NormSohl/openprinttag-weigh-station/docs/quickref-weighing.md

# Quick Reference — Weighing a Spool

*Print this page and keep it at the station. Full detail: [user-manual.md](user-manual.md).*

Weigh after every print if at all possible — plus before one, or any other
time.

## Steps

1. **Place the spool on the scale.** The scale starts reading the moment the
   spool lands.
2. **Wait a second or two.** The display settles on the spool number,
   material, and remaining weight.
3. **Remove the spool.** The reading is already saved. The display returns
   to idle.

**Weigh it when you return it — every time, if at all possible.** That's
what keeps remaining weight accurate for the next person. Weighing when you
take it out is useful too, and you can weigh a spool any other time you want
to check on it — none of that is required the way returning it is.

## What the display is telling you

| Screen | Meaning |
|---|---|
| Green, "Place spool to begin" | Idle — ready to go |
| "Weighing…" | Reading the load cell — don't lift yet |
| Spool #, material, grams, "Weight recorded" | Done — safe to remove |
| "Registered! / NEEDS ONBOARDING" | This is a brand-new tag — see the Onboarding quick-ref |
| Red "Read Error" | Reposition the spool so the tag centers over the reader |
| Orange, "Scale not calibrated" | Weights aren't trustworthy yet — flag for an admin |

## If something looks wrong

- **Read error every time in the same spot:** the tag antenna may be cracked —
  flag the spool for a new tag.
- **Weight looks way off:** don't fix it yourself — tell an admin, the scale
  may need recalibrating.
