NormSohl/openprinttag-weigh-station/src/web_app.cpp

// SPDX-License-Identifier: GPL-3.0-or-later
// Copyright (C) 2026 Norm Sohl

#include "web_app.h"
#include <Arduino.h>
#include <WiFi.h>
#include <ESPmDNS.h>
#include <ESPAsyncWebServer.h>
#include <LittleFS.h>
#include <vector>
#include <algorithm>
#include <string.h>
#include <stdlib.h>   // strtoull
#include "config.h"
#include "device_state.h"
#include "opt_tag.h"
#include "store.h"
#include "config_store.h"
#include "api_key.h"
#include "display_tz.h"
#include "station_name.h"
#include "last_onboard.h"
#include "last_stock.h"

// ── Shared globals (defined in main.cpp) ──────────────────────────────────────
extern volatile DeviceState gState;
extern SemaphoreHandle_t    gStateMutex;
extern volatile float       gWeightGrams;
extern SemaphoreHandle_t    gWeightMutex;
extern uint8_t              gTagUid[8];
extern OptMain              gTagMain;
extern SemaphoreHandle_t    gTagMutex;
// Set here (Start/Stop on /erase), consumed by nfcTask/syncTask — see main.cpp.
extern volatile bool        gEraseModeActive;
extern volatile uint32_t    gEraseModeActivityMs;
extern volatile bool        gWriteMainPending;
extern volatile int         gSpoolId;
extern volatile bool        gSpoolNeedsOnboarding;
extern volatile bool        gScaleCalibrated;
extern volatile bool        gCalZeroReq;
extern volatile float       gCalSetGrams;
// SoftAP SSID when the station fell back to its own AP; empty in station
// mode. Reported by /api/status.
extern char                 gApSsid[24];
extern volatile bool        gClockSet;

static AsyncWebServer sServer(80);

// Forward decl -- defined below, needed by the SSE push logic here so both
// the broadcast (webAppNotifyStateChanged) and the per-client catch-up
// (sEvents.onConnect(), registered in webAppBegin()) can send the SAME
// authoritative value.
static int currentSpool();

// Server-push channel for state changes, so a page like /onboard, a spool's
// detail page, or the Inventory page can react the instant something changes
// instead of polling. The message body carries the values a listener needs
// to decide for itself, not a bare ping -- a live test found that a bare
// ping requiring a follow-up fetch('/api/status') could silently stall: this
// server holds very few concurrent connections, and the fetch was losing the
// race against the already-open SSE stream for one. Format:
// "<spool id>,<needs_onboarding>,<audit phase 0/1/2>,<audit found>,<audit total>"
// (spool id -1 when nothing is on the scale). Each listener reads only the
// fields it cares about: /onboard and /spool watch the id; the Inventory
// page also watches the audit fields, and skips reloading entirely when
// none of the fields it cares about actually changed -- a live test found
// that reloading the whole page on every push (including ones that changed
// nothing this page shows, like reweighing an already-found spool during an
// audit) made a full-page flash on every placement, fighting anyone trying
// to scroll the list.
static AsyncEventSource sEvents("/events");

// Shared with handleRoot()'s own audit banner render, so the two can never
// silently drift into disagreeing about what "found" means.
static void auditSummary(AuditPhase& phase, uint32_t& total, uint32_t& found) {
    phase = storeAuditPhase();
    total = 0; found = 0;
    if (phase == AuditPhase::Idle) return;
    char startTs[25] = {};
    storeAuditStartTs(startTs, sizeof(startTs));
    SpoolRecord rr;
    for (size_t i = 0; i < storeSpoolCount(); i++) {
        if (!storeSpoolAt(i, rr)) continue;
        if (rr.retired || rr.remaining_g <= 1.0f) continue;
        total++;
        if (strcmp(rr.last_ts, startTs) >= 0) found++;
    }
}

static String currentScaleSpoolPayload() {
    int id = currentSpool();
    bool needsOb = false;
    if (id > 0) {
        SpoolRecord r;
        if (storeGetSpool((uint32_t)id, r)) needsOb = r.needs_ob;
    }
    AuditPhase phase; uint32_t total, found;
    auditSummary(phase, total, found);
    return String(id) + "," + (needsOb ? "1" : "0") + ","
         + String((int)phase) + "," + String(found) + "," + String(total);
}

void webAppNotifyStateChanged() {
    auto st = sEvents.send(currentScaleSpoolPayload().c_str(), "state");
    Serial.printf("[sse] state-change push: %u client(s), status=%d\n",
                  (unsigned)sEvents.count(), (int)st);
}

// ── Small HTML helpers ────────────────────────────────────────────────────────

// ── Auth ──────────────────────────────────────────────────────────────────────
// Applied to state-changing endpoints only; GETs stay open so dashboards and
// scrapers need no credentials. See api_key.h for the threat model and why an
// unset key deliberately leaves everything open.
//
// Returns true if the request may proceed. On refusal it has already sent the
// 401, so the caller must simply return.
static bool authOk(AsyncWebServerRequest* req) {
    if (!apiKeyIsSet()) return true;                 // not configured: open
    const String key = apiKeyGet();
    if (req->hasHeader("X-API-Key") && req->header("X-API-Key") == key) return true;
    if (req->hasParam("key") && req->getParam("key")->value() == key)   return true;
    // Basic auth accepts any username: the secret is the password. Lets browsers
    // prompt natively and `curl -u :secret` work without a header.
    if (req->authenticate("", key.c_str()) ||
        req->authenticate("admin", key.c_str()))     return true;
    req->requestAuthentication();                    // sends 401 + WWW-Authenticate
    return false;
}

// 32 lowercase hex chars (no dashes, matching the store's uuid format) -> 16
// bytes. Used only for catalog-sourced UUIDs coming off the onboard form —
// false on anything malformed, and the caller simply leaves the tag field
// untouched rather than writing a bogus identity.
static bool hex32ToBytes(const String& hex, uint8_t out[16]) {
    if (hex.length() != 32) return false;
    for (int i = 0; i < 16; i++) {
        char b[3] = { hex[i * 2], hex[i * 2 + 1], 0 };
        char* end = nullptr;
        long v = strtol(b, &end, 16);
        if (end != b + 2) return false;
        out[i] = (uint8_t)v;
    }
    return true;
}

static String esc(const char* s) {
    String o;
    for (const char* p = s; *p; ++p) {
        switch (*p) {
            case '&': o += "&amp;";  break;
            case '<': o += "&lt;";   break;
            case '>': o += "&gt;";   break;
            case '"': o += "&quot;"; break;
            default:  o += *p;       break;
        }
    }
    return o;
}

static const char* STYLE =
    "<style>"
    // -webkit-text-size-adjust stops iOS inflating text when a phone is turned
    // to landscape, which otherwise reflows every page unpredictably.
    "body{font-family:system-ui,sans-serif;margin:0;background:#111;color:#eee;"
    "-webkit-text-size-adjust:100%}"
    // Flex, not float. Eight nav links floated right do not fit a phone: they
    // collide with the title and wrap into an unreadable stack. Flex-wrap drops
    // them onto their own line instead, and margin-left:auto keeps them right-
    // aligned whenever there IS room.
    "header{background:#1c2b1c;padding:12px 16px;font-size:20px;font-weight:600;"
    "display:flex;flex-wrap:wrap;align-items:baseline}"
    "header nav{display:flex;flex-wrap:wrap;gap:4px 16px;margin-left:auto}"
    "header a{color:#8f8;text-decoration:none;font-size:15px;font-weight:400;"
    "padding:4px 0}"
    "header a.active{color:#fff;font-weight:600;border-bottom:2px solid #8f8}"
    // overflow-x on main, not on the page: a table wider than the phone scrolls
    // inside the content area instead of sliding the whole layout sideways,
    // which is the usual way a page "looks broken" on mobile.
    "main{padding:18px;max-width:760px;margin:0 auto;overflow-x:auto}"
    "table{border-collapse:collapse;width:100%}"
    "th,td{padding:6px 10px;text-align:left;border-bottom:1px solid #333}"
    "th{color:#9c9}"
    ".sw{display:inline-block;width:14px;height:14px;border-radius:3px;vertical-align:middle;margin-right:6px;border:1px solid #000}"
    // "No colour assigned" — a crossed-out square, so it cannot be misread as a
    // black filament. The stroke is a gradient rather than a glyph or an SVG so
    // it stays crisp at 14px and needs no extra request.
    ".sw0{background:#1c1c1c;border-color:#666;background-image:"
    "linear-gradient(to top right,transparent 45%,#8a8a8a 45%,#8a8a8a 55%,transparent 55%)}"
    ".ob{color:#fd6}"
    ".inv-row{cursor:pointer}"
    ".inv-row:hover{background:#1a1a1a}"
    ".arrow{display:inline-block;font-size:22px;line-height:1;color:#8f8}"
    "form label{display:block;margin:12px 0 4px;color:#9c9}"
    "select,input{font-size:16px;padding:8px;width:100%;box-sizing:border-box;background:#222;color:#eee;border:1px solid #444;border-radius:5px}"
    "button{margin-top:16px;font-size:16px;padding:10px 18px;background:#2a5;color:#000;border:0;border-radius:6px;cursor:pointer}"
    "button.sec{background:#345;color:#eee}"
    ".card{background:#1a1a1a;border:1px solid #333;border-radius:8px;padding:14px;margin-bottom:14px}"
    ".big{font-size:28px;font-weight:700}"
    ".muted{color:#888}"
    // Spec strip: the numbers onboarding stored, which are otherwise typed once
    // into the form and never seen again. Flex-wrap rather than a table so it
    // reflows to one item per line on a phone instead of scrolling.
    ".spec{display:flex;flex-wrap:wrap;gap:5px 16px;font-size:14px;color:#aaa;margin-top:10px}"
    ".spec b{color:#ddd;font-weight:600}"
    // Phone-width tuning. Tighter cells and slightly smaller type let the wider
    // tables (Usage has five columns) fit without scrolling at all on most
    // handsets; the ones that still don't fit scroll inside main.
    "@media(max-width:520px){"
      "main{padding:12px}"
      "header{font-size:18px;padding:10px 12px}"
      "th,td{padding:5px 6px;font-size:14px}"
      ".big{font-size:24px}"
      "button{width:100%;padding:12px 18px}"
      "button.sec{width:auto}"
    "}"
    "</style>";

// ── Onboard page: OpenPrintTag catalog search widget ──────────────────────────
// Cascading Vendor -> Material type -> Material combo boxes that live-search
// github.com/OpenPrintTag/openprinttag-database straight from the browser (the
// device is never in the loop — no firmware cost, no extra heap). A pick fills
// the hidden cat_* fields in the onboard form with the vendor's own GTIN, the
// three OPT identity UUIDs, and real print/bed temps when the material file
// carries them, instead of whatever a person free-types.
//
// Prototyped and verified against the live DB at tools/opt-catalog/prototype.html
// before landing here; this is the same logic, minus the standalone page chrome.
static const char* CATALOG_STYLE =
    "<style>"
    ".cat-status{font-size:12px;color:#888;margin:6px 0 14px}"
    ".cat-status b{color:#eee}"
    ".cat-status.err b{color:#fd6}"
    ".cat-field{margin-bottom:12px;position:relative}"
    ".cat-field.disabled{opacity:.45}"
    ".cat-field label{display:block;font-size:12px;color:#9c9;text-transform:uppercase;"
      "letter-spacing:.04em;margin-bottom:4px}"
    ".cat-input.picked{border-color:#2a5}"
    ".cat-panel{display:none;position:absolute;left:0;right:0;top:calc(100% + 2px);z-index:20;"
      "background:#1a1a1a;border:1px solid #444;border-radius:6px;max-height:260px;"
      "overflow-y:auto;box-shadow:0 10px 30px #0008}"
    ".cat-group{padding:6px 10px 2px;font-size:11px;color:#888;text-transform:uppercase;letter-spacing:.04em}"
    ".cat-divider{border-top:1px solid #333;margin:2px 0}"
    ".cat-empty{padding:10px;color:#888;font-size:13px}"
    ".cat-row{padding:10px;display:flex;justify-content:space-between;align-items:center;gap:8px;cursor:pointer}"
    ".cat-row:active,.cat-row.hi{background:#20263a}"
    ".cat-row .meta{color:#888;font-size:12px;white-space:nowrap}"
    "</style>";

static const char* CATALOG_SCRIPT = R"OPTJS(<script>
(function(){
const OWNER="OpenPrintTag", REPO="openprinttag-database", BRANCH="main";
const API=`https://api.github.com/repos/${OWNER}/${REPO}`;
const RAW=`https://raw.githubusercontent.com/${OWNER}/${REPO}/${BRANCH}/data`;
const PKG_PREFIX="data/material-packages/";
const TYPE_ENUM_URL="https://raw.githubusercontent.com/OpenPrintTag/openprinttag-specification/main/data/material_type_enum.yaml";

const $ = s => document.querySelector(s);
const statusEl=$("#cat-status"), resolvedEl=$("#cat-resolved");
let PACKAGES = [];
let brandNames = new Map();

function esc(s){ return String(s==null?"":s).replace(/[&<>"]/g, c=>({"&":"&amp;","<":"&lt;",">":"&gt;",'"':"&quot;"}[c])); }
function setStatus(html, err){ statusEl.className="cat-status"+(err?" err":""); statusEl.innerHTML=html; }

// ── minimal YAML subset parser (maps, nested maps, lists of scalars/maps) ────
function parseYaml(text){
  const lines=text.split(/\r?\n/).map(l=>l.replace(/\s+$/,"")).filter(l=>l.trim()!==""&&!/^\s*#/.test(l));
  let pos=0; const indentOf=l=>l.length-l.trimStart().length;
  const scalar=v=>{v=v.trim();
    if((v[0]==="'"&&v.endsWith("'"))||(v[0]==='"'&&v.endsWith('"')))return v.slice(1,-1);
    if(/^-?\d+$/.test(v))return v.length>15?v:parseInt(v,10);
    if(/^-?\d*\.\d+$/.test(v))return parseFloat(v); return v;};
  function parseMap(indent){const obj={};
    while(pos<lines.length){const line=lines[pos],ind=indentOf(line),t=line.trim();
      if(ind<indent)break; if(t.startsWith("- "))break;
      const m=t.match(/^([^:]+):\s*(.*)$/); if(!m){pos++;continue;}
      const key=m[1].trim(),val=m[2]; pos++;
      if(val===""){const nx=lines[pos];
        if(nx!==undefined){const ni=indentOf(nx);
          if(nx.trim().startsWith("- ")&&ni>=indent)obj[key]=parseList(ni);
          else if(ni>indent)obj[key]=parseMap(ni); else obj[key]=null;
        }else obj[key]=null;
      }else obj[key]=scalar(val);}
    return obj;}
  function parseList(indent){const arr=[];
    while(pos<lines.length){const line=lines[pos],ind=indentOf(line),t=line.trim();
      if(ind<indent||!t.startsWith("- "))break;
      const rest=t.slice(2),m=rest.match(/^([^:]+):\s*(.*)$/); pos++;
      if(m){const item={};item[m[1].trim()]=m[2]===""?null:scalar(m[2]);
        const child=ind+2;
        if(pos<lines.length&&indentOf(lines[pos])>=child&&!lines[pos].trim().startsWith("- "))
          Object.assign(item,parseMap(child));
        arr.push(item);}else arr.push(scalar(rest));}
    return arr;}
  return parseMap(0);
}
async function fetchText(url){ const r=await fetch(url,{cache:"no-store"}); if(!r.ok) throw new Error(`${r.status} ${r.statusText} for ${url}`); return r.text(); }
async function fetchYaml(url){ return parseYaml(await fetchText(url)); }

// ── index: one tree fetch (cached by data_hash) + one small type-enum fetch ──
async function loadIndex(){
  let hash="nohash";
  try { const man=await fetchText(`${RAW}/manifest.yaml`); hash=(man.match(/data_hash:\s*(\S+)/)||[])[1]||"nohash"; } catch(e){}

  const cacheKey="opt_pkgindex2_"+hash;
  const cached=localStorage.getItem(cacheKey);
  if(cached){ PACKAGES=JSON.parse(cached); setStatus(`${PACKAGES.length.toLocaleString()} packages <span class="muted">(cached)</span>`); }
  else {
    setStatus("Fetching catalog tree from GitHub (one request)&hellip;");
    const tree=JSON.parse(await fetchText(`${API}/git/trees/${BRANCH}?recursive=1`));
    PACKAGES=(tree.tree||[]).filter(e=>e.type==="blob"&&e.path.startsWith(PKG_PREFIX)&&e.path.endsWith(".yaml"))
      .map(e=>{const rel=e.path.slice(PKG_PREFIX.length); const brand=rel.split("/")[0];
        const file=rel.split("/").pop().replace(/\.yaml$/,"");
        return {path:e.path, brand, file};});
    try { localStorage.setItem(cacheKey, JSON.stringify(PACKAGES)); } catch(e){}
    for(let i=localStorage.length-1;i>=0;i--){ const k=localStorage.key(i); if(k&&k.startsWith("opt_pkgindex2_")&&k!==cacheKey) localStorage.removeItem(k); }
    setStatus(`${PACKAGES.length.toLocaleString()} packages <span class="muted">(fresh)</span>`);
  }

  // Type tokens: scan filenames for exact hyphen-delimited matches against the
  // OPT's own material_type_enum abbreviations. No per-item fetch. ~93% of
  // packages resolve a type; the rest fall into "Other" honestly rather than
  // guessing.
  try {
    const enumText=await fetchText(TYPE_ENUM_URL);
    const ABBR=new Set([...enumText.matchAll(/abbreviation:\s*(\S+)/g)].map(m=>m[1].toLowerCase()));
    PACKAGES.forEach(p=>{ p.typeTok = p.file.split("-").find(t=>ABBR.has(t)) || null; });
  } catch(e){ PACKAGES.forEach(p=>p.typeTok=null); }

  prefetchBrandNames();  // progressive; does not block the UI
}

async function prefetchBrandNames(){
  const slugs=[...new Set(PACKAGES.map(p=>p.brand))];
  await Promise.all(slugs.map(async slug=>{
    try { const b=await fetchYaml(`${RAW}/brands/${slug}.yaml`); if(b.name) brandNames.set(slug,b.name); } catch(e){}
  }));
  vendorCombo.renderPanel();  // refresh labels if the panel happens to be open
}

// ── small helpers ──────────────────────────────────────────────────────────
function prettifySlug(s){ return s.replace(/-/g," ").replace(/\b\w/g,c=>c.toUpperCase()); }
function prettyName(file, brand){
  let n=file.replace(/-/g," ");
  if(n.toLowerCase().startsWith(brand.replace(/-/g," ").toLowerCase()+" ")) n=n.slice(brand.length+1);
  return n.replace(/\b\w/g,c=>c.toUpperCase());
}
function weightBadge(file){
  let m=file.match(/-(\d+(?:\.\d+)?kg)(?:-(spool|old-spool|refill))?$/i);
  if(m) return m[1].toUpperCase().replace("KG"," kg") + (m[2]?` (${m[2].replace("-"," ")})`:"");
  m=file.match(/-(\d+)-(spool|old-spool|refill|no-spool)$/i);
  if(m) return `${m[1]} g` + (m[2]!=="spool" ? ` (${m[2].replace("-"," ")})` : "");
  return null;
}
function loadMru(key){ try { return JSON.parse(localStorage.getItem(key)||"[]"); } catch(e){ return []; } }
function pushMru(key,val,cap){ let a=loadMru(key).filter(v=>v!==val); a.unshift(val); a=a.slice(0,cap); localStorage.setItem(key,JSON.stringify(a)); }

// ── candidate lists (all client-side, zero extra fetches) ───────────────────
function vendorCandidates(){
  const counts=new Map();
  for(const p of PACKAGES) counts.set(p.brand,(counts.get(p.brand)||0)+1);
  return [...counts.entries()]
    .map(([slug,count])=>({value:slug, label:brandNames.get(slug)||prettifySlug(slug), count}))
    .sort((a,b)=>a.label.localeCompare(b.label));
}
function typeCandidatesFor(vendorSlug){
  const counts=new Map();
  for(const p of PACKAGES){ if(p.brand!==vendorSlug) continue; const tok=p.typeTok||"other"; counts.set(tok,(counts.get(tok)||0)+1); }
  const total=[...counts.values()].reduce((a,b)=>a+b,0);
  const rows=[{value:"", label:"All types", count:total}];
  for(const [tok,count] of [...counts.entries()].sort((a,b)=>b[1]-a[1]))
    rows.push({value:tok, label: tok==="other" ? "Other / unspecified" : tok.toUpperCase(), count});
  return rows;
}
function materialCandidatesFor(vendorSlug, typeTok){
  return PACKAGES.filter(p=>p.brand===vendorSlug && (!typeTok || p.typeTok===typeTok))
    .map(p=>{
      const badge=weightBadge(p.file);
      return { value:p.path, label:prettyName(p.file,p.brand)+(badge?` — ${badge}`:"") };
    })
    .sort((a,b)=> a.label.localeCompare(b.label));
}

// ── reusable combo box: MRU (if any) → divider → list; type-to-filter ────────
function makeCombo(fieldId, inputId, panelId, placeholder){
  const field=$(fieldId), input=$(inputId), panel=$(panelId);
  let candidatesFn=()=>[], mruKey=null, mruCap=0, onPick=()=>{};
  let rows=[], hiIdx=-1;

  function setSource(cfg){ candidatesFn=cfg.candidatesFn; mruKey=cfg.mruKey||null; mruCap=cfg.mruCap||0; onPick=cfg.onPick; }
  function rowHtml(c,i){
    return `<div class="cat-row${i===hiIdx?" hi":""}" data-i="${i}">`+
      `<span>${esc(c.label)}</span>`+
      (c.count!=null?`<span class="meta">${c.count}</span>`:"")+`</div>`;
  }
  function renderPanel(){
    const all=candidatesFn();
    const filt=input.value.trim().toLowerCase();
    const terms=filt.split(/\s+/).filter(Boolean);
    const match=c=>terms.every(t=>c.label.toLowerCase().includes(t));
    const mruVals=(!filt && mruKey) ? loadMru(mruKey) : [];
    const mruRows=mruVals.map(v=>all.find(c=>c.value===v)).filter(Boolean);
    let rest=all.filter(c=>!mruRows.includes(c));
    if(filt) rest=rest.filter(match);
    rest=rest.slice(0,80);
    rows=[...mruRows, ...rest];
    hiIdx=-1;
    panel.innerHTML =
      (mruRows.length? `<div class="cat-group">Recently used</div>${mruRows.map((c,i)=>rowHtml(c,i)).join("")}<div class="cat-divider"></div>` : "") +
      (rest.length ? rest.map((c,i)=>rowHtml(c,mruRows.length+i)).join("")
                   : (all.length ? `<div class="cat-empty">No matches</div>` : `<div class="cat-empty">Nothing here yet</div>`));
  }
  function show(){ if(input.disabled) return; renderPanel(); panel.style.display="block"; }
  function hide(){ panel.style.display="none"; }
  function pick(c){
    input.value=c.label; input.classList.add("picked"); hide();
    if(mruKey) pushMru(mruKey, c.value, mruCap);
    onPick(c);
  }
  input.addEventListener("focus", show);
  input.addEventListener("input", ()=>{ input.classList.remove("picked"); show(); });
  input.addEventListener("blur", ()=> setTimeout(hide, 150));
  input.addEventListener("keydown", e=>{
    if(panel.style.display!=="block") return;
    if(e.key==="ArrowDown"){ e.preventDefault(); hiIdx=Math.min(hiIdx+1, rows.length-1); renderHi(); }
    else if(e.key==="ArrowUp"){ e.preventDefault(); hiIdx=Math.max(hiIdx-1, 0); renderHi(); }
    else if(e.key==="Enter"){ e.preventDefault(); if(rows[hiIdx]) pick(rows[hiIdx]); }
    else if(e.key==="Escape"){ hide(); }
  });
  function renderHi(){ panel.querySelectorAll(".cat-row").forEach(r=>r.classList.toggle("hi", +r.dataset.i===hiIdx)); }
  panel.addEventListener("mousedown", e=>{
    const row=e.target.closest(".cat-row[data-i]"); if(!row) return;
    e.preventDefault(); pick(rows[+row.dataset.i]);
  });
  function reset(){ input.value=""; input.classList.remove("picked"); }
  function enable(text){ input.disabled=false; input.placeholder=text||placeholder; field.classList.remove("disabled"); }
  function disable(text){ input.disabled=true; reset(); input.placeholder=text; field.classList.add("disabled"); }
  return { setSource, reset, enable, disable, renderPanel };
}

const vendorCombo   = makeCombo("#cat-field-vendor",   "#cat-in-vendor",   "#cat-panel-vendor",   "Type or tap to browse vendors…");
const typeCombo     = makeCombo("#cat-field-type",     "#cat-in-type",     "#cat-panel-type",     "Type or tap to browse types…");
const materialCombo = makeCombo("#cat-field-material", "#cat-in-material", "#cat-panel-material", "Type or tap to browse materials…");
typeCombo.disable("Pick a vendor first");
materialCombo.disable("Pick a vendor first");

vendorCombo.setSource({
  candidatesFn: vendorCandidates,
  mruKey: "opt_mru_vendor", mruCap: 3,
  onPick(c){
    typeCombo.reset(); typeCombo.enable();
    materialCombo.disable("Pick a material type first");
    resolvedEl.innerHTML = "";
    typeCombo.setSource({
      candidatesFn: ()=>typeCandidatesFor(c.value),
      mruKey: "opt_mru_type", mruCap: 4,
      onPick(tc){
        materialCombo.reset(); materialCombo.enable();
        resolvedEl.innerHTML = "";
        materialCombo.setSource({
          candidatesFn: ()=>materialCandidatesFor(c.value, tc.value || null),
          onPick(mc){ resolvePick(mc.value); }
        });
      }
    });
  }
});

// ── resolve a picked package: package → material + container + brand, then
//    fill the form's hidden cat_* fields with the authoritative values ───────
function stripDash(u){ return (u||"").replace(/-/g,""); }
function setField(name, val){ const el=$("#cat-f-"+name); if(el) el.value = (val==null?"":val); }

async function resolvePick(pkgPath){
  resolvedEl.innerHTML = "<p class='muted'>Resolving…</p>";
  const brandSlug = pkgPath.slice(PKG_PREFIX.length).split("/")[0];
  try {
    const pkg = await fetchYaml(`${RAW}/material-packages/${brandSlug}/${pkgPath.split("/").pop()}`);
    const matSlug = pkg.material && pkg.material.slug, contSlug = pkg.container && pkg.container.slug;
    const [mat, cont, brand] = await Promise.all([
      matSlug  ? fetchYaml(`${RAW}/materials/${brandSlug}/${matSlug}.yaml`)       : Promise.resolve({}),
      contSlug ? fetchYaml(`${RAW}/material-containers/${contSlug}.yaml`)         : Promise.resolve({}),
                 fetchYaml(`${RAW}/brands/${brandSlug}.yaml`).catch(()=>({})),
    ]);
    applyPick(pkg, mat, cont, brand, brandSlug);
  } catch(e){
    resolvedEl.innerHTML = `<p class="ob">Couldn't resolve that pick: ${esc(e.message)}</p>`;
  }
}

function applyPick(pkg, mat, cont, brand, brandSlug){
  const rgba = (mat.primary_color && mat.primary_color.color_rgba) || "";
  const dia  = pkg.filament_diameter ? (pkg.filament_diameter/1000) : null;
  const tare = (cont.empty_weight != null) ? cont.empty_weight : null;
  const props = mat.properties || {};
  const tempKeys = ["min_print_temperature","max_print_temperature","min_bed_temperature","max_bed_temperature"];
  const haveTemps = tempKeys.every(k => typeof props[k] === "number");

  const vendor = brand.name || prettifySlug(brandSlug);
  const material = mat.name || "";
  const abbr = mat.abbreviation || mat.type || "";

  setField("cat_vendor", vendor);
  setField("cat_material", material);
  setField("cat_abbr", abbr);
  setField("cat_rgba", rgba ? rgba.replace("#","") : "");
  setField("cat_dia", dia);
  setField("cat_nom_g", pkg.nominal_netto_full_weight);
  setField("cat_empty_g", tare);
  setField("cat_gtin", pkg.gtin != null ? String(pkg.gtin) : "");
  setField("cat_pkg_uuid", stripDash(pkg.uuid));
  setField("cat_mat_uuid", stripDash(mat.uuid));
  setField("cat_brand_uuid", stripDash(brand.uuid));
  if (haveTemps) {
    setField("cat_print_min", props.min_print_temperature);
    setField("cat_print_max", props.max_print_temperature);
    setField("cat_bed_min",   props.min_bed_temperature);
    setField("cat_bed_max",   props.max_bed_temperature);
  } else {
    setField("cat_print_min",""); setField("cat_print_max","");
    setField("cat_bed_min","");   setField("cat_bed_max","");
  }
  $("#cat-source").value = "catalog";

  const sw = rgba ? `<span class="sw" style="background:${esc(rgba.slice(0,7))}"></span>` : "";
  const missTare = tare==null ? " <span class='ob'>&mdash; missing; capture below</span>" : "";
  resolvedEl.innerHTML =
    `<div class="card" style="border-color:#2a5;margin-top:10px">` +
    `<div style="font-size:17px;font-weight:600">${sw}${esc(vendor)} ${esc(material)}</div>` +
    `<p class="muted">${esc(abbr)}` +
      (dia!=null?` &middot; ${dia.toFixed(2)} mm`:``) +
      (pkg.nominal_netto_full_weight?` &middot; ${pkg.nominal_netto_full_weight} g`:``) +
      ` &middot; tare ${tare!=null?tare+" g":"unknown"}${missTare}</p>` +
    `<p class="muted" style="font-size:12px">GTIN ${pkg.gtin||"&mdash;"}` +
      (haveTemps ? ` &middot; print ${props.min_print_temperature}&ndash;${props.max_print_temperature}&deg;C` : ``) +
    `</p></div>`;
}

// ── boot ──────────────────────────────────────────────────────────────────
(async () => {
  try {
    await loadIndex();
    vendorCombo.enable();
    setStatus(`${PACKAGES.length.toLocaleString()} packages, ${new Set(PACKAGES.map(p=>p.brand)).size} vendors ready.`);
  } catch(e){
    setStatus(`Couldn't load the catalog: <b>${esc(e.message)}</b> &mdash; use manual entry below.`, true);
    const det = document.getElementById("cat-manual-details");
    if (det) det.open = true;
  }
})();
})();
</script>)OPTJS";

// One nav link, marked `active` when its href matches the current page.
static void navlink(String& h, const char* href, const char* label, const char* active) {
    h += "<a href='";
    h += href;
    h += (strcmp(href, active) == 0) ? "' class='active'>" : "'>";
    h += label;
    h += "</a>";
}

// `active` = the nav href for the current page (e.g. "/reorder"); "" = none.
static String head(const char* title, const char* active = "") {
    String h = "<!DOCTYPE html><html><head><meta charset='utf-8'>"
               "<meta name='viewport' content='width=device-width,initial-scale=1'>"
               "<title>";
    h += title;
    h += "</title>";
    h += STYLE;
    h += "</head><body><header>Weigh Station<nav>";
    navlink(h, "/",          "Inventory", active);
    navlink(h, "/onboard",   "Onboard",   active);
    navlink(h, "/reorder",   "Reorder",   active);
    navlink(h, "/stock",     "Stock List", active);
    navlink(h, "/usage",     "Usage",     active);
    navlink(h, "/erase",     "Erase Tag", active);
    navlink(h, "/config",    "Settings",  active);
    navlink(h, "/backup",    "Backup",    active);
    h += "</nav></header><main>";
    return h;
}

static const char* FOOT = "</main></body></html>";

// ── Current spool on the scale ────────────────────────────────────────────────
// Returns the local spool id if a tag is presently weighed/registered, else -1.
static int currentSpool() {
    xSemaphoreTake(gStateMutex, portMAX_DELAY);
    DeviceState s = gState;
    xSemaphoreGive(gStateMutex);
    bool live = (s == DeviceState::Present || s == DeviceState::WeighingAndSync ||
                 s == DeviceState::ReconcilingMainSection);
    return (live && gSpoolId > 0) ? gSpoolId : -1;
}

// Colour swatch, with a distinct "not assigned" rendering.
//
// alpha == 0 means no colour has been entered (see StoreEvent::rgba). Drawing
// that as #000000 would claim the spool is black, which is both wrong and
// unfalsifiable — nobody looking at the page could tell the difference. A
// crossed-out square says "unknown", and stays sayable if the colour is
// measured and filled in later.
static String swatch(const uint8_t rgba[4]) {
    if (rgba[3] == 0)
        return "<span class='sw sw0' title='No colour assigned'></span>";
    char b[80];
    snprintf(b, sizeof(b),
             "<span class='sw' style='background:#%02x%02x%02x'></span>",
             rgba[0], rgba[1], rgba[2]);
    return String(b);
}

// JSON value for a colour: the hex string, or null when none is assigned.
// Emitting "000000" would make an unassigned colour indistinguishable from
// black to every consumer, which is the same mistake the swatch avoids.
static String colorJson(const uint8_t rgba[4]) {
    if (rgba[3] == 0) return "null";
    char b[10];
    snprintf(b, sizeof(b), "\"%02x%02x%02x\"", rgba[0], rgba[1], rgba[2]);
    return String(b);
}

// One "label value" item for a .spec strip.
static String kv(const char* label, const String& value) {
    return "<span><b>" + String(label) + "</b> " + value + "</span>";
}

// The physical numbers a spool record carries: the tare, nominal weight and
// diameter chosen during onboarding.
//
// These exist only because someone typed them into the Onboard form, and until
// now nothing displayed them back — so a wrong spool profile (the commonest
// onboarding mistake, and the one that makes every later remaining-weight
// wrong) was invisible. Omit anything still zero rather than printing "0 g",
// which reads like a measurement instead of a blank — except the tare, which
// is shown even when missing: it is never meant to be unknown, and remaining
// is gross minus tare, so a missing one is a wrong number worth pointing at
// (the same reasoning as cost's "not recorded").
static String specStrip(const SpoolRecord& r) {
    String s;
    s += kv("Tare", r.empty_g > 0.0f ? String(r.empty_g, 0) + " g"
                                     : String("<span class='ob'>not recorded</span>"));
    if (r.nom_g   > 0.0f) s += kv("Nominal", String(r.nom_g,   0) + " g");
    if (r.dia     > 0.0f) s += kv("&Oslash;",  String(r.dia,   2) + " mm");
    return s;
}

// ── Dashboard: material roll-up + current spool ───────────────────────────────
static void handleRoot(AsyncWebServerRequest* req) {
    String p = head("Inventory", "/");

    if (!gScaleCalibrated)
        p += "<div class='card' style='border-color:#a70'>"
             "<b class='ob'>Scale not calibrated.</b> Weights will be wrong until "
             "you <a href='/calibrate' style='color:#fd6'>calibrate the scale</a>.</div>";

    // ── Physical inventory audit ────────────────────────────────────────────
    // "We weigh and scan every reel in the library" -- state lives entirely in
    // the log (storeAuditPhase() derives it), so this bar is correct even right
    // after a reboot mid-audit. A spool counts as found simply by having been
    // weighed since audit_start; nothing about normal weighing changes.
    AuditPhase auditPhase; uint32_t auditTotal, auditFound;
    auditSummary(auditPhase, auditTotal, auditFound);
    char auditStartTs[25] = {};
    storeAuditStartTs(auditStartTs, sizeof(auditStartTs));

    // retiredCount is unrelated to the audit fold above, so it's a separate
    // pass rather than folded into auditSummary() -- keeps that helper's
    // contract to exactly what the /events payload needs.
    uint32_t retiredCount = 0;
    {
        SpoolRecord rr;
        for (size_t i = 0; i < storeSpoolCount(); i++)
            if (storeSpoolAt(i, rr) && rr.retired) retiredCount++;
    }

    if (auditPhase == AuditPhase::Idle) {
        p += "<div class='card'><label style='margin-top:0'>Physical inventory</label>"
             "<p class='muted'>Weigh and scan every reel in the library. Anything not "
             "seen by the end gets reviewed before it's marked disposed.</p>"
             "<form method='POST' action='/api/audit/start'>"
             "<button type='submit'>Start audit</button></form></div>";
    } else if (auditPhase == AuditPhase::Scanning) {
        p += "<div class='card' style='border-color:#2a5'><label style='margin-top:0'>"
             "Audit in progress</label><p><b>" + String(auditFound) + " of " + String(auditTotal)
           + "</b> found so far. Weigh spools as normal &mdash; each expanded row below "
             "shows found status.</p>"
             "<form method='POST' action='/api/audit/finish' style='display:inline'>"
             "<button type='submit'>Finish audit</button></form> "
             "<form method='POST' action='/api/audit/abandon' style='display:inline' "
             "onsubmit=\"return confirm('Abandon this audit? Nothing already found is "
             "affected, but the audit itself ends with no review.')\">"
             "<button type='submit' class='sec'>Abandon audit</button></form></div>";
    } else {  // Resolving
        uint32_t notFound = auditTotal - auditFound;
        p += "<div class='card' style='border-color:#a70'><label style='margin-top:0'>"
             "Audit &mdash; resolving</label><p><b class='ob'>" + String(notFound)
           + " spool(s) not found.</b> Mark each Closed (confirmed disposed) or Found "
             "below before this audit can complete. Still weighable normally &mdash; "
             "weighing one resolves it too.</p>"
             "<form method='POST' action='/api/audit/abandon' "
             "onsubmit=\"return confirm('Abandon this audit? Nothing already closed or "
             "found is affected, but the remaining not-found spools stay unresolved.')\">"
             "<button type='submit' class='sec'>Abandon audit</button></form></div>";
    }

    int cur = currentSpool();
    if (cur > 0) {
        SpoolRecord r;
        if (storeGetSpool((uint32_t)cur, r)) {
            p += "<div class='card'>";
            p += "<div class='muted'>On the scale now</div>";
            p += "<div class='big'><a href='/spool?id=" + String((unsigned)r.spool)
               + "' style='color:inherit;text-decoration:none'>"
               + swatch(r.rgba) + "#" + String((unsigned)r.spool)
               + " " + esc(r.material[0] ? r.material : "Unknown") + "</a></div>";
            if (r.needs_ob) {
                p += "<p class='ob'>Needs onboarding &mdash; "
                     "<a href='/onboard' style='color:#fd6'>add details</a></p>";
            } else {
                p += "<p class='muted'>" + esc(r.vendor)
                   + (r.abbr[0] ? " &middot; " + esc(r.abbr) : String())
                   + " &middot; " + String(r.remaining_g, 0) + " grams remaining &middot; "
                   + String(r.used_g, 0) + " grams used</p>";

                // Spec strip, plus the print temperatures. The temps are not in
                // the store record at all — they live on the tag, so read them
                // from the decoded Main section of whatever is on the scale.
                // This card is the only place they can be shown, and they are
                // what a member actually wants when setting up a print.
                String spec = specStrip(r);
                OptMain t;
                xSemaphoreTake(gTagMutex, portMAX_DELAY);
                t = gTagMain;
                xSemaphoreGive(gTagMutex);
                if (t.max_print_temperature > 0)
                    spec += kv("Nozzle", String(t.min_print_temperature) + "&ndash;"
                                       + String(t.max_print_temperature) + " &deg;C");
                if (t.max_bed_temperature > 0)
                    spec += kv("Bed", String(t.min_bed_temperature) + "&ndash;"
                                    + String(t.max_bed_temperature) + " &deg;C");
                if (spec.length()) p += "<div class='spec'>" + spec + "</div>";
            }
            p += "</div>";
        }
    }

    // Rows are OPT display strings now ("PLA Summer Grass"), not bare material
    // types, so several spools of the same product roll up into one line.
    // Bucketed by (vendor, material) — see MatInventory's comment in store.h —
    // so the vendor prefix here ("eSun PLA Summer Grass") is always a single
    // vendor's, never a merge of two.
    // Click a row to expand it in place — the individual spools behind that
    // count, scoped to just this (vendor, material) bucket. This IS the
    // spool list now; there is no separate /spools page any more. No fetch:
    // the detail rows are server-rendered right
    // here and hidden with display:none, so expanding costs nothing over the
    // network, only a bit more HTML in the initial page load. Filtered to
    // remaining_g > 1 g, same as m.count itself, so the row count in the
    // summary always matches the number of rows revealed underneath it —
    // showing every last near-empty spool here would make that number lie.
    const bool showRetired = req->hasParam("retired");
    p += "<p class='muted'>" + String(retiredCount) + " spool(s) retired &mdash; "
       + (showRetired
           ? "<a href='/' style='color:#8f8'>hide</a>"
           : "<a href='/?retired=1' style='color:#8f8'>show</a>")
       + "</p>";

    p += "<h3>Inventory</h3><table>"
         "<tr><th style='width:2em'></th><th>Filament</th><th>Spools</th><th>Remaining</th></tr>";
    size_t n = storeInventoryCount();
    MatInventory m;
    if (n == 0) p += "<tr><td colspan='4' class='muted'>No spools yet</td></tr>";
    for (size_t i = 0; i < n; i++) {
        if (!storeInventoryAt(i, m)) continue;
        String label = m.vendor[0] ? String(m.vendor) + " " + m.material : String(m.material);
        String rowId = "inv-detail-" + String((unsigned)i);

        // Build the detail rows first so the summary row above them can carry
        // a "not found" badge -- needs to know before it renders, not after.
        String detail = "<table style='margin:2px 0 10px'><tr><th>Spool #</th>"
                         "<th>Remaining</th><th></th></tr>";
        uint32_t bucketNotFound = 0;
        SpoolRecord r;
        size_t sn = storeSpoolCount();
        for (size_t k = 0; k < sn; k++) {
            if (!storeSpoolAt(k, r)) continue;
            if (strcmp(r.vendor, m.vendor) != 0 || strcmp(r.material, m.material) != 0) continue;
            if (r.retired) {
                if (!showRetired) continue;
                detail += "<tr style='opacity:.6'><td><a href='/spool?id=" + String((unsigned)r.spool)
                        + "' style='color:#8f8'>#" + String((unsigned)r.spool) + "</a></td><td>0 g</td>"
                          "<td class='muted'>retired</td></tr>";
                continue;
            }
            if (r.remaining_g <= 1.0f) continue;
            const bool found = (auditPhase == AuditPhase::Idle) ||
                                (strcmp(r.last_ts, auditStartTs) >= 0);
            if (!found) bucketNotFound++;
            detail += "<tr><td><a href='/spool?id=" + String((unsigned)r.spool)
                     + "' style='color:#8f8'>#" + String((unsigned)r.spool) + "</a></td><td>"
                     + String(r.remaining_g, 0) + " g</td><td>";
            if (r.needs_ob) detail += "<span class='ob'>needs onboarding</span> ";
            if (auditPhase == AuditPhase::Scanning) {
                detail += found ? "<span style='color:#8f8'>found</span>"
                                : "<span class='muted'>not yet found</span>";
            } else if (auditPhase == AuditPhase::Resolving && !found) {
                detail += "<form method='POST' action='/api/audit/close' style='display:inline' "
                           "onsubmit=\"return confirm('Confirm spool #" + String((unsigned)r.spool)
                         + " is disposed? This cannot be undone.')\">"
                           "<input type='hidden' name='spool' value='" + String((unsigned)r.spool) + "'>"
                           "<button type='submit' style='background:#522;color:#eee;margin:0;padding:4px 10px;"
                           "font-size:13px;border-radius:4px;border:0;cursor:pointer'>Close</button></form> "
                           "<form method='POST' action='/api/audit/found' style='display:inline'>"
                           "<input type='hidden' name='spool' value='" + String((unsigned)r.spool) + "'>"
                           "<button type='submit' style='margin:0;padding:4px 10px;font-size:13px'>Found</button>"
                           "</form>";
            }
            detail += "</td></tr>";
        }
        detail += "</table>";

        p += "<tr class='inv-row' onclick=\"var d=document.getElementById('" + rowId + "');"
             "var open=d.style.display=='table-row';d.style.display=open?'none':'table-row';"
             "this.querySelector('.arrow').textContent=open?'\\u25b8':'\\u25be'\">"
             "<td class='muted'><span class='arrow'>&#9656;</span></td><td>"
           + swatch(m.rgba) + esc(label.c_str())
           + (bucketNotFound ? " <span class='ob'>(" + String(bucketNotFound) + " not found)</span>" : "")
           + "</td><td>" + String(m.count) + "</td><td>" + String(m.remaining_g, 0) + " g</td></tr>";
        p += "<tr id='" + rowId + "' style='display:none'><td></td><td colspan='3'>" + detail + "</td></tr>";
    }
    p += "</table>";
    p += "<p class='muted'>" + String((unsigned)storeSpoolCount())
       + " spools tracked &middot; " + String((unsigned)storeLogLineCount())
       + " log entries</p>";
    // This page has no live-refresh of its own, so an audit's found/not-found
    // counts (and everything else here) just sit stale in an open tab while
    // spools are weighed elsewhere -- found on a live audit test where the
    // counts genuinely were updating, just not on screen without a manual
    // reload. Listen on the same /events channel every other page uses.
    //
    // Reloading on every push (as a first cut did) meant a full-page flash
    // on every placement, including ones that changed nothing this page
    // shows -- reweighing an already-found spool during an audit still
    // fired a push, since the push is keyed on device state, not on this
    // page's content. Compare the fields that actually appear here (the
    // audit phase/found/total, and whatever's on the scale) against what
    // was true when this page was rendered, and only reload when one of
    // them actually differs. Debounced too: a fast run of several state
    // changes in a row (e.g. a blank-tag registration) collapses into one
    // reload after things settle, rather than reloading this page's full
    // (and comparatively heavy) inventory table once per intermediate state.
    //
    // A plain reload always lands back at the top -- confirmed on a live
    // audit test to make scrolling through the list fight the page every few
    // seconds. Stash the scroll position in sessionStorage right before
    // reloading and restore it on the next load, so a reload someone doesn't
    // even need to notice doesn't yank them back to row one.
    p += "<script>(function(){"
         "var Y='invScrollY',y=sessionStorage.getItem(Y);"
         "if(y!==null){window.scrollTo(0,parseInt(y,10));sessionStorage.removeItem(Y);}"
         "var base='" + String(cur) + "," + String((int)auditPhase) + ","
                       + String(auditFound) + "," + String(auditTotal) + "';"
         "var t=null;"
         "new EventSource('/events').addEventListener('state',function(e){"
           "var f=e.data.split(',');"
           "var sig=f[0]+','+f[2]+','+f[3]+','+f[4];"
           "if(sig===base)return;"
           "clearTimeout(t);t=setTimeout(function(){"
             "sessionStorage.setItem(Y,window.scrollY);location.reload();"
           "},400);"
         "});"
         "})();</script>";
    p += FOOT;
    req->send(200, "text/html", p);
}

// ── JSON API: spools ──────────────────────────────────────────────────────────
static void handleApiSpools(AsyncWebServerRequest* req) {
    String j = "[";
    size_t n = storeSpoolCount();
    SpoolRecord r;
    for (size_t i = 0; i < n; i++) {
        if (!storeSpoolAt(i, r)) continue;
        if (j.length() > 1) j += ",";
        j += "{\"spool\":" + String((unsigned)r.spool)
           + ",\"uuid\":\"" + r.uuid + "\""
           + ",\"vendor\":\"" + esc(r.vendor) + "\""
           + ",\"material\":\"" + esc(r.material) + "\""
           + ",\"color\":" + colorJson(r.rgba)
           + ",\"remaining_g\":" + String(r.remaining_g, 1)
           + ",\"used_g\":" + String(r.used_g, 1)
           // null, not 0: a spool predating products has no product, which is
           // not the same as belonging to product zero.
           + ",\"product\":" + (r.product ? String((unsigned)r.product) : String("null"))
           // Same rule, same reason: no price on record is not a free spool.
           // Exposed so "which spools still need a price?" is answerable
           // without walking every detail page by hand.
           + ",\"cost\":" + (r.cost > 0.0f ? String(r.cost, 2) : String("null"))
           + ",\"needs_onboarding\":" + (r.needs_ob ? "true" : "false")
           + ",\"retired\":" + (r.retired ? "true" : "false") + "}";
    }
    j += "]";
    req->send(200, "application/json", j);
}

// ── Physical inventory audit ────────────────────────────────────────────────
// Each of these changes the audit phase/found/total signature the Inventory
// page's live-refresh compares against, but none goes through controller_
// task.cpp's setState() (they're store events, not device states) -- so
// without an explicit push here, that comparison would have nothing to
// react to until an unrelated weigh happened to fire one.
static void handleApiAuditStart(AsyncWebServerRequest* req) {
    if (!authOk(req)) return;
    storeAuditStart();
    webAppNotifyStateChanged();
    req->redirect("/");
}
static void handleApiAuditFinish(AsyncWebServerRequest* req) {
    if (!authOk(req)) return;
    storeAuditFinish();
    webAppNotifyStateChanged();
    req->redirect("/");
}
static void handleApiAuditAbandon(AsyncWebServerRequest* req) {
    if (!authOk(req)) return;
    storeAuditAbandon();
    webAppNotifyStateChanged();
    req->redirect("/");
}
static void handleApiAuditClose(AsyncWebServerRequest* req) {
    if (!authOk(req)) return;
    const AsyncWebParameter* ps = req->getParam("spool", true);
    if (!ps) { req->send(400, "text/plain", "missing spool"); return; }
    storeRetireSpool((uint32_t)ps->value().toInt());
    webAppNotifyStateChanged();
    req->redirect("/");
}
static void handleApiAuditFound(AsyncWebServerRequest* req) {
    if (!authOk(req)) return;
    const AsyncWebParameter* ps = req->getParam("spool", true);
    if (!ps) { req->send(400, "text/plain", "missing spool"); return; }
    storeAuditFound((uint32_t)ps->value().toInt());
    webAppNotifyStateChanged();
    req->redirect("/");
}

// ── Products ──────────────────────────────────────────────────────────────────
// The page that answers "is adoption converging?". If the same filament appears
// twice here, the matching ladder missed — and nothing else in the app would
// show that, because two products with the same name roll up into one
// inventory row and look correct.
static void handleProducts(AsyncWebServerRequest* req) {
    String p = head("Products", "/products");
    p += "<h3>Products</h3>"
         "<p class='muted'>What we stock, as opposed to the individual spools on "
         "the shelf. A spool inherits its vendor, filament, colour, tare and "
         "nominal weight from its product.</p>";

    // Snapshot the products once. Matching each spool to its product is
    // inherently O(spools x products); doing it against a local copy keeps the
    // store lock out of the inner loop rather than taking it thousands of times.
    std::vector<uint32_t> ids;
    {
        ProductRecord q;
        for (size_t i = 0; i < storeProductCount(); i++)
            if (storeProductAt(i, q)) ids.push_back(q.id);
    }
    const size_t np = ids.size();
    std::vector<uint16_t> spoolsPer(np, 0);
    std::vector<float>    remPer(np, 0.0f);
    uint16_t unassigned = 0;
    {
        SpoolRecord r;
        for (size_t i = 0; i < storeSpoolCount(); i++) {
            if (!storeSpoolAt(i, r)) continue;
            if (!r.product) { unassigned++; continue; }
            for (size_t k = 0; k < np; k++)
                if (ids[k] == r.product) {
                    spoolsPer[k]++; remPer[k] += r.remaining_g; break;
                }
        }
    }

    p += "<table><tr><th>#</th><th>Filament</th><th>Vendor</th><th>Spools</th>"
         "<th>Remaining</th><th>Tare</th><th>Nominal</th><th></th></tr>";
    if (np == 0)
        p += "<tr><td colspan='8' class='muted'>No products yet — onboard a spool "
             "or place a tagged one on the scale</td></tr>";
    // By id, not by index: a spool placed on the scale mid-request can append a
    // product, and re-indexing would then attribute the counts to the wrong row.
    ProductRecord q;
    for (size_t i = 0; i < np; i++) {
        if (!storeGetProduct(ids[i], q)) continue;
        p += "<tr><td><a href='/product?id=" + String((unsigned)q.id)
           + "' style='color:#8f8'>#" + String((unsigned)q.id) + "</a></td><td>"
           + swatch(q.rgba)
           + esc(q.material[0] ? q.material : "Unknown")
           + (q.abbr[0] ? " <span class='muted'>" + esc(q.abbr) + "</span>" : String())
           + "</td><td>" + esc(q.vendor)
           + "</td><td>" + String((unsigned)spoolsPer[i])
           + "</td><td>" + String(remPer[i], 0) + " g"
           + "</td><td>" + (q.empty_g > 0 ? String(q.empty_g, 0) + " g"
                                           : String("<span class='ob'>not recorded</span>"))
           + "</td><td>" + (q.nom_g   > 0 ? String(q.nom_g,   0) + " g" : String("&mdash;"))
           + "</td><td>"
           // Provisional means this was inferred from a tag and no human has
           // confirmed it, which is why it is excluded from tag write-back.
           + (q.provisional ? "<span class='ob'>provisional</span>" : "")
           + "</td></tr>";
    }
    p += "</table>";
    if (unassigned)
        p += "<p class='muted'>" + String((unsigned)unassigned)
           + " spool(s) predate products and have none assigned. They keep working; "
             "re-onboarding one assigns it.</p>";
    p += FOOT;
    req->send(200, "text/html", p);
}

// ── One product: edit, and propagate the edit to its spools ───────────────────
//
// This is the page the whole model exists for: correct a wrong tare or a
// misspelled name once, and every spool of that filament follows — including
// their physical tags, on next placement.
static void handleProductDetail(AsyncWebServerRequest* req) {
    if (!req->hasParam("id")) { req->send(400, "text/plain", "missing id"); return; }
    uint32_t id = (uint32_t)req->getParam("id")->value().toInt();
    ProductRecord q;
    if (!storeGetProduct(id, q)) { req->send(404, "text/plain", "unknown product"); return; }

    // Which spools this edit would reach. Saying so up front is the point: an
    // edit here is not local, and the page should not pretend it is.
    std::vector<uint32_t> mine;
    {
        SpoolRecord r;
        for (size_t i = 0; i < storeSpoolCount(); i++)
            if (storeSpoolAt(i, r) && r.product == id) mine.push_back(r.spool);
    }

    String p = head("Product", "/products");
    p += "<div class='card'><div class='big'>" + swatch(q.rgba) + "#"
       + String((unsigned)id) + " " + esc(q.material[0] ? q.material : "Unknown")
       + "</div><p class='muted'>" + esc(q.vendor)
       + (q.abbr[0] ? " &middot; " + esc(q.abbr) : String()) + "</p>";
    if (q.provisional)
        p += "<p class='ob'>Provisional &mdash; this was read off a tag and nobody "
             "has confirmed it. Provisional products are never written back to "
             "tags. Saving this form confirms it.</p>";
    String ident;
    if (q.pkg_uuid[0])   ident += kv("package_uuid",  esc(q.pkg_uuid));
    if (q.mat_uuid[0])   ident += kv("material_uuid", esc(q.mat_uuid));
    if (q.brand_uuid[0]) ident += kv("brand_uuid",    esc(q.brand_uuid));
    if (q.gtin) { char g[24]; snprintf(g, sizeof(g), "%llu", (unsigned long long)q.gtin);
                  ident += kv("GTIN", String(g)); }
    if (q.has_lab) ident += kv("L*a*b*", String(q.lab[0], 2) + " / " + String(q.lab[1], 2)
                                       + " / " + String(q.lab[2], 2));
    if (ident.length()) p += "<div class='spec'>" + ident + "</div>";
    p += "</div>";

    char hex[8];
    snprintf(hex, sizeof(hex), "#%02x%02x%02x", q.rgba[0], q.rgba[1], q.rgba[2]);

    p += "<form method='POST' action='/api/product'>";
    p += "<input type='hidden' name='id' value='" + String((unsigned)id) + "'>";
    p += "<label>Vendor</label><input name='vendor' value='" + esc(q.vendor) + "'>";
    p += "<label>Filament (as shown on tags and in the app)</label>"
         "<input name='material' value='" + esc(q.material) + "'>";
    p += "<label>Type abbreviation &mdash; what usage totals group by</label>"
         "<input name='abbr' maxlength='7' value='" + esc(q.abbr) + "'>";
    p += "<label>Colour</label><input type='color' name='color' value='"
       + String(hex) + "'>";
    p += "<label><input type='checkbox' name='nocolor' style='width:auto' "
       + String(q.rgba[3] == 0 ? "checked" : "")
       + "> No colour assigned</label>";
    p += "<label>Diameter (mm)</label><input type='number' step='0.01' name='dia' value='"
       + String(q.dia, 2) + "'>";
    p += "<label>Empty spool tare (g)</label><input type='number' step='0.1' name='empty_g' value='"
       + String(q.empty_g, 1) + "'>";
    p += "<label>Nominal full weight (g)</label><input type='number' step='0.1' name='nom_g' value='"
       + String(q.nom_g, 1) + "'>";

    p += "<div class='card' style='margin-top:14px'>";
    if (mine.empty()) {
        p += "<p class='muted'>No spools reference this product yet, so saving "
             "changes nothing else.</p>";
    } else {
        p += "<p>Saving updates <b>" + String((unsigned)mine.size())
           + " spool(s)</b>: ";
        for (size_t i = 0; i < mine.size(); i++)
            p += (i ? ", " : "") + String("<a href='/spool?id=")
               + String((unsigned)mine[i]) + "' style='color:#8f8'>#"
               + String((unsigned)mine[i]) + "</a>";
        p += ".</p><p class='muted'>Their tags are rewritten the next time each "
             "spool is placed on the scale. A tag marked write-protected by its "
             "vendor is skipped &mdash; Main is not ours to overwrite.</p>";
    }
    p += "</div>";
    p += "<div><button type='submit'>Save &amp; update spools</button></div>";
    p += "</form>";
    p += "<p class='muted'><a href='/products' style='color:#8f8'>&larr; all products</a></p>";
    p += FOOT;
    req->send(200, "text/html", p);
}

static void handleApiProduct(AsyncWebServerRequest* req) {
    if (!authOk(req)) return;
    auto arg = [&](const char* k) -> String {
        const AsyncWebParameter* pp = req->getParam(k, true);
        return pp ? pp->value() : String();
    };
    uint32_t id = (uint32_t)arg("id").toInt();
    ProductRecord q;
    if (!id || !storeGetProduct(id, q)) { req->send(404, "text/plain", "unknown product"); return; }

    strlcpy(q.vendor,   arg("vendor").c_str(),   sizeof(q.vendor));
    strlcpy(q.material, arg("material").c_str(), sizeof(q.material));
    strlcpy(q.abbr,     arg("abbr").c_str(),     sizeof(q.abbr));
    // An unchecked checkbox is simply absent from the POST, which is how
    // "no colour" is distinguished from a colour that happens to be black.
    if (arg("nocolor").length()) {
        memset(q.rgba, 0, 4);            // alpha 0 = unassigned
    } else {
        const String c = arg("color");   // "#rrggbb" from <input type=color>
        long v = strtol(c.c_str() + (c.startsWith("#") ? 1 : 0), nullptr, 16);
        q.rgba[0] = (uint8_t)(v >> 16); q.rgba[1] = (uint8_t)(v >> 8);
        q.rgba[2] = (uint8_t)v;          q.rgba[3] = 255;
    }
    q.dia     = arg("dia").toFloat();
    q.empty_g = arg("empty_g").toFloat();
    q.nom_g   = arg("nom_g").toFloat();
    // Tare is never unknown. Checked before anything is written, like every
    // other 4xx here. It is the product's DEFAULT: saving it does not change
    // any spool's own tare (storePropagateProduct() keeps those), except a
    // spool that had none, which takes this one.
    if (q.empty_g <= 0.0f) {
        req->send(400, "text/plain", "a product needs a default spool tare (empty spool weight)");
        return;
    }
    // A human just reviewed and saved these values, which is exactly what
    // "provisional" was waiting for. Confirming it is what re-admits the
    // product to tag write-back.
    q.provisional = false;

    if (!storeUpsertProduct(q)) { req->send(500, "text/plain", "write failed"); return; }
    // Separate call, deliberately: without it every spool of this product keeps
    // a stale cached copy and a stale tag, and the edit would be invisible
    // everywhere except this page.
    storePropagateProduct(id);

    req->redirect("/product?id=" + String((unsigned)id));
}

static void handleApiProducts(AsyncWebServerRequest* req) {
    String j = "[";
    size_t n = storeProductCount();
    ProductRecord q;
    for (size_t i = 0; i < n; i++) {
        if (!storeProductAt(i, q)) continue;
        if (j.length() > 1) j += ",";
        j += "{\"id\":" + String((unsigned)q.id)
           + ",\"vendor\":\"" + esc(q.vendor) + "\""
           + ",\"material\":\"" + esc(q.material) + "\""
           + ",\"abbr\":\"" + esc(q.abbr) + "\""
           + ",\"color\":" + colorJson(q.rgba)
           + ",\"diameter_mm\":" + String(q.dia, 2)
           + ",\"empty_g\":" + String(q.empty_g, 1)
           + ",\"nominal_g\":" + String(q.nom_g, 1)
           + ",\"provisional\":" + (q.provisional ? "true" : "false");
        // Identity keys are emitted only when the tag actually carried them —
        // "" would read as "we know it is empty" rather than "absent".
        if (q.pkg_uuid[0])   j += ",\"package_uuid\":\""  + String(q.pkg_uuid)   + "\"";
        if (q.mat_uuid[0])   j += ",\"material_uuid\":\"" + String(q.mat_uuid)   + "\"";
        if (q.brand_uuid[0]) j += ",\"brand_uuid\":\""    + String(q.brand_uuid) + "\"";
        // A string, not a number: a GTIN is an identifier, and JSON numbers go
        // through a double in most consumers. snprintf rather than String(),
        // whose unsigned-long-long overload is not on every core.
        if (q.gtin) {
            char g[24];
            snprintf(g, sizeof(g), "%llu", (unsigned long long)q.gtin);
            j += ",\"gtin\":\""; j += g; j += "\"";
        }
        if (q.has_lab)
            j += ",\"lab\":[" + String(q.lab[0], 2) + "," + String(q.lab[1], 2)
               + "," + String(q.lab[2], 2) + "]";
        j += "}";
    }
    j += "]";
    req->send(200, "application/json", j);
}

// ── Per-spool weigh history + sparkline ───────────────────────────────────────
struct WeighSeries {
    std::vector<float>  rem, used, gross;
    std::vector<String> ts;
    std::vector<bool>   retired;   // this row is the spool's closing entry
};
static void collectWeigh(const StoreEvent& e, void* ctx) {
    WeighSeries* s = (WeighSeries*)ctx;
    s->rem.push_back(e.remaining_g);
    s->used.push_back(e.used_g);
    s->gross.push_back(e.gross_g);
    // Localized here, once, so both the HTML table and the CSV export below
    // get the same human-readable local time -- the log's own e.ts stays UTC
    // and untouched; this is a display-time conversion only.
    char local[32];
    storeLocalizeIso(e.ts, local, sizeof(local));
    s->ts.push_back(local[0] ? String(local) : String(e.ts));
    s->retired.push_back(e.ev == StoreEv::Retire);
}

// Remaining-weight-over-sessions sparkline: one series, so no legend — the title
// names it and the table below carries exact values. Thin 2px line, recessive
// baseline, endpoint dot; colour on the mark only, text stays in ink tokens.
static String sparkline(const std::vector<float>& v) {
    if (v.size() < 2)
        return "<p class='muted'>Not enough weigh sessions yet for a trend.</p>";
    const float W = 320, H = 64, PAD = 6;
    float lo = v[0], hi = v[0];
    for (float x : v) { if (x < lo) lo = x; if (x > hi) hi = x; }
    float span = (hi - lo) > 0.001f ? (hi - lo) : 1.0f;
    auto X = [&](size_t i){ return PAD + (W - 2*PAD) * (float)i / (v.size() - 1); };
    auto Y = [&](float val){ return PAD + (H - 2*PAD) * (1.0f - (val - lo) / span); };
    String pts;
    for (size_t i = 0; i < v.size(); i++) {
        if (i) pts += " ";
        pts += String(X(i), 1) + "," + String(Y(v[i]), 1);
    }
    char aria[96];
    snprintf(aria, sizeof(aria),
             "Remaining weight over %u weigh sessions, latest %.0f g",
             (unsigned)v.size(), v.back());
    String s = "<svg viewBox='0 0 320 64' width='320' style='max-width:100%;height:auto' "
               "role='img' aria-label='"; s += aria; s += "'>";
    s += "<line x1='6' y1='58' x2='314' y2='58' stroke='#333' stroke-width='1'/>";
    s += "<polyline fill='none' stroke='#8f8' stroke-width='2' "
         "stroke-linejoin='round' stroke-linecap='round' points='" + pts + "'/>";
    s += "<circle cx='" + String(X(v.size()-1), 1) + "' cy='" + String(Y(v.back()), 1)
       + "' r='3' fill='#cffccf'/>";
    s += "</svg>";
    return s;
}

static void handleSpoolDetail(AsyncWebServerRequest* req) {
    if (!req->hasParam("id")) { req->send(400, "text/plain", "missing id"); return; }
    uint32_t id = (uint32_t)req->getParam("id")->value().toInt();
    SpoolRecord r;
    if (!storeGetSpool(id, r)) { req->send(404, "text/plain", "unknown spool"); return; }

    WeighSeries s;
    storeForEachWeigh(id, collectWeigh, &s);

    if (req->hasParam("format") && req->getParam("format")->value() == "csv") {
        // "when_local" (not "ts"): the value is already converted to the
        // configured display timezone (Settings page), unlike every other
        // timestamp this station exposes (/export, /api/*), which stay UTC
        // on purpose -- this is the one download meant for a human to open
        // directly, not a machine to parse.
        String out = "when_local,gross_g,remaining_g,used_g,event\n";
        for (size_t i = 0; i < s.rem.size(); i++)
            out += s.ts[i] + "," + String(s.gross[i], 1) + ","
                 + String(s.rem[i], 1) + "," + String(s.used[i], 1) + ","
                 + (s.retired[i] ? "retired" : "weigh") + "\n";
        AsyncWebServerResponse* resp = req->beginResponse(200, "text/csv", out);
        resp->addHeader("Content-Disposition",
                        "attachment; filename=spool-" + String(id) + ".csv");
        req->send(resp);
        return;
    }

    String p = head("Spool", "/");
    p += "<div class='card'>";
    p += "<div class='big'>" + swatch(r.rgba)
       + "#" + String((unsigned)r.spool) + " "
       + esc(r.material[0] ? r.material : "Unknown") + "</div>";
    p += "<p class='muted'>" + esc(r.vendor) + (r.abbr[0] ? " &middot; " + esc(r.abbr) : String())
       + " &middot; " + String((unsigned)s.rem.size()) + " weigh session(s)</p>";
    p += "<p class='big'>" + String(r.remaining_g, 0) + " grams <span class='muted' "
         "style='font-size:15px'>remaining &middot; " + String(r.used_g, 0)
       + " grams used</span></p>";
    // This is where onboarding now lands, so it has to show what was entered —
    // otherwise submitting the form gives no confirmation that the tare and
    // nominal weight (the values every later reading depends on) took.
    String spec = specStrip(r);
    if (r.last_ts[0]) {
        char local[32];
        storeLocalizeIso(r.last_ts, local, sizeof(local));
        spec += kv("Last weighed", esc(local[0] ? local : r.last_ts));
    }
    // Which product this spool is an instance of. Worth showing even though the
    // fields above are its resolved values: if two spools of the same filament
    // report different products, the matching ladder missed, and this line is
    // the only place that is visible.
    ProductRecord q;
    if (r.product && storeGetProduct(r.product, q))
        spec += kv("Product", "<a href='/products' style='color:#8f8'>#"
                              + String((unsigned)q.id) + "</a>"
                              + (q.provisional ? " <span class='ob'>provisional</span>"
                                               : String()));
    // What this spool cost. This page is the ONLY place it is visible: the
    // Onboard form's field is deliberately blank every time (so a re-submit
    // can't silently wipe a recorded price), which also means the form can
    // never show you what is already on record. Without this, a price could
    // be entered and then never verified again.
    //
    // Shown even when it is 0/unset, rather than omitted like the fields
    // above: "which spools still need a price?" is exactly the question this
    // answers, and a silently absent row cannot answer it.
    spec += kv("Cost", r.cost > 0.0f
                          ? ("$" + String(r.cost, 2))
                          : String("<span class='muted'>not recorded</span>"));
    if (spec.length()) p += "<div class='spec'>" + spec + "</div>";
    p += "</div>";

    p += "<div class='card'><label style='margin-top:0'>Remaining over time</label>";
    p += sparkline(s.rem);
    p += "</div>";

    p += "<h3>Weigh history <a href='/spool?id=" + String(id)
       + "&format=csv' style='font-size:14px;color:#8f8'>(CSV)</a></h3>";
    p += "<table><tr><th>When</th><th>Gross</th><th>Remaining</th><th>Used</th><th></th></tr>";
    if (s.rem.empty())
        p += "<tr><td colspan='5' class='muted'>No weigh sessions yet</td></tr>";
    for (size_t k = s.rem.size(); k-- > 0; )   // newest first
        p += "<tr><td>" + s.ts[k] + "</td><td>" + String(s.gross[k], 0)
           + " g</td><td>" + String(s.rem[k], 0) + " g</td><td>"
           + String(s.used[k], 0) + " g</td><td>"
           + (s.retired[k] ? "<span class='ob'>closed &mdash; audit</span>" : "") + "</td></tr>";
    p += "</table>";
    p += "<p class='muted'><a href='/' style='color:#8f8'>&larr; back</a></p>";
    // Onboarding a stack of new spools lands here after each Save & write
    // tag (see the comment on the h3 above) -- staff working through the
    // stack place the next spool right from this page, and shouldn't have to
    // find the Onboard nav link again for every single one. Listen for the
    // same /events push the Onboard page does and jump there the instant a
    // spool needing onboarding shows up, whatever spool this page happens to
    // be showing.
    p += "<script>new EventSource('/events').addEventListener('state',function(e){"
         "if(e.data.split(',')[1]==='1')location.href='/onboard';"
         "});</script>";
    p += FOOT;
    req->send(200, "text/html", p);
}

// ── Onboarding form ───────────────────────────────────────────────────────────
// The page below is a one-shot server render keyed on whatever's on the
// scale AT REQUEST TIME (`cur`). Someone can leave the tab open, walk back
// to the station, place a spool, and watch the device register it and point
// back at this very page -- but the open tab has no way to know that
// happened until told. Listen on the /events SSE channel: every message
// (broadcast on a device-state change, or sent straight to a client the
// instant it connects/reconnects -- see webAppNotifyStateChanged() and
// sEvents.onConnect() in webAppBegin()) carries "<id>,<needs_onboarding>" as
// its body, so the page can decide to reload from the message alone (this
// page only cares about id; needs_onboarding is for the spool detail page's
// watcher below). An earlier
// version sent a bare ping and reacted by fetching /api/status to find out
// what changed -- found on hardware to sometimes silently stall, because
// this server holds very few concurrent connections and that fetch was
// racing the already-open SSE stream for one. Carrying the value directly
// needs no second connection at all. Reload the instant that id differs from
// the id this page was rendered for, whichever direction (none -> a spool,
// or spool A -> spool B); deliberately keyed on id change alone so mid-edit
// typing on the CURRENT spool's form is never interrupted by an unrelated
// status change (e.g. a Main-section reconcile write-back).
static String onboardWatchScript(int baselineId) {
    String s = "<script>(function(){"
               "var baseline=";
    s += String(baselineId);
    s += ";"
         "new EventSource('/events').addEventListener('state',function(e){"
           "var id=parseInt(e.data.split(',')[0],10);"
           "if(id!==baseline)location.reload();"
         "});"
         "})();</script>";
    return s;
}

// A static copy of OpenPrintTag/openprinttag-specification's
// material_type_enum.yaml — the same source CATALOG_SCRIPT's type-token
// matching already uses — kept local so the manual-entry "+ Add new
// material" panel below works with no network. Shared by Onboard and Stock
// List (see materialPickerField()), so it exists in exactly one place.
static const struct { int8_t key; const char* abbr; } kMatTypes[] = {
    {0,"PLA"},{1,"PETG"},{2,"TPU"},{3,"ABS"},{4,"ASA"},{5,"PC"},{6,"PCTG"},{7,"PP"},
    {8,"PA6"},{9,"PA11"},{10,"PA12"},{42,"PA612"},{11,"PA66"},{12,"CPE"},{13,"TPE"},
    {14,"HIPS"},{15,"PHA"},{16,"PET"},{17,"PEI"},{18,"PBT"},{19,"PVB"},{20,"PVA"},
    {21,"PEKK"},{22,"PEEK"},{23,"BVOH"},{24,"TPC"},{25,"PPS"},{26,"PPSU"},{27,"PVC"},
    {28,"PEBA"},{29,"PVDF"},{30,"PPA"},{31,"PCL"},{32,"PES"},{33,"PMMA"},{34,"POM"},
    {35,"PPE"},{36,"PS"},{37,"PSU"},{38,"TPI"},{39,"SBS"},{40,"OBC"},{41,"EVA"},
};

// Vendor/Material/Color manual-entry picklists — shared by Onboard's manual
// path and Stock List's manual fallback, so "+ Add new material" (which
// needs the full CfgMaterial shape: class/type enums, print/bed temps, not
// just a name) is defined in exactly one place. Skipping those fields
// silently writes 0 C onto a tag later at Onboard time, so it matters that
// both pages capture them the same way. Each `def*` is whatever should be
// pre-selected: Onboard passes its own remembered last pick; Stock List
// passes the row's current value when editing one, or ITS remembered last
// pick otherwise (see stockFormFields()) -- two separate memories (see
// last_stock.h), since the two pages are not necessarily the same session.
// The onchange handler resets #cat-source to 'manual', same as the OpenPrintTag
// catalog search's own picks do the opposite (CATALOG_SCRIPT's applyPick()),
// so a catalog pick followed by a change of mind here doesn't silently
// resubmit stale cat_* fields alongside freshly-typed ones.
static void vendorPickerField(String& p, const char* defVendor) {
    p += "<label>Vendor</label><select name='vendor' onchange=\""
         "document.getElementById('cat-source').value='manual';"
         "document.getElementById('vendor-new-wrap').style.display="
         "this.value=='__new__'?'block':'none'\">";
    char vbuf[64];
    for (size_t i = 0; i < cfgVendorCount(); i++)
        if (cfgVendorAt(i, vbuf, sizeof(vbuf)))
            p += String("<option") + (strcmp(vbuf, defVendor) == 0 ? " selected" : "")
               + ">" + esc(vbuf) + "</option>";
    p += "<option value='__new__'>&plus; Add new vendor&hellip;</option>";
    p += "</select>";
    p += "<div id='vendor-new-wrap' style='display:none;margin-top:8px'>"
         "<label>New vendor name</label>"
         "<input type='text' name='vendor_new' placeholder='e.g. Filamentive'>"
         "</div>";
}

static void materialPickerField(String& p, const char* defMaterial) {
    p += "<label>Material</label><select name='material' onchange=\""
         "document.getElementById('cat-source').value='manual';"
         "document.getElementById('material-new-wrap').style.display="
         "this.value=='__new__'?'block':'none'\">";
    CfgMaterial m;
    for (size_t i = 0; i < cfgMaterialCount(); i++)
        if (cfgMaterialAt(i, m))
            p += String("<option") + (strcmp(m.name, defMaterial) == 0 ? " selected" : "")
               + ">" + esc(m.name) + "</option>";
    p += "<option value='__new__'>&plus; Add new material&hellip;</option>";
    p += "</select>";
    p += "<div id='material-new-wrap' style='display:none;margin-top:8px'>"
         "<label>New material name</label>"
         "<input type='text' name='material_new_name' placeholder='e.g. PETG Carbon Fiber'>"
         "<label>Abbreviation (max 7 chars)</label>"
         "<input type='text' name='material_new_abbr' maxlength='7' placeholder='e.g. PETGCF'>"
         "<label>Class</label><select name='material_new_class'>"
         "<option value='0'>FFF (filament)</option><option value='1'>SLA (resin)</option></select>"
         "<label>Type</label><select name='material_new_type'>";
    for (const auto& t : kMatTypes)
        p += "<option value='" + String((int)t.key) + "'>" + t.abbr + "</option>";
    p += "</select>"
         "<label>Diameter (mm)</label><input type='number' step='0.01' name='material_new_dia' value='1.75'>"
         "<label>Print temp min/max (&deg;C)</label>"
         "<input type='number' name='material_new_print_min' placeholder='min' style='width:48%;display:inline-block'>"
         " <input type='number' name='material_new_print_max' placeholder='max' style='width:48%;display:inline-block'>"
         "<label>Bed temp min/max (&deg;C)</label>"
         "<input type='number' name='material_new_bed_min' placeholder='min' style='width:48%;display:inline-block'>"
         " <input type='number' name='material_new_bed_max' placeholder='max' style='width:48%;display:inline-block'>"
         "</div>";
}

static void colorPickerField(String& p, const char* defColor) {
    p += "<label>Color</label><select name='color' onchange=\""
         "document.getElementById('cat-source').value='manual';"
         "document.getElementById('color-new-wrap').style.display="
         "this.value=='__new__'?'block':'none'\">";
    CfgColor c;
    for (size_t i = 0; i < cfgColorCount(); i++)
        if (cfgColorAt(i, c))
            p += String("<option") + (strcmp(c.name, defColor) == 0 ? " selected" : "")
               + ">" + esc(c.name) + "</option>";
    p += "<option value='__new__'>&plus; Add new colour&hellip;</option>";
    p += "</select>";
    p += "<div id='color-new-wrap' style='display:none;margin-top:8px'>"
         "<label>New colour name</label>"
         "<input type='text' name='color_new_name' placeholder='e.g. Summer Grass'>"
         "<label>Swatch</label><input type='color' name='color_new' value='#808080'>"
         "</div>";
}

static void handleOnboardForm(AsyncWebServerRequest* req) {
    String p = head("Onboard", "/onboard");
    int cur = currentSpool();

    if (cur < 0) {
        p += "<div class='card'><p>No spool is on the scale.</p>"
             "<p class='muted'>Place a spool and this page will update on its "
             "own once it's registered.</p></div>";
        p += onboardWatchScript(-1);
        p += FOOT;
        req->send(200, "text/html", p);
        return;
    }

    SpoolRecord r;
    storeGetSpool((uint32_t)cur, r);

    // ── A spool that is ALREADY onboarded ─────────────────────────────────────
    // This page acts on whatever is on the scale, and it is also the only
    // place to add a price later, fix a spool attached to the wrong product,
    // or give a pre-product spool one -- so it can't simply refuse. But the
    // form used to open on "a new product" with blank fields, so a re-save
    // silently replaced a finished spool's identity, product, tare and
    // nominal weight and rewrote its tag. Found live: someone placing a known
    // spool, opening this tab, and reading the blank form as "not filled in".
    //
    // So: a notice first and the form behind a deliberate click; the form
    // opens on "another spool of <its current product>", so re-saving it
    // unchanged (e.g. only to add a price) keeps the identity as it was; and
    // choosing a different identity asks before submitting.
    const bool already = !r.needs_ob;
    ProductRecord curProd;
    const bool haveCur = already && r.product && storeGetProduct(r.product, curProd);

    if (already) {
        p += "<div class='card'><h3>Spool #" + String((unsigned)cur)
           + " is already onboarded</h3>"
             "<p><a href='/spool?id=" + String((unsigned)cur) + "'>"
           + swatch(r.rgba) + esc(r.vendor) + " "
           + esc(r.material[0] ? r.material : "Unknown") + "</a></p>"
             "<p class='muted'>Nothing needs entering. Only change its details to "
             "add a price, or if it was attached to the wrong product &mdash; "
             "saving rewrites its tag.</p>"
             "<button type='button' class='sec' onclick=\""
               "document.getElementById('obwrap').style.display='block';"
               "this.style.display='none'\">Change this spool's details</button>"
             "</div>";
        p += "<div id='obwrap' style='display:none'>";
    }

    p += "<h3>" + String(already ? "Change" : "Onboard") + " spool #"
       + String((unsigned)cur) + "</h3>";
    // The submit check mirrors handleApiOnboard's: a manual-entry onboard (not
    // "another spool of X", not a catalog pick) takes its nominal weight and
    // tare from the spool profile alone, so it needs one. The server enforces
    // it too; this just says so before the page is replaced by a bare 400.
    //
    // It also checks the tare the same way the server does (tare is never
    // unknown): the typed value, else what the chosen path supplies — the
    // product's (data-tare on its option), the catalog's, or the profile's.
    //
    // For an already-onboarded spool, anything other than "another spool of
    // X" (a new product, typed or from the catalog) replaces its identity, so
    // that asks first. Picking a different existing product doesn't ask: it
    // is an explicit choice from a list, not a form left on its default. The
    // question comes last, after the checks, so nobody confirms a replacement
    // only to be told a field is missing.
    p += "<form method='POST' action='/api/onboard' onsubmit=\""
           "var d=document.getElementById('prod'),"
               "s=document.getElementById('cat-source'),"
               "f=document.getElementById('profile');"
           "if((!d||d.value=='0')&&s&&s.value=='manual'&&f&&f.value==''){"
             "alert('Pick a spool profile (next to the tare box) \\u2014 it sets "
             "this spool\\'s full and empty weights.');f.focus();return false;}"
           "var t=parseFloat(document.getElementById('tare').value)||0;"
           "if(t<=0){"
             "if(d&&d.value!='0'){t=parseFloat(d.selectedOptions[0].dataset.tare)||0;}"
             "else if(s&&s.value=='catalog'){var c=document.getElementById('cat-f-cat_empty_g');"
               "t=parseFloat(c&&c.value)||0;}"
             "else if(f&&f.value=='__new__'){t=parseFloat(document.getElementById('profile-new-empty').value)||0;}"
             "else if(f&&f.selectedOptions[0]){t=parseFloat(f.selectedOptions[0].dataset.tare)||0;}"
           "}"
           "if(t<=0){alert('This spool needs a tare (empty spool weight). Pick a spool "
             "profile, type it, or use Capture tare.');document.getElementById('tare').focus();"
             "return false;}";
    if (already)
        p += String("if((!d||d.value=='0')&&!confirm('This replaces spool #")
           + String((unsigned)cur) + "\\'s identity and rewrites its tag. Continue?'))"
             "return false;";
    p +=   "return true;\">";
    p += "<input type='hidden' name='id' value='" + String((unsigned)cur) + "'>";

    // Applies regardless of which of the three paths below resolves the rest
    // of the identity -- what THIS spool cost is a fact about the purchase,
    // not about the product, so it belongs outside #newprod (which hides for
    // "another spool of X"). Deliberately no last-used default the way
    // vendor/material/colour get one: a stale price silently kept is
    // exactly the failure worth avoiding here, so it starts blank every time.
    //
    // What IS on record is shown beside the field as text, never as the
    // input's value: pre-filling it would put a price back in the POST that
    // nobody re-typed, which is the whole thing the blank field prevents.
    // But leaving it invisible meant a price could be entered and never
    // verified again, since no other page showed it either.
    p += "<label>Cost for this spool ($) &mdash; leave blank if unknown</label>"
         "<input type='number' step='0.01' min='0' name='cost'>";
    p += "<p class='muted' style='margin-top:4px'>";
    if (r.cost > 0.0f)
        p += "Currently recorded: <b>$" + String(r.cost, 2) + "</b>. "
             "Leaving this blank keeps it; enter 0 to clear it.";
    else
        p += "No cost recorded for this spool yet.";
    p += "</p>";

    // ── "Another spool of X" ──────────────────────────────────────────────────
    // The path that makes this worth building. Nine onboardings out of ten are
    // a repeat of one already done, and every retype is a fresh chance to pick
    // the wrong spool profile — which silently biases every later remaining
    // weight, because remaining is gross minus tare.
    const size_t np = storeProductCount();
    if (np) {
        p += "<label>This spool is&hellip;</label><select name='product' id='prod' "
             "onchange=\"document.getElementById('newprod').style.display="
             "this.value=='0'?'block':'none'\">";
        // "A new product" listed FIRST and left as the browser's default
        // selection, not appended after the MRU list -- on direct user
        // correction. With it at the bottom, the unlabeled default was
        // whichever product happened to sort first in the store (an
        // unrelated leftover from an earlier onboarding), so onboarding a
        // genuinely new reel without deliberately reselecting "a new
        // product" first would silently attribute it to that stale product
        // instead.
        p += "<option value='0'>&mdash; A new product &mdash;</option>";
        ProductRecord q;
        for (size_t i = 0; i < np; i++) {
            if (!storeProductAt(i, q)) continue;
            const bool isCur = haveCur && q.id == curProd.id;
            p += "<option value='" + String((unsigned)q.id) + "' data-tare='"
               + String(q.empty_g, 1) + "'"
               + (isCur ? " selected" : "") + ">"
               + esc(q.vendor) + " " + esc(q.material[0] ? q.material : "Unknown")
               + (q.nom_g > 0 ? " &mdash; " + String(q.nom_g, 0) + " g" : String())
               + (q.provisional ? " (provisional)" : "")
               + (isCur ? " (current)" : "")
               + "</option>";
        }
        p += "</select>";
        // The default selection is "a new product" for a spool that needs
        // onboarding, so the detail fields start visible to match -- they
        // hide once an existing product is actually picked (the onchange
        // handler above). An already-onboarded spool opens on its current
        // product instead (see `already` above), so they start hidden.
        p += haveCur ? "<div id='newprod' style='display:none'>" : "<div id='newprod'>";
    } else {
        // Nothing stocked yet, so there is no "another spool of X" to offer.
        p += "<input type='hidden' name='product' value='0'>";
        p += "<div id='newprod'>";
    }

    // ── OpenPrintTag catalog search ───────────────────────────────────────────
    // Live search of the OPT database (github.com/OpenPrintTag/openprinttag-
    // database) straight from the browser — the device is never in the loop,
    // so this costs the firmware nothing. A pick fills the hidden cat_* fields
    // below with authoritative vendor data (GTIN, the three OPT UUIDs, real
    // print/bed temps when the material file has them) instead of whatever a
    // person free-types. See tools/opt-catalog/prototype.html for how this was
    // validated against the live DB before landing here.
    p += "<div class='card'>"
         "<label>Search filament catalog</label>"
         "<div class='cat-status' id='cat-status'>Loading catalog&hellip;</div>"
         "<div class='cat-field' id='cat-field-vendor'>"
           "<label>Vendor</label>"
           "<input class='cat-input' id='cat-in-vendor' placeholder='Loading&hellip;' disabled autocomplete='off'>"
           "<div class='cat-panel' id='cat-panel-vendor'></div>"
         "</div>"
         "<div class='cat-field disabled' id='cat-field-type'>"
           "<label>Material type</label>"
           "<input class='cat-input' id='cat-in-type' placeholder='Pick a vendor first' disabled autocomplete='off'>"
           "<div class='cat-panel' id='cat-panel-type'></div>"
         "</div>"
         "<div class='cat-field disabled' id='cat-field-material'>"
           "<label>Material</label>"
           "<input class='cat-input' id='cat-in-material' placeholder='Pick a vendor first' disabled autocomplete='off'>"
           "<div class='cat-panel' id='cat-panel-material'></div>"
         "</div>"
         "<div id='cat-resolved'></div>"
         "</div>";
    p += "<input type='hidden' name='source' id='cat-source' value='manual'>"
         "<input type='hidden' name='cat_vendor'      id='cat-f-cat_vendor'>"
         "<input type='hidden' name='cat_material'    id='cat-f-cat_material'>"
         "<input type='hidden' name='cat_abbr'        id='cat-f-cat_abbr'>"
         "<input type='hidden' name='cat_rgba'        id='cat-f-cat_rgba'>"
         "<input type='hidden' name='cat_dia'         id='cat-f-cat_dia'>"
         "<input type='hidden' name='cat_nom_g'       id='cat-f-cat_nom_g'>"
         "<input type='hidden' name='cat_empty_g'     id='cat-f-cat_empty_g'>"
         "<input type='hidden' name='cat_gtin'        id='cat-f-cat_gtin'>"
         "<input type='hidden' name='cat_pkg_uuid'    id='cat-f-cat_pkg_uuid'>"
         "<input type='hidden' name='cat_mat_uuid'    id='cat-f-cat_mat_uuid'>"
         "<input type='hidden' name='cat_brand_uuid'  id='cat-f-cat_brand_uuid'>"
         "<input type='hidden' name='cat_print_min'   id='cat-f-cat_print_min'>"
         "<input type='hidden' name='cat_print_max'   id='cat-f-cat_print_max'>"
         "<input type='hidden' name='cat_bed_min'     id='cat-f-cat_bed_min'>"
         "<input type='hidden' name='cat_bed_max'     id='cat-f-cat_bed_max'>";

    p += "<details id='cat-manual-details'><summary style='color:#9c9;cursor:pointer;margin:10px 0'>"
         "Or enter manually</summary>";

    // Every manual select ends with a "+ Add new ..." option that reveals a
    // hidden panel of plain inputs, submitted alongside it; handleApiOnboard
    // recognises the '__new__' sentinel, builds the Cfg* row from those
    // fields, and appends it to the local catalog table (cfgVendorAdd() and
    // friends) so it is there for next time — same mechanism the catalog
    // search already uses for Vendor, extended to the fields it doesn't
    // reach (Material, Color, Spool profile).

    // Vendor/Material/Color — see vendorPickerField()/materialPickerField()/
    // colorPickerField() above (shared with Stock List's manual fallback).
    // Each defaults to whatever was picked last time (last_onboard.h): a
    // batch of new stock from one supplier is usually many spools in a row
    // of the same vendor, so retyping/reselecting it every time is pure
    // friction. Falls back to the browser's own default (first option) when
    // nothing's been remembered yet, or the remembered name no longer exists.
    vendorPickerField(p, lastOnboardVendor());
    materialPickerField(p, lastOnboardMaterial());
    colorPickerField(p, lastOnboardColor());

    p += "</details>";
    p += "</div>";   // #newprod — everything below applies to every path

    // ── Spool profile: the tare preset, OUTSIDE the manual-entry details ─────
    // A spool profile is a weight fact (tare + nominal full), not an identity
    // one, so it applies no matter how the identity was resolved. It used to
    // live inside the collapsed "Or enter manually" block, which made it
    // invisible to anyone using the catalog search — while the tare field
    // below, which IS visible, said "blank to use profile" and pointed at a
    // picker they could not see. A lab that uses three spool types wants
    // those three one click away on every path, which is the whole point of
    // having presets at all.
    //
    // Picking one fills the tare box client-side. That is what makes it work
    // on every path: a typed tare beats the catalog's own value, the
    // profile's, and — on "another spool of X" — the product's, on every
    // branch that reads it. Tare belongs to the spool, not the product
    // (docs/design/onboarding-vocabulary.md): the same filament sometimes
    // arrives on a different spool body, so this block sits outside #newprod
    // and stays visible when an existing product is picked.
    //
    // Deliberately does NOT fill on page load, only on an actual pick: blank
    // has to keep meaning "use whatever this path already knows", or every
    // catalog pick would silently have its real container tare overwritten by
    // a local guess.
    //
    // And deliberately does NOT set cat-source='manual' the way the identity
    // picklists do. It used to, via the shared revealOnchange() helper, which
    // meant picking a catalog product and then adjusting the spool profile
    // silently threw the catalog identity away -- UUIDs, GTIN and print temps
    // all reverting to whatever the manual picklists happened to hold.
    // Choosing a tare preset is not a statement that you are typing the
    // identity by hand.
    //
    // Starts on a neutral "choose" option rather than the last-used profile.
    // A preselected profile that has NOT filled the tare box (see above) read
    // as though it had been applied, when on the catalog path it had not.
    // The cost of a neutral default is that the manual path takes nominal
    // weight and tare from the profile alone, so handleApiOnboard refuses a
    // manual onboard with none picked, and the form checks the same thing on
    // submit, rather than silently writing 0 g / 0 g to the tag.
    p += "<label>Spool profile &mdash; sets the tare below</label>"
         "<select name='profile' id='profile' onchange=\""
           "document.getElementById('profile-new-wrap').style.display="
             "this.value=='__new__'?'block':'none';"
           "var o=this.selectedOptions[0];"
           "if(o&&o.dataset.tare)document.getElementById('tare').value=o.dataset.tare;"
         "\">";
    p += "<option value='' selected>&mdash; choose a spool profile &mdash;</option>";
    CfgProfile pr;
    for (size_t i = 0; i < cfgProfileCount(); i++)
        if (cfgProfileAt(i, pr))
            p += String("<option data-tare='") + String(pr.empty_g, 1) + "'>"
               + esc(pr.label) + "</option>";
    p += "<option value='__new__'>&plus; Add new spool profile&hellip;</option>";
    p += "</select>";
    p += "<div id='profile-new-wrap' style='display:none;margin-top:8px'>"
         "<label>New profile label</label>"
         "<input type='text' name='profile_new_label' placeholder='e.g. Filamentive 1kg PETG'>"
         "<label>Nominal full weight (g)</label><input type='number' step='0.1' name='profile_new_nom'>"
         "<label>Empty spool weight / tare (g)</label><input type='number' step='0.1' name='profile_new_empty' id='profile-new-empty'>"
         "</div>";

    // Tare override (optional). "Capture tare" reads the load cell once.
    p += "<label>Empty spool tare (g) &mdash; blank uses the product, catalog or profile value</label>"
         "<input type='number' step='0.1' name='empty_g' id='tare' placeholder='from product, profile or catalog'>";
    p += "<button type='button' class='sec' onclick=\"fetch('/api/tare',{method:'POST'})"
         ".then(r=>r.json()).then(d=>{document.getElementById('tare').value=d.weight.toFixed(1)})\">"
         "Capture tare from scale</button>";

    p += "<div><button type='submit'>Save &amp; write tag</button></div>";
    p += "</form>";
    if (already) p += "</div>";   // #obwrap
    p += CATALOG_STYLE;
    p += CATALOG_SCRIPT;
    p += onboardWatchScript(cur);
    p += FOOT;
    req->send(200, "text/html", p);
}

// ── POST /api/tare — one load-cell reading ────────────────────────────────────
static void handleApiTare(AsyncWebServerRequest* req) {
    if (!authOk(req)) return;
    xSemaphoreTake(gWeightMutex, portMAX_DELAY);
    float w = gWeightGrams;
    xSemaphoreGive(gWeightMutex);
    req->send(200, "application/json", "{\"weight\":" + String(w, 1) + "}");
}

// Resolve `probe` to an existing product, or create one if nothing matches.
// Shared by every place a form resolves a product from typed/picked fields
// (Onboard's catalog and manual paths, the Stock List's catalog path below)
// so the same real filament converges on the same product id regardless of
// which page or path it was entered through.
static uint32_t findOrCreateProduct(ProductRecord& probe) {
    ProductRecord found;
    if (storeFindProduct(probe, found)) return found.id;
    if (storeUpsertProduct(probe))      return probe.id;
    return 0;
}

// ── POST /api/onboard — apply the form, write the tag, log a reconcile ────────
static void handleApiOnboard(AsyncWebServerRequest* req) {
    if (!authOk(req)) return;
    auto arg = [&](const char* k) -> String {
        const AsyncWebParameter* pp = req->getParam(k, true);
        return pp ? pp->value() : String();
    };

    uint32_t id = (uint32_t)arg("id").toInt();
    if (id == 0) { req->send(400, "text/plain", "missing id"); return; }

    SpoolRecord rec;
    if (!storeGetSpool(id, rec)) { req->send(404, "text/plain", "unknown spool"); return; }

    // Two paths. "Another spool of X" inherits everything from an existing
    // product and ignores the detail fields entirely — that is the whole point
    // of it, and it is also what removes the chance to pick the wrong spool
    // profile on a repeat onboarding.
    const uint32_t chosen = (uint32_t)arg("product").toInt();

    String  vendor, display, abbr;
    uint8_t rgba[4] = {};
    float   nominal = 0, empty = 0, dia = 1.75f;
    CfgMaterial m = {};
    bool    haveMat = false;
    uint32_t pid = 0;

    // OPT identity carried through regardless of path, so a catalog-sourced
    // pick's real GTIN/UUIDs (and, when the material file has them, real
    // print/bed temps) reach both the product record and the physical tag
    // instead of being dropped on the floor after resolving. Empty/zero here
    // just means "the source didn't have one" — the tag-write block below
    // already treats that as absent.
    String   pkgUuid, matUuid, brandUuid;
    uint64_t gtin = 0;
    bool     haveCatTemps = false;
    int16_t  catPrintMin = 0, catPrintMax = 0, catBedMin = 0, catBedMax = 0;

    ProductRecord q;
    const bool haveChosen = chosen && storeGetProduct(chosen, q);

    // The manual path takes nominal weight and tare from the spool profile
    // alone, and the picker now starts on a blank "choose" option, so a
    // manual onboard with no profile would write 0 g / 0 g to the tag.
    // Checked HERE, before the manual branch adds any "+ Add new ..." catalog
    // rows, creates a product, or rewrites the last-used memory: a request
    // that answers 4xx must not have changed anything.
    if (!haveChosen && arg("source") != "catalog") {
        const String prof = arg("profile");
        if (prof.length() == 0) {
            req->send(400, "text/plain",
                      "pick a spool profile: it sets this spool's full and empty weights");
            return;
        }
        if (prof == "__new__" && (arg("profile_new_label").length() == 0 ||
                                  arg("profile_new_nom").toFloat() <= 0.0f)) {
            req->send(400, "text/plain",
                      "a new spool profile needs a label and a nominal full weight");
            return;
        }
    }

    // Tare is never unknown (docs/design/onboarding-vocabulary.md): every
    // path must end with a real one, or remaining silently counts the spool
    // body as filament. Resolved here exactly as the branches below will
    // resolve it — a typed tare first, then whatever the path supplies — and
    // checked before any of them writes anything, for the same 4xx rule.
    {
        float tare = arg("empty_g").toFloat();
        const char* missing = nullptr;
        if (tare <= 0.0f) {
            if (haveChosen) {
                tare = q.empty_g;
                missing = "this product has no tare on record: enter this spool's "
                          "tare (or pick a spool profile), or fix the product's on its page";
            } else if (arg("source") == "catalog") {
                tare = arg("cat_empty_g").toFloat();
                missing = "the catalog has no empty weight for this package: enter "
                          "the spool's tare, pick a spool profile, or capture it from the scale";
            } else {
                const String prof = arg("profile");
                if (prof == "__new__") {
                    tare = arg("profile_new_empty").toFloat();
                } else {
                    CfgProfile pr;
                    for (size_t i = 0; i < cfgProfileCount(); i++)
                        if (cfgProfileAt(i, pr) && prof == pr.label) { tare = pr.empty_g; break; }
                }
                missing = "no tare: the spool profile has none, so enter the spool's "
                          "tare or capture it from the scale";
            }
        }
        if (tare <= 0.0f) {
            req->send(400, "text/plain", missing ? missing : "no tare");
            return;
        }
    }

    if (haveChosen) {
        pid     = q.id;
        vendor  = q.vendor;
        display = q.material;
        abbr    = q.abbr;
        memcpy(rgba, q.rgba, 4);
        // Everything is inherited from the product EXCEPT a typed tare: the
        // product's is only a default. Tare belongs to the spool, and the same
        // filament sometimes arrives on a different spool body. The product
        // itself is left alone — its default changes only on /product.
        const float tareOvr = arg("empty_g").toFloat();
        dia = q.dia; nominal = q.nom_g;
        empty = (tareOvr > 0.0f) ? tareOvr : q.empty_g;
        pkgUuid = q.pkg_uuid; matUuid = q.mat_uuid; brandUuid = q.brand_uuid; gtin = q.gtin;
        // The tag also wants print/bed temps and the material class/type, which
        // live on the config catalog rather than on the product. Look them up
        // by abbreviation — cfgMaterialByAbbr, not ByName, since a row can be
        // named "PLA Silk" but abbreviated "PLA". If there is no matching row
        // the tag simply keeps the temps it already had.
        haveMat = cfgMaterialByAbbr(abbr.c_str(), m);
    } else if (arg("source") == "catalog") {
        // Picked from the OpenPrintTag catalog search (see CATALOG_SCRIPT) —
        // the browser already resolved package -> material + container + brand
        // against the live DB, so these are the vendor's own published values,
        // not a local guess. No cfgMaterialByName/cfgColorByName lookup needed;
        // the catalog gave us the real numbers directly.
        float tareOvr = arg("empty_g").toFloat();   // 0 → use catalog's own tare

        vendor  = arg("cat_vendor");
        display = arg("cat_material");
        abbr    = arg("cat_abbr");
        String rgbaHex = arg("cat_rgba");
        if (rgbaHex.length() == 8)
            for (int i = 0; i < 4; i++)
                rgba[i] = (uint8_t)strtol(rgbaHex.substring(i * 2, i * 2 + 2).c_str(), nullptr, 16);

        dia     = arg("cat_dia").toFloat();
        if (dia <= 0.0f) dia = 1.75f;
        nominal = arg("cat_nom_g").toFloat();
        empty   = (tareOvr > 0.0f) ? tareOvr : arg("cat_empty_g").toFloat();

        pkgUuid   = arg("cat_pkg_uuid");
        matUuid   = arg("cat_mat_uuid");
        brandUuid = arg("cat_brand_uuid");
        gtin      = strtoull(arg("cat_gtin").c_str(), nullptr, 10);

        haveCatTemps = arg("cat_print_min").length() > 0;
        if (haveCatTemps) {
            catPrintMin = (int16_t)arg("cat_print_min").toInt();
            catPrintMax = (int16_t)arg("cat_print_max").toInt();
            catBedMin   = (int16_t)arg("cat_bed_min").toInt();
            catBedMax   = (int16_t)arg("cat_bed_max").toInt();
        }
        // Local material class/type enum still comes from the config catalog
        // (the OPT database's class/type strings aren't mapped to our enum) —
        // by abbreviation, which is all a catalog pick knows. The manual path
        // looks up by the material row's name instead, because it has one.
        haveMat = cfgMaterialByAbbr(abbr.c_str(), m);

        ProductRecord prod;
        strlcpy(prod.vendor,     vendor.c_str(),    sizeof(prod.vendor));
        strlcpy(prod.material,   display.c_str(),   sizeof(prod.material));
        strlcpy(prod.abbr,       abbr.c_str(),       sizeof(prod.abbr));
        strlcpy(prod.pkg_uuid,   pkgUuid.c_str(),    sizeof(prod.pkg_uuid));
        strlcpy(prod.mat_uuid,   matUuid.c_str(),    sizeof(prod.mat_uuid));
        strlcpy(prod.brand_uuid, brandUuid.c_str(),  sizeof(prod.brand_uuid));
        prod.gtin = gtin;
        memcpy(prod.rgba, rgba, 4);
        prod.dia = dia; prod.empty_g = empty; prod.nom_g = nominal;
        pid = findOrCreateProduct(prod);
    } else {
        String matName  = arg("material");
        String colName  = arg("color");
        String profName = arg("profile");
        float  tareOvr  = arg("empty_g").toFloat();   // 0 → use profile

        // "+ Add new ..." sentinel from the onboard form (see handleOnboardForm)
        // — build the Cfg* row from the revealed fields and append it to the
        // local catalog so it is there for next time, same as a typed vendor
        // already was via cfgVendorAdd() below.
        vendor = arg("vendor");
        if (vendor == "__new__") vendor = arg("vendor_new");

        if (matName == "__new__") {
            CfgMaterial nm = {};
            strlcpy(nm.name, arg("material_new_name").c_str(), sizeof(nm.name));
            strlcpy(nm.abbr, arg("material_new_abbr").c_str(), sizeof(nm.abbr));
            nm.cls       = (int8_t)arg("material_new_class").toInt();
            nm.type      = (int8_t)arg("material_new_type").toInt();
            nm.dia       = arg("material_new_dia").toFloat();
            if (nm.dia <= 0.0f) nm.dia = 1.75f;
            nm.print_min = (int16_t)arg("material_new_print_min").toInt();
            nm.print_max = (int16_t)arg("material_new_print_max").toInt();
            nm.bed_min   = (int16_t)arg("material_new_bed_min").toInt();
            nm.bed_max   = (int16_t)arg("material_new_bed_max").toInt();
            cfgMaterialAdd(nm);
            matName = nm.name;
            m = nm; haveMat = true;
        } else {
            haveMat = cfgMaterialByName(matName.c_str(), m);
        }

        CfgColor col = {};
        if (colName == "__new__") {
            CfgColor nc = {};
            strlcpy(nc.name, arg("color_new_name").c_str(), sizeof(nc.name));
            String hex = arg("color_new");   // "#rrggbb" from <input type='color'>
            if (hex.length() == 7 && hex[0] == '#') {
                nc.rgba[0] = (uint8_t)strtol(hex.substring(1, 3).c_str(), nullptr, 16);
                nc.rgba[1] = (uint8_t)strtol(hex.substring(3, 5).c_str(), nullptr, 16);
                nc.rgba[2] = (uint8_t)strtol(hex.substring(5, 7).c_str(), nullptr, 16);
                nc.rgba[3] = 255;
            }
            cfgColorAdd(nc);
            colName = nc.name;
            col = nc;
        } else {
            cfgColorByName(colName.c_str(), col);
        }
        memcpy(rgba, col.rgba, 4);

        CfgProfile pr = {};
        bool havePr = false;
        if (profName == "__new__") {
            CfgProfile np = {};
            strlcpy(np.label, arg("profile_new_label").c_str(), sizeof(np.label));
            np.nominal_full_g = arg("profile_new_nom").toFloat();
            np.empty_g        = arg("profile_new_empty").toFloat();
            cfgProfileAdd(np);
            profName = np.label;
            pr = np; havePr = true;
        } else {
            for (size_t i = 0; i < cfgProfileCount(); i++)
                if (cfgProfileAt(i, pr) && profName == pr.label) { havePr = true; break; }
        }

        // Remember these three for next time's dropdown defaults — see
        // last_onboard.h. vendor/matName/colName are all final resolved names
        // by this point, whether picked from the list or just created via
        // "+ Add new ...". Not the spool profile: that picker starts neutral.
        lastOnboardSet(vendor.c_str(), matName.c_str(), colName.c_str());

        nominal = havePr ? pr.nominal_full_g : 0.0f;
        empty   = (tareOvr > 0.0f) ? tareOvr : (havePr ? pr.empty_g : 0.0f);
        dia     = haveMat ? m.dia : 1.75f;
        abbr    = haveMat ? m.abbr : "";

        // OPT key 10 material_name is a DISPLAY string, not a type code. The
        // spec's own example is "PC Blend Carbon Fiber Black", and it says
        // brand_name and material_name should be shown together as "Prusament
        // PLA Galaxy Black"; the short code belongs in key 52
        // material_abbreviation (max 7 chars).
        //
        // So the colour name goes here. That is what makes "Summer Grass" a
        // first-class part of the record: it round-trips on the tag, it is what
        // every OPT-aware reader will display, and it needs no field the spec
        // does not already define.
        display = matName;
        if (colName.length()) display += " " + colName;

        // Resolve which product these values describe, creating one if this is
        // a filament we have never stocked. Not provisional: a person typed it.
        //
        // Deliberately does NOT update a product that already matches. An edit
        // to a product propagates to every spool of it, and this form is about
        // ONE spool — someone correcting a typo here would silently rewrite a
        // whole shelf's tags. That edit belongs on /product, which says how
        // many spools it will touch before you press save.
        ProductRecord prod;
        strlcpy(prod.vendor,   vendor.c_str(),  sizeof(prod.vendor));
        strlcpy(prod.material, display.c_str(), sizeof(prod.material));
        strlcpy(prod.abbr,     abbr.c_str(),    sizeof(prod.abbr));
        memcpy(prod.rgba, rgba, 4);
        prod.dia = dia; prod.empty_g = empty; prod.nom_g = nominal;
        pid = findOrCreateProduct(prod);
    }

    // 1) Append the identity to the log so indices + inventory reflect it.
    StoreEvent e; e.ev = StoreEv::Reconcile;
    strlcpy(e.uuid, rec.uuid, sizeof(e.uuid));
    e.spool = id;
    strlcpy(e.vendor,   vendor.c_str(),  sizeof(e.vendor));
    strlcpy(e.material, display.c_str(), sizeof(e.material));
    strlcpy(e.abbr,     abbr.c_str(), sizeof(e.abbr));
    memcpy(e.rgba, rgba, 4);
    e.dia = dia; e.empty_g = empty; e.nom_g = nominal;
    e.needs_ob = false;
    // Identity events replace the record's whole identity group, so this must
    // be set explicitly — leaving it at 0 would silently un-assign the product
    // every time someone edited a spool through this form.
    e.product = pid ? pid : rec.product;
    // Same trap, for cost: the field starts blank every time (deliberately,
    // see handleOnboardForm), so re-submitting this form later to fix a typo
    // elsewhere — without retyping the price — must NOT blank out a cost
    // already recorded. Only an actually-typed number overrides it.
    String costArg = arg("cost");
    e.cost = costArg.length() ? costArg.toFloat() : rec.cost;
    storeAppendEvent(e);

    // 2) If this spool is on the scale, write the full OPT Main to its tag now.
    //    (Identity + material temps/class/type + weights.) syncTask's reconcile
    //    loop is idempotent, so a redundant later write is harmless.
    if (currentSpool() == (int)id) {
        xSemaphoreTake(gTagMutex, portMAX_DELAY);
        strlcpy(gTagMain.brand_name,            vendor.c_str(),  sizeof(gTagMain.brand_name));
        strlcpy(gTagMain.material_name,         display.c_str(), sizeof(gTagMain.material_name));
        strlcpy(gTagMain.material_abbreviation, abbr.c_str(), sizeof(gTagMain.material_abbreviation));
        memcpy(gTagMain.primary_color_rgba, rgba, 4);
        gTagMain.filament_diameter         = dia;
        gTagMain.nominal_netto_full_weight = nominal;
        gTagMain.actual_netto_full_weight  = nominal;   // new spool assumed full
        gTagMain.empty_container_weight    = empty;
        // Catalog-sourced temps are the vendor's own published numbers, more
        // specific than the config catalog's per-type defaults, so they win
        // when present. Class/type enums still come from the local catalog
        // either way — the OPT database's strings aren't mapped to our enum.
        if (haveCatTemps) {
            gTagMain.min_print_temperature = catPrintMin;
            gTagMain.max_print_temperature = catPrintMax;
            gTagMain.min_bed_temperature   = catBedMin;
            gTagMain.max_bed_temperature   = catBedMax;
        } else if (haveMat) {
            gTagMain.min_print_temperature = m.print_min;
            gTagMain.max_print_temperature = m.print_max;
            gTagMain.min_bed_temperature   = m.bed_min;
            gTagMain.max_bed_temperature   = m.bed_max;
        }
        if (haveMat) {
            gTagMain.material_class = m.cls;
            optSetMaterialType(gTagMain, m.type);
        }
        // Real vendor identity (GTIN, the three OPT UUIDs) — set unconditionally,
        // same as every other identity field above. This is a REPLACE, not a
        // merge: a manual/no-uuid submission must clear whatever a previous
        // catalog-sourced write left behind, or the tag ends up asserting a
        // vendor identity (a real package_uuid/GTIN) underneath data someone
        // just typed by hand for a different product entirely — worse than
        // never having written one, since it reads as verified when it isn't.
        // A nil UUID/zero GTIN is simply omitted on the next encode
        // (optUuidIsNil), which is the correct "no identity asserted" state.
        uint8_t idBytes[16];
        memset(gTagMain.package_uuid,  0, sizeof(gTagMain.package_uuid));
        memset(gTagMain.material_uuid, 0, sizeof(gTagMain.material_uuid));
        memset(gTagMain.brand_uuid,    0, sizeof(gTagMain.brand_uuid));
        if (hex32ToBytes(pkgUuid,   idBytes)) memcpy(gTagMain.package_uuid,  idBytes, 16);
        if (hex32ToBytes(matUuid,   idBytes)) memcpy(gTagMain.material_uuid, idBytes, 16);
        if (hex32ToBytes(brandUuid, idBytes)) memcpy(gTagMain.brand_uuid,    idBytes, 16);
        gTagMain.gtin = gtin;
        xSemaphoreGive(gTagMutex);
        gWriteMainPending     = true;
        gSpoolNeedsOnboarding = false;
    }

    // Optionally remember a free-typed vendor for reuse.
    if (vendor.length()) cfgVendorAdd(vendor.c_str());

    // Land on the spool that was just onboarded, not the dashboard. Submitting
    // eight fields and being returned to an aggregate roll-up gives no
    // confirmation that any of them took; the detail page shows the colour,
    // vendor, tare, nominal and weigh history for this exact record.
    req->redirect("/spool?id=" + String((unsigned)id));
}

// ── GET /erase — bulk tag-erase mode ──────────────────────────────────────────
// Tags are expensive enough that disposing of one with an empty reel is a
// real cost. Deliberately NOT a per-tag confirm-and-click flow — staff have
// already sorted a bin of spools they judge empty, so the friction that
// matters is per-BATCH ("am I sure I want to start erasing"), not per-tag.
// Turning erase mode on makes the station erase every tag placed while it's
// active IMMEDIATELY, no countdown (nfc_task.cpp's classification check wins
// over the confirm-by-inaction path the same way a forced TAGFORMAT does):
// place, it's gone, remove and place the next one. No automatic near-empty
// detection — staff decide what's empty; this only automates what happens
// once they've decided. The device screen shows "ERASE MODE" in red on Idle
// the instant this mode is toggled on, so it's obvious from across the room.
static void handleEraseForm(AsyncWebServerRequest* req) {
    String p = head("Erase Tag", "/erase");

    if (!gEraseModeActive) {
        p += "<div class='card'><p>Erase mode is off.</p>"
             "<p class='muted'>Turning it on makes the station erase every tag "
             "placed on the scale immediately &mdash; no per-tag confirmation, "
             "no countdown. Only start it once the spools you're about to "
             "place are ones you've already decided are empty.</p>"
             "<form method='POST' action='/api/erase/start' onsubmit=\"return "
             "confirm('Start erase mode? Every tag placed on the scale from now "
             "on will be erased immediately and its spool retired, until you "
             "stop it.')\">"
             "<button type='submit' style='background:#522;color:#eee;padding:8px 16px;"
             "font-size:14px;border-radius:4px;border:0;cursor:pointer'>"
             "Start erase mode</button></form></div>";
        p += FOOT;
        req->send(200, "text/html", p);
        return;
    }

    p += "<div class='card'>"
         "<p style='color:#f66'><strong>Erase mode: ON</strong> &mdash; every tag "
         "placed on the scale will be erased immediately.</p>"
         "<p class='muted' id='erase-status'>Waiting for a tag&hellip;</p>"
         "<form method='POST' action='/api/erase/stop'>"
         "<button type='submit' style='padding:8px 16px;font-size:14px;"
         "border-radius:4px;cursor:pointer'>Stop erase mode</button></form>"
         "</div>";

    // Polls the device's own state machine rather than tracking anything
    // page-side, so this reads correctly even if erase mode was turned on
    // from a different browser/tab. No countdown to render -- the device
    // jumps straight from a placed tag to formatting_and_registering.
    p += "<script>(function(){"
         "var el=document.getElementById('erase-status');"
         "function poll(){"
           "fetch('/api/status').then(function(r){return r.json();}).then(function(d){"
             // The idle auto-off (see ERASE_MODE_IDLE_TIMEOUT_SEC) can clear
             // the mode with nobody touching this page at all -- reload
             // rather than keep showing a stale "ON" panel and Stop button
             // for a mode that isn't actually active any more.
             "if(!d.erase_mode){location.reload();return;}"
             "var s=d.state;"
             "if(s==='idle'||s==='idle_no_wifi'){"
               "el.textContent='Waiting for a tag\\u2026';el.style.color='';"
             "}else if(s==='formatting_and_registering'){"
               "el.textContent='Erasing\\u2026';el.style.color='#f66';"
             "}else if(s==='present'){"
               "el.textContent='Done \\u2713 \\u2014 remove tag, place the next one';"
               "el.style.color='#8f8';"
             "}else{"
               "el.textContent='Working\\u2026';el.style.color='';"
             "}"
           "}).catch(function(){});"
         "}"
         "poll();setInterval(poll,400);"
         "})();</script>";

    p += FOOT;
    req->send(200, "text/html", p);
}

// ── POST /api/erase/start, /api/erase/stop — toggle bulk erase mode ──────────
// Retiring each old record happens automatically in sync_task.cpp's Resolving
// phase (matched by physical NFC UID) the moment a tag actually goes blank —
// these handlers only flip the mode flag nfcTask checks on every placement.
static void handleApiEraseStart(AsyncWebServerRequest* req) {
    if (!authOk(req)) return;
    gEraseModeActive = true;
    gEraseModeActivityMs = millis();   // starts the idle auto-off clock
    req->redirect("/erase");
}
static void handleApiEraseStop(AsyncWebServerRequest* req) {
    if (!authOk(req)) return;
    gEraseModeActive = false;
    req->redirect("/erase");
}

// ── Reorder: roll up on-hand per stock item, flag shortfalls ──────────────────
struct OnHand { uint16_t count; float grams; uint32_t product; };
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
