NormSohl/openprinttag-weigh-station/src/opt_tag.cpp

// SPDX-License-Identifier: GPL-3.0-or-later
// Copyright (C) 2026 Norm Sohl

#include "opt_tag.h"
#include <cbor.h>
#include <string.h>

// ── CBOR key constants ────────────────────────────────────────────────────────
// Meta keys (data/meta_fields.yaml)
static constexpr int META_KEY_MAIN_REGION_OFFSET = 0;
static constexpr int META_KEY_MAIN_REGION_SIZE   = 1;
static constexpr int META_KEY_AUX_REGION_OFFSET  = 2;
static constexpr int META_KEY_AUX_REGION_SIZE    = 3;

// Main keys (data/main_fields.yaml)
static constexpr int MAIN_KEY_INSTANCE_UUID              = 0;
static constexpr int MAIN_KEY_PACKAGE_UUID               = 1;
static constexpr int MAIN_KEY_MATERIAL_UUID              = 2;
static constexpr int MAIN_KEY_BRAND_UUID                 = 3;
static constexpr int MAIN_KEY_GTIN                       = 4;
static constexpr int MAIN_KEY_MATERIAL_CLASS             = 8;
static constexpr int MAIN_KEY_MATERIAL_TYPE              = 9;
static constexpr int MAIN_KEY_MATERIAL_NAME              = 10;
static constexpr int MAIN_KEY_BRAND_NAME                 = 11;
static constexpr int MAIN_KEY_WRITE_PROTECTION           = 13;
static constexpr int MAIN_KEY_NOMINAL_NETTO_FULL_WEIGHT  = 16;
static constexpr int MAIN_KEY_ACTUAL_NETTO_FULL_WEIGHT   = 17;
static constexpr int MAIN_KEY_EMPTY_CONTAINER_WEIGHT     = 18;
static constexpr int MAIN_KEY_PRIMARY_COLOR_RGBA         = 19;
static constexpr int MAIN_KEY_FILAMENT_DIAMETER          = 30;
static constexpr int MAIN_KEY_MIN_PRINT_TEMPERATURE      = 34;
static constexpr int MAIN_KEY_MAX_PRINT_TEMPERATURE      = 35;
static constexpr int MAIN_KEY_MIN_BED_TEMPERATURE        = 37;
static constexpr int MAIN_KEY_MAX_BED_TEMPERATURE        = 38;
static constexpr int MAIN_KEY_MATERIAL_ABBREVIATION      = 52;
static constexpr int MAIN_KEY_PRIMARY_COLOR_LAB          = 59;

// Auxiliary keys (data/aux_fields.yaml)
static constexpr int AUX_KEY_CONSUMED_WEIGHT    = 0;
static constexpr int AUX_KEY_PURCHASE_PRICE     = 6;
static constexpr int AUX_KEY_PURCHASE_CURRENCY  = 7;

// ── Helpers ───────────────────────────────────────────────────────────────────

// ── Guarded tinycbor accessors ────────────────────────────────────────────────
//
// tinycbor reports precondition violations with cbor_assert(), which on ESP-IDF
// aborts the firmware. There is no build flag that makes this safe: under NDEBUG
// cbor_assert() degrades to unreachable(), i.e. undefined behaviour, which is
// worse than the abort. The only defence is to test the type before every call.
//
// This is not theoretical. A tag left one block short by the block-79 write
// refusal decoded far enough to reach the Auxiliary map, then ran off the end of
// it, and cbor_value_advance() aborted at cborparser.c:508. nfcTask reads
// whatever is on the scale, so the reboot came straight back on the next boot:
// a loop that only stopped when the spool was lifted off.
//
// A tag whose CBOR is truncated or garbled must decode to "no". Never to a
// reboot.

// cbor_value_get_int64() asserts cbor_value_is_integer(), so checking its return
// value is not a guard — it aborts before it can return anything.
static bool cborTakeInt(const CborValue* v, int64_t* out) {
    if (!cbor_value_is_integer(v)) return false;
    return cbor_value_get_int64(v, out) == CborNoError;
}

// The copy_*_string calls assert the matching string type, and advance the
// iterator themselves when handed `v` as their `next`. True means "value
// consumed, do not step again".
static bool cborTakeText(CborValue* v, char* buf, size_t cap) {
    if (!cbor_value_is_text_string(v)) return false;
    size_t n = cap;
    return cbor_value_copy_text_string(v, buf, &n, v) == CborNoError;
}

// `outLen` receives how many bytes actually arrived, which matters for
// primary_color: OPT lets the alpha channel be left out, so a 3-byte colour is
// legal and means fully opaque.
static bool cborTakeBytes(CborValue* v, uint8_t* buf, size_t cap, size_t* outLen = nullptr) {
    if (!cbor_value_is_byte_string(v)) return false;
    size_t n = cap;
    if (cbor_value_copy_byte_string(v, buf, &n, v) != CborNoError) return false;
    if (outLen) *outLen = n;
    return true;
}

// Step over whatever the iterator points at. cbor_value_advance() handles fixed
// and container types alike (advance_recursive short-circuits to advance_internal
// for fixed ones), so we never need cbor_value_advance_fixed() and never have to
// prove "is this fixed?" — only that the position is valid at all, which is
// exactly the assert that fired.
static bool cborStep(CborValue* v) {
    if (cbor_value_get_type(v) == CborInvalidType) return false;
    return cbor_value_advance(v) == CborNoError;
}

// cbor_value_leave_container() asserts that the inner iterator is exhausted
// (recursed->type == CborInvalidType), so bailing out of a decode loop early and
// then "tidying up" is itself an abort. Only leave a container we actually
// finished; the outer iterator is unused afterwards either way.
// Returns true if the outer iterator actually advanced past the container. When
// it returns false the caller still has to step over it, which is safe:
// enter_container takes its argument by const pointer, so `outer` never moved.
static bool cborLeave(CborValue* outer, CborValue* inner) {
    if (cbor_value_is_container(outer) && cbor_value_get_type(inner) == CborInvalidType)
        return cbor_value_leave_container(outer, inner) == CborNoError;
    return false;
}

// Splice already-valid CBOR into an open container.
//
// tinycbor has no "append raw bytes" call, and re-encoding these pairs would
// mean decoding them first — which is precisely the knowledge we do not have,
// since they are the keys we do not model. So write at the encoder's cursor.
//
// Safe for the map optEncodeMain builds because it is INDEFINITE length:
// cbor_encoder_close_container() takes the UnknownLength branch and appends the
// break byte without ever checking `remaining`, so a spliced pair cannot
// desynchronise its bookkeeping. It would NOT be safe for a definite-length
// container.
//
// `end` goes NULL once tinycbor has overflowed and switched to counting mode,
// so it has to be tested before any pointer arithmetic.
static bool cborAppendRaw(CborEncoder* enc, const uint8_t* data, size_t len) {
    if (len == 0) return true;
    if (!enc->end) return false;
    if ((size_t)(enc->end - enc->data.ptr) < len) return false;
    memcpy(enc->data.ptr, data, len);
    enc->data.ptr += len;
    return true;
}

// Count the top-level key/value pairs of the map at the start of `data`. Parses
// our OWN just-encoded, valid CBOR, so cbor_value_advance()'s preconditions hold
// (the tinycbor-abort trap is for untrusted input). Returns -1 if not a map.
static int cborCountMapPairs(const uint8_t* data, size_t len) {
    CborParser p; CborValue it, map;
    if (cbor_parser_init(data, len, 0, &p, &it) != CborNoError) return -1;
    if (!cbor_value_is_map(&it)) return -1;
    if (cbor_value_enter_container(&it, &map) != CborNoError) return -1;
    int n = 0;
    while (!cbor_value_at_end(&map)) {
        if (cbor_value_advance(&map) != CborNoError) return -1;   // key
        if (cbor_value_at_end(&map)) return -1;                   // dangling key
        if (cbor_value_advance(&map) != CborNoError) return -1;   // value (skips nesting)
        n++;
    }
    return n;
}

// Rewrite an INDEFINITE-length map (0xBF … 0xFF) in `buf` to a DEFINITE-length
// one, in place. We encode indefinite so cborAppendRaw() can splice raw extra[]
// pairs, but the Prusa app's CBOR reader rejects indefinite-length containers, so
// every map we WRITE to a tag must be definite. For <=23 pairs the header is one
// byte (0xa0|n) — same size as 0xBF — so we just replace byte 0 and drop the
// trailing break; for 24..255 the header is two bytes (0xB8 n), net size
// unchanged (the dropped break pays for it). Returns the new length, or 0 on error.
static size_t cborMapToDefinite(uint8_t* buf, size_t len) {
    if (len < 2 || buf[0] != 0xBF || buf[len - 1] != 0xFF) return 0;
    int n = cborCountMapPairs(buf, len);
    if (n < 0) return 0;
    if (n <= 23) {
        buf[0] = (uint8_t)(0xA0 + n);   // definite header, 1 byte
        return len - 1;                 // drop the 0xFF break
    }
    if (n <= 255) {
        memmove(buf + 2, buf + 1, len - 2);   // shift pairs past the 2-byte header
        buf[0] = 0xB8; buf[1] = (uint8_t)n;
        return len;                            // 2 + (len-2) == len
    }
    return 0;   // > 255 pairs is impossible for an OPT section
}

// The reference implementation (fields.py CompactFloat) may encode floats as
// int (whole numbers), CBOR float16, float32, or float64.  Read whichever type
// is present and return it as float.
static bool cborGetFloat(const CborValue* val, float* out) {
    if (cbor_value_is_integer(val)) {
        int64_t i;
        if (cbor_value_get_int64(val, &i) != CborNoError) return false;
        *out = (float)i;
        return true;
    }
    if (cbor_value_is_float(val)) {
        return cbor_value_get_float(val, out) == CborNoError;
    }
    if (cbor_value_is_double(val)) {
        double d;
        if (cbor_value_get_double(val, &d) != CborNoError) return false;
        *out = (float)d;
        return true;
    }
    if (cbor_value_is_half_float(val)) {
        // tinycbor stores half-float as uint16; decode manually
        uint16_t hf;
        if (cbor_value_get_half_float(val, &hf) != CborNoError) return false;
        // Convert IEEE 754 half to float
        uint32_t sign     = (hf >> 15) & 0x1;
        uint32_t exp      = (hf >> 10) & 0x1F;
        uint32_t mantissa = hf & 0x3FF;
        uint32_t bits;
        if (exp == 0)       bits = (sign << 31) | ((mantissa) << 13);
        else if (exp == 31) bits = (sign << 31) | (0xFF << 23) | (mantissa << 13);
        else                bits = (sign << 31) | ((exp + 112) << 23) | (mantissa << 13);
        memcpy(out, &bits, 4);
        return true;
    }
    return false;
}

// Locate the OPT NDEF record payload within a raw tag block dump.
// Sets *payloadOut and *payloadLen on success, returns true.
//
// Tag layout (nfc_initialize.py):
//   [0..3]  Capability Container — must start with 0xE1
//   [4..]   TLV sequence:
//             0x03 <1- or 3-byte length> <NDEF message>
//             0xFE  Terminator
//
// NDEF record header bytes (TNF=0x02 = MIME type):
//   [0]  flags: MB|ME|CF|SR|IL|TNF[2:0]
//   [1]  type_length
//   [2]  payload_length  (1 byte when SR=1, 4 bytes when SR=0)
//   ...  id_length       (only present when IL=1)
//   ...  type            (type_length bytes) — must equal OPT_MIME_TYPE
//   ...  id              (id_length bytes, if IL=1)
//   ...  payload         (payload_length bytes) — our CBOR data
static bool findNdefPayload(const uint8_t* tagBytes, size_t len,
                             const uint8_t** payloadOut, size_t* payloadLen) {
    if (len < OPT_CC_SIZE + 2) return false;
    if (tagBytes[0] != 0xE1) return false;   // not a valid NDEF tag

    // ── Walk TLV sequence starting after the 4-byte Capability Container ──────
    size_t pos = OPT_CC_SIZE;
    while (pos < len) {
        uint8_t tlvType = tagBytes[pos++];
        if (tlvType == 0xFE) break;                        // Terminator
        if (tlvType == 0x00) continue;                     // Null TLV — skip

        // Read TLV length (1-byte or 3-byte form)
        if (pos >= len) return false;
        size_t tlvLen;
        if (tagBytes[pos] == 0xFF) {
            if (pos + 2 >= len) return false;
            tlvLen = ((size_t)tagBytes[pos + 1] << 8) | tagBytes[pos + 2];
            pos += 3;
        } else {
            tlvLen = tagBytes[pos++];
        }
        if (pos + tlvLen > len) return false;

        if (tlvType != 0x03) { pos += tlvLen; continue; }  // not an NDEF TLV

        // ── Parse NDEF message ────────────────────────────────────────────────
        const uint8_t* msg    = tagBytes + pos;
        size_t         msgLen = tlvLen;
        size_t         mpos   = 0;

        while (mpos < msgLen) {
            if (mpos >= msgLen) break;
            uint8_t flags      = msg[mpos++];
            uint8_t tnf        = flags & 0x07;
            bool    sr         = (flags >> 4) & 1;   // Short Record
            bool    il         = (flags >> 3) & 1;   // ID Length present

            if (mpos >= msgLen) break;
            uint8_t typeLen    = msg[mpos++];

            uint32_t plen;
            if (sr) {
                if (mpos >= msgLen) break;
                plen = msg[mpos++];
            } else {
                if (mpos + 3 >= msgLen) break;
                plen = ((uint32_t)msg[mpos] << 24) | ((uint32_t)msg[mpos+1] << 16)
                     | ((uint32_t)msg[mpos+2] << 8) | msg[mpos+3];
                mpos += 4;
            }

            uint8_t idLen = 0;
            if (il) {
                if (mpos >= msgLen) break;
                idLen = msg[mpos++];
            }

            const uint8_t* recType = msg + mpos;   mpos += typeLen;
            mpos += idLen;                          // skip ID field
            const uint8_t* payload = msg + mpos;   mpos += plen;

            if (mpos > msgLen) break;

            // TNF 0x02 = MIME type record
            if (tnf == 0x02
                && typeLen == OPT_MIME_TYPE_LEN
                && memcmp(recType, OPT_MIME_TYPE, OPT_MIME_TYPE_LEN) == 0) {
                *payloadOut = payload;
                *payloadLen = plen;
                return true;
            }
        }

        pos += tlvLen;
    }
    return false;
}

// ── Public API ────────────────────────────────────────────────────────────────

bool optIsBlank(const uint8_t* tagBytes, size_t len) {
    if (!tagBytes || len < OPT_CC_SIZE) return true;

    // A formatted tag has 0xE1 as the first CC byte (NDEF magic).
    if (tagBytes[0] != 0xE1) return true;

    // If no payload can be located, treat as blank.
    const uint8_t* payload;
    size_t payloadLen;
    if (!findNdefPayload(tagBytes, len, &payload, &payloadLen)) return true;

    // A blank payload is an empty CBOR map: definite 0xA0, or indefinite 0xBF 0xFF.
    // Do NOT treat a non-empty indefinite map (0xBF <key>...) as blank — that is the Meta section.
    if (payloadLen == 0 || payload[0] == 0xA0) return true;
    return (payload[0] == 0xBF && payloadLen >= 2 && payload[1] == 0xFF);
}

bool optDecode(const uint8_t* tagBytes, size_t len,
               OptMeta* meta, OptMain* main, OptAuxiliary* aux) {
    const uint8_t* payload;
    size_t payloadLen;
    if (!findNdefPayload(tagBytes, len, &payload, &payloadLen)) return false;

    // ── Decode Meta region (always at offset 0 of payload) ──────────────────
    CborParser parser;
    CborValue  it, map;
    if (cbor_parser_init(payload, payloadLen, 0, &parser, &it) != CborNoError) return false;
    if (!cbor_value_is_map(&it)) return false;

    uint16_t mainOffset = 0, auxOffset = 0;
    bool sawMainOffset = false;
    if (cbor_value_enter_container(&it, &map) == CborNoError) {
        while (!cbor_value_at_end(&map)) {
            int64_t key;
            if (!cborTakeInt(&map, &key)) break;   // key must be an integer
            if (!cborStep(&map)) break;            // now on the value
            int64_t v;
            switch (key) {
                case META_KEY_MAIN_REGION_OFFSET:
                    if (cborTakeInt(&map, &v)) {
                        mainOffset = (uint16_t)v;
                        sawMainOffset = true;
                        if (meta) meta->main_region_offset = mainOffset;
                    }
                    break;
                case META_KEY_MAIN_REGION_SIZE:
                    if (cborTakeInt(&map, &v) && meta) meta->main_region_size = (uint16_t)v;
                    break;
                case META_KEY_AUX_REGION_OFFSET:
                    if (cborTakeInt(&map, &v)) {
                        auxOffset = (uint16_t)v;
                        if (meta) meta->aux_region_offset = auxOffset;
                    }
                    break;
                case META_KEY_AUX_REGION_SIZE:
                    if (cborTakeInt(&map, &v) && meta) meta->aux_region_size = (uint16_t)v;
                    break;
            }
            if (!cborStep(&map)) break;
        }
        cborLeave(&it, &map);
    }

    // Per the OPT reference, main_region_offset DEFAULTS to the meta section size
    // (Main sits immediately after the Meta) when the key is absent — which is how
    // the Prusa app writes it. Without this default we would decode Main at offset
    // 0 (the Meta itself) and read a nil UUID. `it` points just past the Meta.
    if (!sawMainOffset) {
        mainOffset = (uint16_t)(cbor_value_get_next_byte(&it) - payload);
        if (meta) meta->main_region_offset = mainOffset;
    }

    // ── Decode Main region ────────────────────────────────────────────────────
    if (main && mainOffset < payloadLen) {
        CborParser mp; CborValue mi, mm;
        if (cbor_parser_init(payload + mainOffset, payloadLen - mainOffset, 0, &mp, &mi) == CborNoError &&
            cbor_value_is_map(&mi) && cbor_value_enter_container(&mi, &mm) == CborNoError) {
            while (!cbor_value_at_end(&mm)) {
                // Remember where this key/value pair starts, so an unrecognised
                // one can be copied out verbatim once we know its extent.
                const uint8_t* pairStart = cbor_value_get_next_byte(&mm);
                bool known = true;
                int64_t key;
                if (!cborTakeInt(&mm, &key)) break;
                if (!cborStep(&mm)) break;
                // The string cases advance the iterator themselves; the scalar
                // cases leave it on the value for the step at the bottom. A
                // failed take (wrong type on the tag) falls through to that step
                // too, so an unexpected value is skipped rather than fatal.
                bool consumed = false;
                int64_t v;
                switch (key) {
                    case MAIN_KEY_INSTANCE_UUID:
                        consumed = cborTakeBytes(&mm, main->instance_uuid, 16); break;
                    // NOTE: every case added here MUST have a matching encode
                    // below. Since optDecode() started preserving unrecognised
                    // keys verbatim, half-modelling a field is worse than not
                    // modelling it: claiming it here removes it from the
                    // passthrough, and without an encode it is then dropped on
                    // the next rewrite. Before passthrough existed it was lost
                    // either way, so this is a new way to get it wrong.
                    case MAIN_KEY_PACKAGE_UUID:
                        consumed = cborTakeBytes(&mm, main->package_uuid, 16); break;
                    case MAIN_KEY_MATERIAL_UUID:
                        consumed = cborTakeBytes(&mm, main->material_uuid, 16); break;
                    case MAIN_KEY_BRAND_UUID:
                        consumed = cborTakeBytes(&mm, main->brand_uuid, 16); break;
                    case MAIN_KEY_GTIN:
                        if (cborTakeInt(&mm, &v) && v > 0) main->gtin = (uint64_t)v;
                        break;
                    case MAIN_KEY_BRAND_NAME:
                        consumed = cborTakeText(&mm, main->brand_name, sizeof(main->brand_name)); break;
                    case MAIN_KEY_MATERIAL_NAME:
                        consumed = cborTakeText(&mm, main->material_name, sizeof(main->material_name)); break;
                    case MAIN_KEY_MATERIAL_ABBREVIATION:
                        consumed = cborTakeText(&mm, main->material_abbreviation, sizeof(main->material_abbreviation)); break;
                    // [L*, a*, b*]. Each element may arrive as int, float16,
                    // float32 or float64 (OPT's CompactFloat), so cborGetFloat
                    // handles the element and we only manage the array walk.
                    // Anything short of three good numbers leaves has_lab false
                    // — a partial measurement is not a measurement.
                    case MAIN_KEY_PRIMARY_COLOR_LAB: {
                        if (!cbor_value_is_array(&mm)) break;
                        CborValue el;
                        if (cbor_value_enter_container(&mm, &el) != CborNoError) break;
                        float lab[3] = {0, 0, 0};
                        int got = 0;
                        while (got < 3 && !cbor_value_at_end(&el)) {
                            if (!cborGetFloat(&el, &lab[got])) break;
                            got++;
                            if (!cborStep(&el)) break;
                        }
                        if (got == 3) {
                            memcpy(main->primary_color_lab, lab, sizeof(lab));
                            main->has_lab = true;
                        }
                        // If we could not leave cleanly the iterator never moved
                        // (enter_container takes `outer` by const pointer), so
                        // the step at the bottom skips the whole array instead.
                        consumed = cborLeave(&mm, &el);
                        break;
                    }
                    case MAIN_KEY_PRIMARY_COLOR_RGBA: {
                        size_t got = 0;
                        consumed = cborTakeBytes(&mm, main->primary_color_rgba, 4, &got);
                        // "The alpha channel can be left out, in which case the
                        // data should have 3 bytes instead of 4 and the color
                        // will be considered fully opaque." Without this a
                        // 3-byte colour from another vendor's tag lands with
                        // alpha 0 and reads as "no colour assigned".
                        if (consumed && got == 3) main->primary_color_rgba[3] = 0xFF;
                        break;
                    }
                    case MAIN_KEY_NOMINAL_NETTO_FULL_WEIGHT: cborGetFloat(&mm, &main->nominal_netto_full_weight); break;
                    case MAIN_KEY_ACTUAL_NETTO_FULL_WEIGHT:  cborGetFloat(&mm, &main->actual_netto_full_weight);  break;
                    case MAIN_KEY_EMPTY_CONTAINER_WEIGHT:    cborGetFloat(&mm, &main->empty_container_weight);    break;
                    case MAIN_KEY_FILAMENT_DIAMETER:         cborGetFloat(&mm, &main->filament_diameter);         break;
                    case MAIN_KEY_MIN_PRINT_TEMPERATURE: if (cborTakeInt(&mm, &v)) main->min_print_temperature = (int16_t)v; break;
                    case MAIN_KEY_MAX_PRINT_TEMPERATURE: if (cborTakeInt(&mm, &v)) main->max_print_temperature = (int16_t)v; break;
                    case MAIN_KEY_MIN_BED_TEMPERATURE:   if (cborTakeInt(&mm, &v)) main->min_bed_temperature   = (int16_t)v; break;
                    case MAIN_KEY_MAX_BED_TEMPERATURE:   if (cborTakeInt(&mm, &v)) main->max_bed_temperature   = (int16_t)v; break;
                    case MAIN_KEY_MATERIAL_CLASS: if (cborTakeInt(&mm, &v)) main->material_class = (int8_t)v; break;
                    case MAIN_KEY_MATERIAL_TYPE:  if (cborTakeInt(&mm, &v)) main->material_type  = (int8_t)v; break;
                    default: known = false; break;
                    // Whether this tag's Main section may be rewritten at
                    // all. Decoded but never encoded: we do not protect our
                    // own tags, and an absent key means "not protected".
                    case MAIN_KEY_WRITE_PROTECTION: if (cborTakeInt(&mm, &v)) main->write_protection = (int8_t)v; break;
                }
                if (!consumed && !cborStep(&mm)) break;
                if (known) optMarkPresent(*main, (int)key);

                // Now that the value has been stepped over, the pair's extent is
                // known. Keep the bytes of anything we did not understand.
                if (!known) {
                    const uint8_t* pairEnd = cbor_value_get_next_byte(&mm);
                    if (pairEnd > pairStart) {
                        const size_t n = (size_t)(pairEnd - pairStart);
                        if (main->extra_len + n <= sizeof(main->extra)) {
                            memcpy(main->extra + main->extra_len, pairStart, n);
                            main->extra_len += (uint16_t)n;
                        } else {
                            main->extra_overflow = true;
                        }
                    }
                }
            }
            cborLeave(&mi, &mm);
        }
    }

    // ── Decode Auxiliary region ───────────────────────────────────────────────
    // Same pairStart/consumed/passthrough shape as Main's loop above, for the
    // same two reasons: (1) the old unconditional second cborStep() here did
    // not know some value types (e.g. a text string) already advance the
    // iterator themselves when read, and double-advancing crashed the
    // firmware on a tag carrying any Aux key besides consumed_weight -- (2)
    // whatever we don't model must be preserved, not dropped, into extra[].
    if (aux && auxOffset > 0 && auxOffset < payloadLen) {
        CborParser ap; CborValue ai, am;
        if (cbor_parser_init(payload + auxOffset, payloadLen - auxOffset, 0, &ap, &ai) == CborNoError &&
            cbor_value_is_map(&ai) && cbor_value_enter_container(&ai, &am) == CborNoError) {
            while (!cbor_value_at_end(&am)) {
                const uint8_t* pairStart = cbor_value_get_next_byte(&am);
                bool known = true;
                int64_t key;
                if (!cborTakeInt(&am, &key)) break;
                if (!cborStep(&am)) break;
                bool consumed = false;
                switch (key) {
                    case AUX_KEY_CONSUMED_WEIGHT:
                        cborGetFloat(&am, &aux->consumed_weight); break;
                    case AUX_KEY_PURCHASE_PRICE:
                        if (cborGetFloat(&am, &aux->purchase_price)) aux->has_purchase = true;
                        break;
                    case AUX_KEY_PURCHASE_CURRENCY:
                        consumed = cborTakeText(&am, aux->purchase_currency, sizeof(aux->purchase_currency));
                        break;
                    default: known = false; break;
                }
                if (!consumed && !cborStep(&am)) break;

                if (!known) {
                    const uint8_t* pairEnd = cbor_value_get_next_byte(&am);
                    if (pairEnd > pairStart) {
                        const size_t n = (size_t)(pairEnd - pairStart);
                        if (aux->extra_len + n <= sizeof(aux->extra)) {
                            memcpy(aux->extra + aux->extra_len, pairStart, n);
                            aux->extra_len += (uint8_t)n;
                        } else {
                            aux->extra_overflow = true;
                        }
                    }
                }
            }
            cborLeave(&ai, &am);
        }
    }

    return true;
}

// Text key, omitted when empty, cut to maxBytes without splitting a UTF-8
// sequence (backing up over continuation bytes 10xxxxxx).
static void encodeTextMax(CborEncoder* map, int key, const char* s, size_t maxBytes) {
    const size_t n = optClampedLen(s, maxBytes);
    if (n == 0) return;
    cbor_encode_int(map, key);
    cbor_encode_text_string(map, s, n);
}
static void encodeFloatIf(CborEncoder* map, int key, float v, const OptMain& m) {
    if (v == 0.0f && !optIsPresent(m, key)) return;
    cbor_encode_int(map, key);
    cbor_encode_float(map, v);
}
static void encodeIntIf(CborEncoder* map, int key, int64_t v, const OptMain& m) {
    if (v == 0 && !optIsPresent(m, key)) return;
    cbor_encode_int(map, key);
    cbor_encode_int(map, v);
}

size_t optEncodeMain(const OptMain& m, uint8_t* buf, size_t maxLen) {
    CborEncoder enc, map;
    cbor_encoder_init(&enc, buf, maxLen, 0);
    cbor_encoder_create_map(&enc, &map, CborIndefiniteLength);

    cbor_encode_int(&map, MAIN_KEY_INSTANCE_UUID);
    cbor_encode_byte_string(&map, m.instance_uuid, 16);

    // Identity, only what the tag actually carried. Writing a nil UUID would
    // assert an identity the vendor never claimed.
    if (!optUuidIsNil(m.package_uuid)) {
        cbor_encode_int(&map, MAIN_KEY_PACKAGE_UUID);
        cbor_encode_byte_string(&map, m.package_uuid, 16);
    }
    if (!optUuidIsNil(m.material_uuid)) {
        cbor_encode_int(&map, MAIN_KEY_MATERIAL_UUID);
        cbor_encode_byte_string(&map, m.material_uuid, 16);
    }
    if (!optUuidIsNil(m.brand_uuid)) {
        cbor_encode_int(&map, MAIN_KEY_BRAND_UUID);
        cbor_encode_byte_string(&map, m.brand_uuid, 16);
    }
    if (m.gtin) {
        cbor_encode_int(&map, MAIN_KEY_GTIN);
        cbor_encode_uint(&map, m.gtin);
    }

    // Text, only when there is some, and never past the spec's max_length
    // (data/main_fields.yaml): brand_name 31, material_name 63,
    // material_abbreviation 7. Our buffers are larger than that, so a long
    // vendor name typed on the web form would otherwise produce a tag other
    // OPT readers are entitled to reject. An empty string is not a value:
    // OPT says a missing abbreviation inherits the material type's.
    encodeTextMax(&map, MAIN_KEY_BRAND_NAME,            m.brand_name,            OPT_MAX_BRAND_NAME);
    encodeTextMax(&map, MAIN_KEY_MATERIAL_NAME,         m.material_name,         OPT_MAX_MATERIAL_NAME);
    encodeTextMax(&map, MAIN_KEY_MATERIAL_ABBREVIATION, m.material_abbreviation, OPT_MAX_MATERIAL_ABBREVIATION);

    // Only when a colour is actually assigned. OPT says primary_color "can be
    // null" when a material has no single colour, and an absent key is the
    // honest way to say "unknown" — writing 00 00 00 00 would tell every other
    // reader this spool is transparent black.
    if (m.primary_color_rgba[3] != 0) {
        cbor_encode_int(&map, MAIN_KEY_PRIMARY_COLOR_RGBA);
        cbor_encode_byte_string(&map, m.primary_color_rgba, 4);
    }

    // Measured colour, only if something actually measured it. Absent means
    // unmeasured; the spec forbids approximating this from RGB, so there is no
    // fallback to invent here.
    if (m.has_lab) {
        cbor_encode_int(&map, MAIN_KEY_PRIMARY_COLOR_LAB);
        CborEncoder lab;
        cbor_encoder_create_array(&map, &lab, 3);
        for (int i = 0; i < 3; i++) cbor_encode_float(&lab, m.primary_color_lab[i]);
        cbor_encoder_close_container(&map, &lab);
    }

    // Encode floats as float32; reference uses CompactFloat (may use int for whole numbers)
    // TODO: mirror CompactFloat logic to minimise tag bytes if space becomes an issue
    // Numbers: a key the tag carried is written back as it was (even a 0 —
    // it was the tag's value, not ours to drop); otherwise only a value
    // someone actually set. Zero-initialised structs make "never set" read as
    // 0, and 0 g, 0 mm or 0 °C is not information: writing it would state on
    // someone's tag a figure nobody gave. See OptMain::present.
    encodeFloatIf(&map, MAIN_KEY_NOMINAL_NETTO_FULL_WEIGHT, m.nominal_netto_full_weight, m);
    encodeFloatIf(&map, MAIN_KEY_ACTUAL_NETTO_FULL_WEIGHT,  m.actual_netto_full_weight,  m);
    encodeFloatIf(&map, MAIN_KEY_EMPTY_CONTAINER_WEIGHT,    m.empty_container_weight,    m);
    encodeFloatIf(&map, MAIN_KEY_FILAMENT_DIAMETER,         m.filament_diameter,         m);

    // material_class is REQUIRED by OPT, so always written; 0 is FFF, which
    // is every spool this station handles.
    cbor_encode_int(&map, MAIN_KEY_MATERIAL_CLASS);
    cbor_encode_int(&map, m.material_class);

    // material_type 0 is PLA, so zero cannot mean unset here: written only
    // if the tag carried it or a writer set it (optSetMaterialType). OPT says
    // it "can be left unspecified" when no type fits.
    if (optIsPresent(m, MAIN_KEY_MATERIAL_TYPE)) {
        cbor_encode_int(&map, MAIN_KEY_MATERIAL_TYPE);
        cbor_encode_int(&map, m.material_type);
    }

    encodeIntIf(&map, MAIN_KEY_MIN_PRINT_TEMPERATURE, m.min_print_temperature, m);
    encodeIntIf(&map, MAIN_KEY_MAX_PRINT_TEMPERATURE, m.max_print_temperature, m);
    encodeIntIf(&map, MAIN_KEY_MIN_BED_TEMPERATURE,   m.min_bed_temperature,   m);
    encodeIntIf(&map, MAIN_KEY_MAX_BED_TEMPERATURE,   m.max_bed_temperature,   m);

    // Everything the tag carried that this firmware does not model, back
    // untouched. Last, so our own keys keep their order and a reader diffing two
    // of our writes sees a stable prefix.
    if (!cborAppendRaw(&map, m.extra, m.extra_len)) return 0;

    cbor_encoder_close_container(&enc, &map);
    // Emit a DEFINITE-length map — the Prusa app rejects indefinite CBOR.
    return cborMapToDefinite(buf, cbor_encoder_get_buffer_size(&enc, buf));
}

size_t optEncodeAux(const OptAuxiliary& aux, uint8_t* buf, size_t maxLen) {
    CborEncoder enc, map;
    cbor_encoder_init(&enc, buf, maxLen, 0);
    cbor_encoder_create_map(&enc, &map, CborIndefiniteLength);

    cbor_encode_int(&map, AUX_KEY_CONSUMED_WEIGHT);
    cbor_encode_float(&map, aux.consumed_weight);

    // Omitted entirely when unset, not written as 0/"" -- same reasoning as
    // Main's primary_color_lab: a real $0 purchase is implausible, and OPT
    // readers should see "not recorded" as absence, not as a free spool.
    if (aux.has_purchase) {
        cbor_encode_int(&map, AUX_KEY_PURCHASE_PRICE);
        cbor_encode_float(&map, aux.purchase_price);
        cbor_encode_int(&map, AUX_KEY_PURCHASE_CURRENCY);
        cbor_encode_text_string(&map, aux.purchase_currency, strlen(aux.purchase_currency));
    }

    // Whatever this tag carried that we don't model, back untouched -- same
    // reasoning as Main's extra[] splice, at Aux's much smaller scale.
    if (!cborAppendRaw(&map, aux.extra, aux.extra_len)) return 0;

    cbor_encoder_close_container(&enc, &map);
    return cborMapToDefinite(buf, cbor_encoder_get_buffer_size(&enc, buf));
}

size_t optPayloadOffset(const uint8_t* tagBytes, size_t len) {
    const uint8_t* payload;
    size_t payloadLen;
    if (!findNdefPayload(tagBytes, len, &payload, &payloadLen)) return SIZE_MAX;
    return (size_t)(payload - tagBytes);
}

bool optPayloadExtent(const uint8_t* tagBytes, size_t len,
                      size_t* outOffset, size_t* outLength) {
    const uint8_t* payload;
    size_t payloadLen;
    if (!findNdefPayload(tagBytes, len, &payload, &payloadLen)) return false;
    if (outOffset) *outOffset = (size_t)(payload - tagBytes);
    if (outLength) *outLength = payloadLen;
    return true;
}

bool optRegionBounds(const OptMeta& meta, bool aux, size_t payloadLen,
                     size_t* outStart, size_t* outEnd) {
    if (aux && meta.aux_region_offset == 0) return false;   // no Aux region
    const size_t start = aux ? meta.aux_region_offset : meta.main_region_offset;
    const size_t size  = aux ? meta.aux_region_size   : meta.main_region_size;
    const size_t other = aux ? meta.main_region_offset : meta.aux_region_offset;
    size_t end;
    if (size > 0)                         end = start + size;
    else if (other > start)               end = other;      // next region begins
    else                                  end = payloadLen;
    if (end > payloadLen) end = payloadLen;
    if (start >= end) return false;
    if (outStart) *outStart = start;
    if (outEnd)   *outEnd   = end;
    return true;
}

size_t optBuildBlankTag(uint8_t numBlocks, uint8_t blockSize,
                        uint8_t* outBuf, size_t outBufLen, OptMeta* outMeta) {
    const size_t tagSize = (size_t)numBlocks * blockSize;
    if (!outBuf || tagSize > outBufLen || numBlocks < 2) return SIZE_MAX;

    // Meta is now a MINIMAL definite map {aux_region_offset: X} (~4 bytes), and
    // Main sits IMMEDIATELY after it (mainOff = metaLen below) — matching the OPT
    // reference, whose blank tag writes exactly this and defaults main_region_offset
    // to the meta size. MAIN_REGION_OFFSET / EMPTY_MAP_SIZE are no longer used to
    // PLACE anything; they survive only as a conservative floor in the room checks
    // (reserve ≥16+2 bytes before Aux — far more than the ~5 the real Main needs).
    static const size_t META_SECTION_SIZE  = 16;
    static const size_t MAIN_REGION_OFFSET = META_SECTION_SIZE;  // room-check floor only
    static const size_t EMPTY_MAP_SIZE     = 2;   // room-check floor only

    // Bytes reserved for the Auxiliary region.
    //
    // This has to hold a WRITTEN Aux map, not the empty one the format leaves
    // behind. {0: float32} encodes as BF 00 FA xx xx xx xx FF — 8 bytes — and
    // the region used to reserve 2, at the very last block. That is why
    // Auxiliary write-back never worked, and how a tag got bricked: on the
    // shortened layout the block-79 workaround produces, the 8-byte write
    // spanned the final two blocks, the last one refused, and the tag was left
    // carrying a CBOR map that opens and never closes. Every later read then
    // aborted the firmware inside tinycbor.
    //
    // 24 leaves room for the aux fields OPT defines beyond consumed_weight.
    static const size_t AUX_REGION_SIZE = 24;

    // Aux goes at the end, block-aligned (writeSection() addresses whole
    // blocks), with the TLV terminator after it — and the whole of it inside
    // the layout, so no write ever has to reach past the last block. Rounding
    // the start DOWN to a block boundary is what guarantees that.
    const size_t auxTail = AUX_REGION_SIZE + 1;          // region + terminator
    if (tagSize < auxTail + blockSize) return SIZE_MAX;
    const size_t auxAbsStart = ((tagSize - auxTail) / blockSize) * blockSize;

    // ── Choose SR bit and TLV length encoding ────────────────────────────────
    // Start with SR=1 (1-byte payload length, payload ≤ 255 bytes), 1-byte TLV length.
    bool   useSR1       = true;
    size_t ndefHdrSize  = 1 + 1 + 1 + OPT_MIME_TYPE_LEN;  // 31 bytes (SR=1)
    size_t tlvLenSize   = 1;
    size_t payloadStart = OPT_CC_SIZE + 1 + tlvLenSize + ndefHdrSize;

    if (auxAbsStart < payloadStart + MAIN_REGION_OFFSET + EMPTY_MAP_SIZE) return SIZE_MAX;
    size_t cborPayloadLen = auxAbsStart + AUX_REGION_SIZE - payloadStart;
    size_t ndefMsgLen     = ndefHdrSize + cborPayloadLen;

    if (cborPayloadLen > 255) {
        // Payload too large for SR=1; switch to SR=0 (4-byte payload length field).
        useSR1       = false;
        ndefHdrSize  = 1 + 1 + 4 + OPT_MIME_TYPE_LEN;  // 34 bytes (SR=0)
        payloadStart = OPT_CC_SIZE + 1 + tlvLenSize + ndefHdrSize;
        if (auxAbsStart < payloadStart + MAIN_REGION_OFFSET + EMPTY_MAP_SIZE) return SIZE_MAX;
        cborPayloadLen = auxAbsStart + AUX_REGION_SIZE - payloadStart;
        ndefMsgLen     = ndefHdrSize + cborPayloadLen;
    }

    if (ndefMsgLen > 254) {
        // NDEF message too large for 1-byte TLV length; switch to 3-byte (0xFF hi lo).
        tlvLenSize   = 3;
        payloadStart = OPT_CC_SIZE + 1 + tlvLenSize + ndefHdrSize;
        if (auxAbsStart < payloadStart + MAIN_REGION_OFFSET + EMPTY_MAP_SIZE) return SIZE_MAX;
        cborPayloadLen = auxAbsStart + AUX_REGION_SIZE - payloadStart;
        ndefMsgLen     = ndefHdrSize + cborPayloadLen;
    }

    const size_t auxOffset     = auxAbsStart - payloadStart;
    const size_t terminatorPos = auxAbsStart + AUX_REGION_SIZE;
    if (terminatorPos >= tagSize) return SIZE_MAX;

    // ── Write tag bytes ───────────────────────────────────────────────────────
    memset(outBuf, 0, tagSize);

    // ── Capability Container (NFC Forum Type 5 Tag, 4-byte form) ─────────────
    //
    // Byte 2 is MLEN. Match the OPT reference EXACTLY: nfc_initialize.py writes
    // `capability_container[2] = args.size // 8`, where args.size is the WHOLE
    // formatted tag size — CC included (its `full_data` = CC + TLV + NDEF +
    // terminator is asserted == args.size). So MLEN = tagSize / 8, NOT
    // (tagSize - CC) / 8 and NOT the block count.
    //
    // History of getting this wrong, each caught somewhere we could not see:
    //   - until 2026-08-10 this wrote the BLOCK COUNT (79/80), declaring ~4-8x
    //     the physical tag;
    //   - then (tagSize - CC) / 8, on the theory that MLEN counts only the T5T
    //     Area after the CC. It was "confirmed" against a Prusa-app tag reading
    //     0x27 — but that tag was 312 bytes (312/8 = 39 = 0x27), and ours was
    //     320; the two formulas happened to agree only because the sizes differed.
    //     On a 320-byte tag the reference writes 40 = 0x28 and this wrote 39.
    // Overstating by the 4-byte CC is harmless in practice: no reader walks to
    // MLEN*8 — the reference reader (record.py) loops TLVs to the 0xFE terminator
    // and never bounds by cc_capacity. Matching Prusa is the point, so use its
    // formula. Integer division rounds DOWN.
    if (tagSize / 8 > 255) return SIZE_MAX;   // needs the 8-byte (0xE2) CC form
    outBuf[0] = 0xE1;                         // magic, 4-byte CC
    outBuf[1] = 0x40;                         // version 1.0, read/write, no restrictions
    outBuf[2] = (uint8_t)(tagSize / 8);       // MLEN = whole tag size / 8 (per reference)
    // Capability flags, tag-specific. Bit 0 = MBREAD ("Read Multiple Blocks"),
    // which the SLIX2 supports. Bit 1 would be IPREAD ("Inventory Page Read"),
    // which it does not — matching the reference implementation's comment.
    outBuf[3] = 0x01;

    // NDEF TLV
    size_t p = OPT_CC_SIZE;
    outBuf[p++] = 0x03;
    if (tlvLenSize == 1) {
        outBuf[p++] = (uint8_t)ndefMsgLen;
    } else {
        outBuf[p++] = 0xFF;
        outBuf[p++] = (uint8_t)(ndefMsgLen >> 8);
        outBuf[p++] = (uint8_t)(ndefMsgLen & 0xFF);
    }

    // NDEF record header
    outBuf[p++] = useSR1 ? 0xD2 : 0xC2;       // MB=ME=1, SR=(0/1), TNF=0x02
    outBuf[p++] = (uint8_t)OPT_MIME_TYPE_LEN;
    if (useSR1) {
        outBuf[p++] = (uint8_t)cborPayloadLen;
    } else {
        outBuf[p++] = (uint8_t)(cborPayloadLen >> 24);
        outBuf[p++] = (uint8_t)(cborPayloadLen >> 16);
        outBuf[p++] = (uint8_t)(cborPayloadLen >> 8);
        outBuf[p++] = (uint8_t)(cborPayloadLen & 0xFF);
    }
    memcpy(outBuf + p, OPT_MIME_TYPE, OPT_MIME_TYPE_LEN);
    p += OPT_MIME_TYPE_LEN;
    // p == payloadStart here

    // Meta CBOR (at payload offset 0)
    uint8_t metaBuf[24];
    CborEncoder enc, map;
    cbor_encoder_init(&enc, metaBuf, sizeof(metaBuf), 0);
    cbor_encoder_create_map(&enc, &map, CborIndefiniteLength);
    // Match the Prusa app's MINIMAL Meta: only aux_region_offset. We omit
    // main_region_offset (it defaults to the meta size — Main immediately follows),
    // main_region_size, and aux_region_size. A main_region_size of 0, which we used
    // to write, reads as "Main is empty" to the app and made it reject our tags.
    cbor_encode_int(&map, META_KEY_AUX_REGION_OFFSET);  cbor_encode_int(&map, (int64_t)auxOffset);
    cbor_encoder_close_container(&enc, &map);
    // DEFINITE-length Meta — the Prusa app rejects indefinite CBOR.
    size_t metaLen = cborMapToDefinite(metaBuf, cbor_encoder_get_buffer_size(&enc, metaBuf));
    if (metaLen == 0 || metaLen > META_SECTION_SIZE) return SIZE_MAX;
    memcpy(outBuf + p, metaBuf, metaLen);
    // Main sits immediately after the Meta (no padding), like Prusa's tags — and
    // the decoder's default for an absent main_region_offset is this same meta size.
    const size_t mainOff = metaLen;

    // Empty Main CBOR (right after the Meta). 0xA0 is a DEFINITE-length empty map —
    // NOT 0xBF 0xFF (indefinite), which the app rejects.
    outBuf[p + mainOff] = 0xA0;

    // Empty Aux CBOR (block-aligned at auxAbsStart), likewise definite.
    outBuf[auxAbsStart] = 0xA0;

    // TLV terminator
    outBuf[terminatorPos] = 0xFE;

    if (outMeta) {
        outMeta->main_region_offset = (uint16_t)mainOff;
        outMeta->main_region_size   = 0;
        outMeta->aux_region_offset  = (uint16_t)auxOffset;
        outMeta->aux_region_size    = (uint16_t)AUX_REGION_SIZE;
    }

    return payloadStart;  // byte offset of OPT CBOR payload within outBuf
}
