NormSohl/openprinttag-weigh-station/src/nfc_task.cpp

// SPDX-License-Identifier: GPL-3.0-or-later
// Copyright (C) 2026 Norm Sohl

#include <Arduino.h>
#include <PN5180.h>
#include <PN5180ISO15693.h>
#include <string.h>
#include "config.h"
#include "spi_bus.h"
#include "device_state.h"
#include "opt_tag.h"
#include "controller.h"   // idle-return is now a ReturnToIdle event to the controller

// ── Shared globals (defined in main.cpp) ─────────────────────────────────────
extern volatile DeviceState gState;
extern SemaphoreHandle_t    gStateMutex;
extern volatile float       gWeightGrams;
extern SemaphoreHandle_t    gWeightMutex;
extern uint8_t              gTagUid[8];
extern OptMeta              gTagMeta;
extern OptMain              gTagMain;
extern OptAuxiliary         gTagAux;
extern SemaphoreHandle_t    gTagMutex;
extern volatile bool        gWriteMainPending;
extern volatile bool        gWriteAuxPending;
extern SemaphoreHandle_t    gSpiMutex;
// Set by the TAGFORMAT serial command: force a reformat of whatever tag is
// present, regardless of how it currently classifies. The escape hatch for a
// tag left half-written by a failed format.
extern volatile bool        gTagForceFormat;
// Set by the web /erase page's Start/Stop buttons: while true, ANY freshly
// placed tag is erased immediately, no countdown -- see the classification
// check below and sync_task.cpp's Resolving phase.
extern volatile bool        gEraseModeActive;
extern volatile uint32_t    gEraseModeActivityMs;

// Raw ISO15693 block dump for the spool currently on the scale.
// An ICODE SLIX2 reports 80 blocks x 4 B = 320 B; 512 leaves headroom for
// larger ISO15693 parts. Geometry is validated against this size on detection.
static uint8_t sRawBuf[512];
static size_t  sRawLen        = 0;
static size_t  sPayloadOffset = SIZE_MAX;  // byte offset of NDEF payload in sRawBuf
static size_t  sPayloadLen    = 0;         // ...and how many bytes of it are formatted

// ── Helpers ───────────────────────────────────────────────────────────────────
// nfcTask no longer WRITES gState (phase 4): it drives its own NfcPhase and posts
// events to the controller, the single writer. It still reads gState — the
// Boot/WiFiSetupMode no-poll gate, and the ReconcilingMainSection check.

static DeviceState getState() {
    xSemaphoreTake(gStateMutex, portMAX_DELAY);
    DeviceState s = gState;
    xSemaphoreGive(gStateMutex);
    return s;
}

// Dump the raw ISO15693 block bytes of the tag last read, as hex with byte
// offsets — for interop debugging. The decoded view (DUMP TAG) can look fine
// while the CC / NDEF-TLV / CBOR FRAMING differs in a way a strict reader (a
// phone) rejects. Block 0 is the Capability Container: E1 magic, byte 2 = MLEN
// (data area in bytes/8). sRawBuf is stable while a tag sits on the scale
// (re-read only happens on a fresh placement), so reading it from the serial
// task is safe enough for a debug dump. Called by "DUMP RAW".
void nfcDumpRaw() {
    if (sRawLen == 0) {
        Serial.println("[raw] nothing read yet — place a tag first");
        return;
    }
    Serial.printf("[raw] %u bytes; payload@%u len %u\n", (unsigned)sRawLen,
                  (unsigned)sPayloadOffset, (unsigned)sPayloadLen);
    for (size_t i = 0; i < sRawLen; i += 16) {
        Serial.printf("[raw] %04x:", (unsigned)i);
        for (size_t j = 0; j < 16 && i + j < sRawLen; j++)
            Serial.printf(" %02x", sRawBuf[i + j]);
        Serial.println();
    }
}

// Phase 3 of the state-machine refactor (docs/design/state-machine-ownership.md):
// nfcTask drives its own tag lifecycle off this LOCAL phase instead of reading
// gState, and reports facts to the controller (ctrlPost), which is the single
// writer of the detection states. Mapping to gState:
//   Waiting        = Idle / IdleNoWiFi        (owned by the controller)
//   Debouncing     = TagDetecting
//   BlankDetected  = BlankTagFound            (one tick, then AwaitingFormatConfirm)
//   AwaitingConfirm= AwaitingFormatConfirm
//   Formatting     = FormattingAndRegistering
//   Held           = ValidTagFound + the syncTask-owned weigh states; nfcTask here
//                    only services Aux/Main write-backs and watches for removal
//   ErrorHeld      = TagReadError
enum class NfcPhase { Waiting, Debouncing, BlankDetected, AwaitingConfirm,
                      Formatting, Held, ErrorHeld };

// Human-readable ISO15693 status. The distinction matters for diagnosis:
//   NO_CARD              -> the tag never answered. RF energy, not logic. A write
//                           needs far more field strength than a read, so a tag
//                           that inventories fine can still fail to program.
//   BLOCK_NOT_PROGRAMMED -> it answered but the cell didn't take. Also usually
//                           power, at the margin.
//   BLOCK_IS_LOCKED      -> the tag is write-protected. No amount of repositioning
//                           will help; the tag is not usable for OPT.
//   BLOCK_NOT_AVAILABLE  -> we addressed past the end of memory, i.e. our
//                           numBlocks is wrong.
//   OPTION_NOT_SUPPORTED -> the tag wants the Option flag set on writes, which
//                           this library does not do (it sends flags 0x22).
static const char* isoErrName(ISO15693ErrorCode rc) {
    switch (rc) {
        case EC_NO_CARD:                          return "NO_CARD (no answer — RF/coupling)";
        case ISO15693_EC_OK:                      return "OK";
        case ISO15693_EC_NOT_SUPPORTED:           return "NOT_SUPPORTED";
        case ISO15693_EC_NOT_RECOGNIZED:          return "NOT_RECOGNIZED";
        case ISO15693_EC_OPTION_NOT_SUPPORTED:    return "OPTION_NOT_SUPPORTED";
        case ISO15693_EC_UNKNOWN_ERROR:           return "UNKNOWN";
        case ISO15693_EC_BLOCK_NOT_AVAILABLE:     return "BLOCK_NOT_AVAILABLE (past end)";
        case ISO15693_EC_BLOCK_ALREADY_LOCKED:    return "BLOCK_ALREADY_LOCKED";
        case ISO15693_EC_BLOCK_IS_LOCKED:         return "BLOCK_IS_LOCKED (write-protected)";
        case ISO15693_EC_BLOCK_NOT_PROGRAMMED:    return "BLOCK_NOT_PROGRAMMED (write didn't take)";
        case ISO15693_EC_BLOCK_NOT_LOCKED:        return "BLOCK_NOT_LOCKED";
        case ISO15693_EC_CUSTOM_CMD_ERROR:        return "CUSTOM_CMD_ERROR";
    }
    return "?";
}

// Read every ISO15693 block into sRawBuf. Returns true on success.
// Verify signatures against installed ATrappmann/PN5180-Library version if compile errors occur.
static bool readAllBlocks(PN5180ISO15693& nfc, uint8_t* uid,
                          uint8_t numBlocks, uint8_t blockSize) {
    size_t total = (size_t)numBlocks * blockSize;
    if (total > sizeof(sRawBuf)) total = sizeof(sRawBuf);
    for (uint8_t b = 0; b < numBlocks && (size_t)b * blockSize < sizeof(sRawBuf); b++) {
        ISO15693ErrorCode rc = nfc.readSingleBlock(uid, b, sRawBuf + b * blockSize, blockSize);
        if (rc != ISO15693_EC_OK) {
            Serial.printf("[nfc] read FAILED at block %u of %u: rc=%d %s\n",
                          (unsigned)b, (unsigned)numBlocks, (int)rc, isoErrName(rc));
            return false;
        }
    }
    sRawLen = total;
    return true;
}

// Write one block, retrying a few times before giving up.
//
// EEPROM programming sits much closer to the RF power budget than a read does,
// so an occasional failure on an otherwise fine tag is normal and a retry
// usually takes. Retrying is standard practice for ISO15693 writes; failing a
// whole onboarding because one block out of eighty flickered is not.
//
// Takes and releases the bus itself, per attempt: each write costs ~10 ms inside
// the library, and holding gSpiMutex across a whole 80-block format would freeze
// displayTask for a second or more.
#define TAG_WRITE_RETRIES 3
static ISO15693ErrorCode writeBlockRetry(PN5180ISO15693& nfc, uint8_t* uid,
                                         uint8_t blockNo, uint8_t* data,
                                         uint8_t blockSize) {
    ISO15693ErrorCode rc = ISO15693_EC_UNKNOWN_ERROR;
    for (int attempt = 0; attempt < TAG_WRITE_RETRIES; attempt++) {
        spiBusTakeNfc();
        rc = nfc.writeSingleBlock(uid, blockNo, data, blockSize);
        spiBusGive();
        if (rc == ISO15693_EC_OK) {
            if (attempt) Serial.printf("[nfc] block %u wrote on attempt %d\n",
                                       (unsigned)blockNo, attempt + 1);
            return rc;
        }
        vTaskDelay(pdMS_TO_TICKS(20));   // let the field settle before retrying
    }
    return rc;
}

// Write a CBOR section (Main, or Aux when aux is true) back into the tag, at
// the region the tag's own Meta declares for it and never past its end.
static bool writeSection(PN5180ISO15693& nfc, uint8_t* uid,
                         uint8_t blockSize, const OptMeta& meta, bool aux,
                         const uint8_t* cborData, size_t cborLen) {
    if (sPayloadOffset == SIZE_MAX) return false;

    // Bound by the section's OWN region first, from the tag's Meta. Without it
    // a Main rewrite longer than the Main region runs on into the Aux region
    // and overwrites it: harmless on our own layout, which leaves Main room to
    // grow, but a vendor tag may pack its Main tight, and we now rewrite those
    // too. The payload check below stays as the backstop.
    const size_t payloadLen = (sPayloadLen > 0) ? sPayloadLen
                                                : sRawLen - sPayloadOffset;
    size_t regionStart = 0, regionEnd = 0;
    if (!optRegionBounds(meta, aux, payloadLen, &regionStart, &regionEnd)) {
        Serial.printf("[nfc] %s write REFUSED: the tag declares no %s region\n",
                      aux ? "Aux" : "Main", aux ? "Aux" : "Main");
        return false;
    }
    if (regionStart + cborLen > regionEnd) {
        Serial.printf("[nfc] %s write REFUSED: %u bytes do not fit the tag's "
                      "%u-byte %s region\n", aux ? "Aux" : "Main",
                      (unsigned)cborLen, (unsigned)(regionEnd - regionStart),
                      aux ? "Aux" : "Main");
        return false;
    }
    size_t absStart = sPayloadOffset + regionStart;

    // Bound by what is FORMATTED, not by how big the tag is.
    //
    // sRawLen is the physical size getSystemInfo reports — 320 B for an 80x4
    // SLIX2. The formatted layout can be shorter: the block-79 workaround
    // reformats at 79 blocks, so the NDEF payload ends at 314 while the tag runs
    // to 320. Checking only against sRawLen let a write start inside the layout
    // and finish outside it, in the very block that refuses writes. Block 78
    // took its half, block 79 rejected the rest, and the tag was left carrying a
    // CBOR map that opens and never closes — the reboot loop of 2026-08-08.
    //
    // The new Aux layout keeps writes clear of the final block, so this is now a
    // backstop rather than the primary defence. It still matters for a tag
    // formatted by an older build, or by anyone else: refusing cleanly leaves
    // the tag readable, whereas a partial write destroys it.
    const size_t formattedEnd = (sPayloadLen > 0)
                              ? sPayloadOffset + sPayloadLen
                              : sRawLen;          // extent unknown: fall back
    if (absStart + cborLen > formattedEnd) {
        Serial.printf("[nfc] section write REFUSED: %u..%u would run past the "
                      "formatted payload (ends %u) — writing anyway would leave "
                      "a half-written section\n",
                      (unsigned)absStart, (unsigned)(absStart + cborLen),
                      (unsigned)formattedEnd);
        return false;
    }
    if (absStart + cborLen > sRawLen) return false;   // never past the buffer

    memcpy(sRawBuf + absStart, cborData, cborLen);

    size_t firstBlock = absStart / blockSize;
    size_t lastBlock  = (absStart + cborLen - 1) / blockSize;
    for (size_t b = firstBlock; b <= lastBlock; b++) {
        ISO15693ErrorCode rc = writeBlockRetry(nfc, uid, (uint8_t)b,
                                               sRawBuf + b * blockSize, blockSize);
        if (rc != ISO15693_EC_OK) {
            Serial.printf("[nfc] section write FAILED at block %u/%u: rc=%d %s\n",
                          (unsigned)b, (unsigned)lastBlock, (int)rc, isoErrName(rc));
            return false;
        }
    }
    return true;
}

// ── Task ──────────────────────────────────────────────────────────────────────

// Read the PN5180's version registers over SPI and report them. This separates
// the two very different failure modes behind "no tag detected":
//   - versions read back plausibly -> SPI/CS/BUSY/RST wiring and 3.3 V logic are
//     fine, so a dead reader means RF: the TVDD/5 V transmitter rail, the
//     antenna, or the tag itself.
//   - all 0x00 or all 0xFF       -> the chip isn't talking at all; look at the
//     SPI bus, chip select, reset, or power before suspecting anything else.
// Returns true if the chip answered.
static bool nfcSelfTest(PN5180ISO15693& nfc) {
    uint8_t prod[2] = {0xFF, 0xFF}, fw[2] = {0xFF, 0xFF}, eep[2] = {0xFF, 0xFF};

    spiBusTakeNfc();
    nfc.readEEprom(PRODUCT_VERSION,  prod, 2);
    nfc.readEEprom(FIRMWARE_VERSION, fw,   2);
    nfc.readEEprom(EEPROM_VERSION,   eep,  2);
    spiBusGive();

    Serial.printf("[nfc] PN5180 product %d.%d  firmware %d.%d  eeprom %d.%d\n",
                  prod[1], prod[0], fw[1], fw[0], eep[1], eep[0]);

    const bool dead = (prod[0] == 0xFF && prod[1] == 0xFF) ||
                      (prod[0] == 0x00 && prod[1] == 0x00);
    if (dead) {
        Serial.println("[nfc] NOT RESPONDING — chip is not answering over SPI.");
        Serial.printf("[nfc]   check: NSS=%d BUSY=%d RST=%d, shared SPI "
                      "SCK=%d MOSI=%d MISO=%d, and 3.3 V power\n",
                      PN5180_NSS, PN5180_BUSY, PN5180_RESET,
                      SPI_SCK, SPI_MOSI, SPI_MISO);
    } else {
        Serial.println("[nfc] responding — SPI wiring OK. If tags still aren't "
                       "seen, suspect the RF rail/antenna, not the bus.");
    }
    return !dead;
}

void nfcTask(void* param) {
    PN5180ISO15693 nfc(PN5180_NSS, PN5180_BUSY, PN5180_RESET);

    // Every step here is announced BEFORE it runs, because the PN5180 library
    // waits on the chip with unbounded loops — reset() spins on
    // `while (0 == (IDLE_IRQ_STAT & getIRQStatus()))` and the SPI helpers spin
    // on BUSY. If the chip is absent, unpowered or mis-wired, the task simply
    // never returns and prints nothing at all. Whatever line appears last is
    // the call that hung.
    Serial.printf("[nfc] init: NSS=%d BUSY=%d RST=%d (shared SPI %d/%d/%d)\n",
                  PN5180_NSS, PN5180_BUSY, PN5180_RESET,
                  SPI_SCK, SPI_MOSI, SPI_MISO);

    // Raw pin read before the library touches anything. The PN5180 idles BUSY
    // LOW; a pin stuck HIGH (or floating) with no chip on the other end is the
    // cheapest possible evidence that it isn't powered or wired.
    pinMode(PN5180_BUSY, INPUT);
    Serial.printf("[nfc] BUSY reads %s before init\n",
                  digitalRead(PN5180_BUSY) ? "HIGH (suspect: unpowered/miswired)"
                                           : "LOW (normal idle)");

    // These three MUST hold the bus. displayBegin() has already run and left
    // GPIO 11/12 routed to the display's peripheral (SPI3); spiBusTakeNfc()
    // points them back at the PN5180's (SPI2). Without it the reader never
    // sees a clock edge and reset() waits on a chip that cannot answer. See
    // spi_bus.h.
    //
    // That wait used to be UNBOUNDED — a reader that never answered held the bus
    // and stalled displayTask with it. The vendored PN5180-Library now bounds
    // every spin-wait (PN5180_BUSY_TIMEOUT_MS), so a dead or hung reader times
    // out and releases the bus instead of freezing the display. A dead reader is
    // still worth seeing, so the boot log names each call as it runs.
    Serial.println("[nfc] begin()…");
    spiBusTakeNfc();
    nfc.begin();
    spiBusGive();
    Serial.println("[nfc] begin() ok");

    Serial.println("[nfc] reset()… (bounded — times out if the chip never answers)");
    spiBusTakeNfc();
    nfc.reset();
    spiBusGive();
    Serial.println("[nfc] reset() ok");

    nfcSelfTest(nfc);   // logs whether the chip is alive before we poll for tags

    Serial.println("[nfc] setupRF()…");
    spiBusTakeNfc();
    nfc.setupRF();
    spiBusGive();
    Serial.println("[nfc] setupRF() ok — polling for tags");

    uint8_t uid[8]       = {};
    uint8_t numBlocks    = 0;
    uint8_t blockSize    = 0;
    uint8_t debounceHits = 0;
    uint8_t missCount    = 0;
    TickType_t confirmStart = 0;
    NfcPhase phase       = NfcPhase::Waiting;

    for (;;) {
        DeviceState state = getState();

        // Don't touch the reader while WiFi is still being set up. There is no
        // tag to act on during Boot or the captive portal, and polling the
        // PN5180 continuously while the SoftAP radio is transmitting has hung the
        // reader mid-transaction with the SPI bus HELD — which starves
        // displayTask (the "[spi] tft has waited 5 s" storm) and freezes the very
        // "WiFi Setup" screen someone is standing there trying to read. syncTask
        // owns these states; leave the bus alone until a tag can actually matter.
        if (state == DeviceState::Boot || state == DeviceState::WiFiSetupMode) {
            phase = NfcPhase::Waiting;
            vTaskDelay(pdMS_TO_TICKS(200));
            continue;
        }

        // ── Poll for tag presence ─────────────────────────────────────────────
        uint8_t  detectedUid[8] = {};
        uint8_t  detectedNumBlocks, detectedBlockSize;
        spiBusTakeNfc();
        bool tagPresent = (nfc.getInventory(detectedUid) == ISO15693_EC_OK);
        if (tagPresent) {
            // Argument order is (uid, blockSize, numBlocks) — blockSize SECOND.
            // These were swapped, which read an 80-block x 4-byte tag as 4
            // blocks of 80 bytes. Total size came out right (320 B), so nothing
            // looked wrong; but every write then asked the tag to store 80 bytes
            // in a 4-byte block, which is a malformed command it simply ignores.
            // That is the "NO_CARD" every write was returning.
            tagPresent = (nfc.getSystemInfo(detectedUid, &detectedBlockSize, &detectedNumBlocks)
                          == ISO15693_EC_OK);
            // Per ISO15693 blockSize is 1..32 and numBlocks 1..256. Anything
            // outside that, or more memory than we can buffer, means we have
            // misread the geometry — refuse rather than issue writes against it.
            if (tagPresent) {
                const size_t bytes = (size_t)detectedNumBlocks * detectedBlockSize;
                if (detectedBlockSize == 0 || detectedBlockSize > 32 ||
                    detectedNumBlocks == 0 || bytes > sizeof(sRawBuf)) {
                    Serial.printf("[nfc] implausible tag geometry: %u blocks x %u B "
                                  "= %u B (buffer %u B) — ignoring this tag\n",
                                  (unsigned)detectedNumBlocks, (unsigned)detectedBlockSize,
                                  (unsigned)bytes, (unsigned)sizeof(sRawBuf));
                    tagPresent = false;
                }
            }
        }
        spiBusGive();

        // ── Waiting for a tag (controller shows Idle / IdleNoWiFi) ────────────
        if (phase == NfcPhase::Waiting) {
            // Erase mode's idle auto-off: checked here, not just on
            // placement, because the risk is a station left armed with
            // NOTHING on the scale at all -- someone walked away, not
            // merely "no tag between placements." See gEraseModeActivityMs's
            // declaration in main.cpp for why this isn't tab-visibility-based.
            if (gEraseModeActive &&
                (millis() - gEraseModeActivityMs) > (ERASE_MODE_IDLE_TIMEOUT_SEC * 1000UL)) {
                gEraseModeActive = false;
                Serial.println("[erase] auto-off: idle timeout with no tag processed");
            }
            if (tagPresent) {
                memcpy(uid, detectedUid, 8);
                numBlocks    = detectedNumBlocks;
                blockSize    = detectedBlockSize;
                debounceHits = 1;
                phase = NfcPhase::Debouncing;
                ctrlPost(CtrlEvent::TagDetecting);
            }
            vTaskDelay(pdMS_TO_TICKS(100));
            continue;
        }

        // ── Debounce (controller shows TagDetecting) ──────────────────────────
        if (phase == NfcPhase::Debouncing) {
            if (!tagPresent || memcmp(detectedUid, uid, 8) != 0) {
                ctrlPost(CtrlEvent::ReturnToIdle);  // false trigger or UID changed
                phase = NfcPhase::Waiting;
                debounceHits = 0;
                vTaskDelay(pdMS_TO_TICKS(100));
                continue;
            }
            if (++debounceHits < NFC_DEBOUNCE_READS) {
                vTaskDelay(pdMS_TO_TICKS(50));
                continue;
            }

            // Tag confirmed — read all blocks and classify
            spiBusTakeNfc();
            bool readOk = readAllBlocks(nfc, uid, numBlocks, blockSize);
            spiBusGive();
            if (!readOk) {
                Serial.printf("[nfc] could not read the tag (%u blocks x %u B). "
                              "RF/coupling, or the tag moved mid-read.\n",
                              (unsigned)numBlocks, (unsigned)blockSize);
                ctrlPost(CtrlEvent::TagReadErr);
                phase = NfcPhase::ErrorHeld;
                vTaskDelay(pdMS_TO_TICKS(100));
                continue;
            }

            // Forced reformat wins over classification: the whole point is to
            // recover a tag whose current contents we cannot make sense of.
            if (gTagForceFormat) {
                gTagForceFormat = false;
                Serial.println("[nfc] TAGFORMAT: forcing a reformat of this tag");
                ctrlPost(CtrlEvent::FormatConfirmed);
                phase = NfcPhase::Formatting;
                vTaskDelay(pdMS_TO_TICKS(10));
                continue;
            }

            // Erase mode (armed from the web /erase page): wins over
            // classification the same way a forced TAGFORMAT does, and for
            // the same reason -- launch immediately, no countdown. A
            // genuine blank tag gets the confirm-by-inaction window because
            // someone might not be watching when it lands; erase mode is the
            // opposite case, staff already sorted a bin of decided-empty
            // spools and are standing there feeding them through one at a
            // time, so the wait is pure friction. See sync_task.cpp's
            // Resolving phase for what happens once it's actually erased
            // (retire the old record, mint nothing new).
            if (gEraseModeActive) {
                Serial.println("[nfc] erase mode: erasing this tag now");
                ctrlPost(CtrlEvent::FormatConfirmed);
                phase = NfcPhase::Formatting;
                vTaskDelay(pdMS_TO_TICKS(10));
                continue;
            }

            if (optIsBlank(sRawBuf, sRawLen)) {
                ctrlPost(CtrlEvent::TagBlank);
                phase = NfcPhase::BlankDetected;
            } else {
                OptMeta  meta = {};
                OptMain  main = {};
                OptAuxiliary aux = {};
                if (!optDecode(sRawBuf, sRawLen, &meta, &main, &aux)) {
                    // Read cleanly but makes no sense. The likeliest cause by far
                    // is a tag left half-written by a format that failed partway:
                    // block 0 carries the 0xE1 NDEF magic and a Meta section, so
                    // optIsBlank() no longer calls it blank, but Main/Aux were
                    // never written — and there is no automatic way out of that.
                    //
                    // Deliberately NOT auto-reformatted. A tag we merely fail to
                    // parse might be a legitimate foreign format, and wiping it
                    // would be irreversible. Recovery is the explicit TAGFORMAT
                    // serial command.
                    Serial.printf("[nfc] tag read OK (%u B) but does not decode as OPT.\n",
                                  (unsigned)sRawLen);
                    Serial.print("[nfc]   first bytes:");
                    for (size_t i = 0; i < 24 && i < sRawLen; i++)
                        Serial.printf(" %02x", sRawBuf[i]);
                    Serial.println();
                    Serial.printf("[nfc]   %s\n",
                                  (sRawLen && sRawBuf[0] == 0xE1)
                                      ? "starts 0xE1 — NDEF-formatted, so probably a "
                                        "PARTIAL format. Send TAGFORMAT to rewrite it."
                                      : "no NDEF magic — foreign or corrupt content.");
                    ctrlPost(CtrlEvent::TagReadErr);
                    phase = NfcPhase::ErrorHeld;
                } else {
                    if (!optPayloadExtent(sRawBuf, sRawLen, &sPayloadOffset, &sPayloadLen)) {
                        sPayloadOffset = SIZE_MAX;
                        sPayloadLen    = 0;
                    }
                    xSemaphoreTake(gTagMutex, portMAX_DELAY);
                    memcpy(gTagUid, uid, 8);
                    gTagMeta = meta;
                    gTagMain = main;
                    gTagAux  = aux;
                    xSemaphoreGive(gTagMutex);
                    // syncTask resolves instance_uuid against the local store and
                    // transitions to WeighingAndSync (known) or ForeignTagFound (new)
                    ctrlPost(CtrlEvent::TagValid);
                    phase = NfcPhase::Held;
                }
            }
            vTaskDelay(pdMS_TO_TICKS(100));
            continue;
        }

        // ── Blank tag: BlankTagFound for one tick, then the countdown ─────────
        if (phase == NfcPhase::BlankDetected) {
            confirmStart = xTaskGetTickCount();
            ctrlPost(CtrlEvent::AwaitConfirm);
            phase = NfcPhase::AwaitingConfirm;
            continue;
        }

        // ── Countdown (controller shows AwaitingFormatConfirm) ────────────────
        if (phase == NfcPhase::AwaitingConfirm) {
            if (!tagPresent) {
                ctrlPost(CtrlEvent::ReturnToIdle);  // removed during countdown — cancelled
                phase = NfcPhase::Waiting;
                vTaskDelay(pdMS_TO_TICKS(100));
                continue;
            }
            if (xTaskGetTickCount() - confirmStart >= pdMS_TO_TICKS(BLANK_TAG_CONFIRM_SEC * 1000UL)) {
                ctrlPost(CtrlEvent::FormatConfirmed);
                phase = NfcPhase::Formatting;
            }
            vTaskDelay(pdMS_TO_TICKS(100));
            continue;
        }

        // ── Formatting (controller shows FormattingAndRegistering) ────────────
        if (phase == NfcPhase::Formatting) {
            uint8_t  initBuf[512] = {};
            OptMeta  initMeta     = {};

            // Both failures below land in TagReadError, which on screen reads
            // only "Read Error" — so say on the wire which one it was and why.
            // Without this the two are indistinguishable, and they have nothing
            // in common: one is our layout maths, the other is RF.
            Serial.printf("[nfc] formatting blank tag: %u blocks x %u B = %u B\n",
                          (unsigned)numBlocks, (unsigned)blockSize,
                          (unsigned)numBlocks * blockSize);

            // Some tags refuse a write to their FINAL block while accepting every
            // other one and reading that block back fine. Observed on the ICODE
            // SLIX2 tags in use here: blocks 0..78 program, block 79 returns 0x0F
            // on all three attempts, every time. Root cause unconfirmed — 0x0F is
            // ISO15693's generic error and NXP does not document the last block as
            // special — so rather than hardcode a rule from one part, adapt: if the
            // ONLY block that failed is the last one, rebuild the layout one block
            // shorter and try again.
            //
            // Costs one block (4 bytes) on tags that need it, nothing on tags that
            // do not, and keeps working if a future tag has a different quirk.
            // Once a tag has refused its final block, assume the rest of the
            // batch will too. Without this every tag pays for the discovery
            // twice — ~4.5 s writing 80 blocks, failing, then ~4.1 s writing 79
            // — and a 8.6 s "Registering..." screen is long enough that someone
            // lifts the spool early and leaves the tag half-written.
            //
            // Per boot, not persisted: a different tag type in the drawer should
            // get its full memory, and a power cycle re-tests.
            static bool sLastBlockRefused = false;
            uint8_t  usable    = (sLastBlockRefused && numBlocks > 2)
                                     ? (uint8_t)(numBlocks - 1) : numBlocks;
            size_t   payloadOff = SIZE_MAX;
            bool     writeOk   = false;

            for (int pass = 0; pass < 2 && !writeOk; pass++) {
                payloadOff = optBuildBlankTag(usable, blockSize,
                                              initBuf, sizeof(initBuf), &initMeta);
                if (payloadOff == SIZE_MAX) {
                    Serial.printf("[nfc] optBuildBlankTag REFUSED this geometry "
                                  "(%u blocks x %u B, buffer %u B). Nothing was "
                                  "written to the tag.\n",
                                  (unsigned)usable, (unsigned)blockSize,
                                  (unsigned)sizeof(initBuf));
                    break;
                }

                const uint32_t t0 = millis();
                uint8_t           failedAt = 0;
                ISO15693ErrorCode failRc   = ISO15693_EC_OK;
                writeOk = true;
                for (uint8_t b = 0; b < usable; b++) {
                    ISO15693ErrorCode rc = writeBlockRetry(nfc, uid, b,
                                                           initBuf + b * blockSize, blockSize);
                    if (rc != ISO15693_EC_OK) {
                        writeOk = false; failedAt = b; failRc = rc;
                        break;
                    }
                }

                if (writeOk) {
                    Serial.printf("[nfc] format ok: %u blocks in %u ms%s\n",
                                  (unsigned)usable, (unsigned)(millis() - t0),
                                  usable == numBlocks
                                      ? ""
                                      : (sLastBlockRefused
                                             ? " (last block reserved — known for this session)"
                                             : " (last block reserved)"));
                    break;
                }

                // Only the final block refused, and we have room to give one up.
                if (pass == 0 && failedAt == (uint8_t)(usable - 1) && usable > 2) {
                    sLastBlockRefused = true;
                    Serial.printf("[nfc] only the final block (%u) refused: rc=%d %s — "
                                  "retrying with %u blocks\n",
                                  (unsigned)failedAt, (int)failRc, isoErrName(failRc),
                                  (unsigned)(usable - 1));
                    usable--;
                    continue;
                }

                Serial.printf("[nfc] format FAILED at block %u of %u after %d "
                              "attempts: rc=%d %s\n",
                              (unsigned)failedAt, (unsigned)usable, TAG_WRITE_RETRIES,
                              (int)failRc, isoErrName(failRc));
                if (failedAt == 0)
                    Serial.println("[nfc]   nothing was written — tag is untouched.");
                else
                    Serial.printf("[nfc]   blocks 0..%u were written — the tag is "
                                  "PARTIALLY formatted and needs another pass.\n",
                                  (unsigned)(failedAt - 1));
                break;
            }

            if (!writeOk) {
                ctrlPost(CtrlEvent::TagReadErr);
                phase = NfcPhase::ErrorHeld;
                vTaskDelay(pdMS_TO_TICKS(100));
                continue;
            }

            // Mirror the written bytes into the task-local raw buffer so subsequent
            // aux/main writes via writeSection() use the correct offsets.
            // `usable`, not numBlocks: if the final block was reserved, the
            // layout and every subsequent writeSection() offset are based on the
            // shorter tag, and sRawLen is what bounds those writes.
            memcpy(sRawBuf, initBuf, (size_t)usable * blockSize);
            sRawLen        = (size_t)usable * blockSize;
            if (!optPayloadExtent(sRawBuf, sRawLen, &sPayloadOffset, &sPayloadLen)) {
                sPayloadOffset = payloadOff;   // fall back; the layout is ours
                sPayloadLen    = 0;
            }

            xSemaphoreTake(gTagMutex, portMAX_DELAY);
            memcpy(gTagUid, uid, 8);
            gTagMeta = initMeta;
            gTagMain = {};   // nil UUID — syncTask creates a stub Spool with needs_onboarding=true
            gTagAux  = {};
            xSemaphoreGive(gTagMutex);

            // syncTask sees the nil UUID, mints a local stub record, and
            // transitions on once the record exists.
            ctrlPost(CtrlEvent::TagValid);
            phase = NfcPhase::Held;
            vTaskDelay(pdMS_TO_TICKS(100));
            continue;
        }

        // ── Tag read error: wait for removal (controller shows TagReadError) ──
        if (phase == NfcPhase::ErrorHeld) {
            if (!tagPresent) { ctrlPost(CtrlEvent::ReturnToIdle); phase = NfcPhase::Waiting; }
            vTaskDelay(pdMS_TO_TICKS(200));
            continue;
        }

        // ── Held: a classified tag is on the scale ────────────────────────────
        // syncTask owns the weigh states it shows (ValidTagFound ->
        // ForeignTagFound / RegisteringForeignTag / WeighingAndSync / Present /
        // ReconcilingMainSection); nfcTask only services the Aux/Main write-backs
        // below and watches for removal. This single removal check replaces the
        // four gState-keyed ones the loop used to carry. Every other phase has
        // continued above, so reaching here means Held — but guard defensively so
        // an unexpected phase can never fall into the weigh tail. (That fall-
        // through was the Phase-2 bug: an unguarded !tagPresent branch drove
        // Boot/WiFiSetupMode to idle ~2x/sec. Those are now gated at the loop top.)
        if (phase != NfcPhase::Held) {
            vTaskDelay(pdMS_TO_TICKS(100));
            continue;
        }

        if (!tagPresent) {
            if (++missCount >= 2) {
                missCount = 0;
                sRawLen = 0;
                sPayloadOffset = SIZE_MAX;
                sPayloadLen    = 0;
                ctrlPost(CtrlEvent::ReturnToIdle);
                phase = NfcPhase::Waiting;
            }
            vTaskDelay(pdMS_TO_TICKS(200));
            continue;
        }
        missCount = 0;

        // TAGFORMAT can be armed while this exact tag is already sitting
        // Held. Erase mode does NOT need the same catch here: it only ever
        // takes effect on a fresh placement (the classification check
        // above), by design — see gEraseModeActive's declaration.
        if (gTagForceFormat) {
            gTagForceFormat = false;
            Serial.println("[nfc] TAGFORMAT: forcing a reformat of the tag already on the scale");
            ctrlPost(CtrlEvent::FormatConfirmed);
            phase = NfcPhase::Formatting;
            vTaskDelay(pdMS_TO_TICKS(10));
            continue;
        }

        // Write Aux when syncTask has updated gTagAux (after weighing)
        if (gWriteAuxPending) {
            gWriteAuxPending = false;
            uint8_t cborBuf[64];
            xSemaphoreTake(gTagMutex, portMAX_DELAY);
            OptAuxiliary aux = gTagAux;
            OptMeta  meta      = gTagMeta;
            uint16_t auxOffset = meta.aux_region_offset;
            xSemaphoreGive(gTagMutex);
            if (auxOffset > 0 && !optAuxPreservesAll(aux)) {
                // Same rule as Main: refusing costs an edit (consumed_weight/
                // purchase_price won't update this pass), writing would cost
                // whatever unmodelled Aux key this tag already carried.
                Serial.println("[nfc] Aux NOT rewritten: this tag carries more "
                               "unmodelled fields than the aux region can hold");
            } else if (auxOffset > 0) {
                size_t n = optEncodeAux(aux, cborBuf, sizeof(cborBuf));
                if (n > 0) {
                    // No spiBusTake here: writeSection -> writeBlockRetry takes and
                    // releases the bus per block. gSpiMutex is not recursive, so
                    // holding it across this call deadlocks the task against
                    // itself and freezes displayTask with it.
                    writeSection(nfc, uid, blockSize, meta, true, cborBuf, n);
                }
            }
        }

        if (gWriteMainPending) {
            gWriteMainPending = false;
            // 320, not 256: a re-encode now carries up to 192 bytes of
            // passed-through vendor fields on top of our own ~113. The real
            // limit is still the Main region (234 B at most), which
            // writeSection() enforces — this only has to be big enough that
            // encoding never fails for content a tag could actually hold.
            uint8_t cborBuf[320];
            xSemaphoreTake(gTagMutex, portMAX_DELAY);
            OptMain  main      = gTagMain;
            OptMeta  meta      = gTagMeta;
            xSemaphoreGive(gTagMutex);
            // Not every tag is ours to rewrite. OPT key 13 marks a tag as write
            // protected — irreversibly, or behind a PROTECT PAGE password — and
            // a genuine vendor spool may well arrive that way. Without this the
            // reconcile loop would retry Main on every placement and log
            // "section write FAILED" forever against hardware that is correctly
            // refusing us.
            //
            // Aux is untouched by this on purpose: OPT requires the aux section
            // to stay writable, so consumed_weight still records and the spool
            // still weighs normally. Only the vendor's identity data is off
            // limits.
            if (!optMainWritable(main)) {
                Serial.printf("[nfc] Main is write-protected (key 13 = %d) — "
                              "leaving it alone; weighing and Aux still work\n",
                              (int)main.write_protection);
            } else if (!optMainPreservesAll(main)) {
                // Rather than write a Main that quietly drops fields the vendor
                // put there. Refusing costs an edit; writing costs their data.
                Serial.println("[nfc] Main NOT rewritten: this tag carries more "
                               "unmodelled fields than we can hold, and the "
                               "rewrite would discard them");
            } else {
                size_t n = optEncodeMain(main, cborBuf, sizeof(cborBuf));
                if (n > 0) {
                    // No spiBusTake here: writeSection -> writeBlockRetry takes
                    // and releases the bus per block. gSpiMutex is not
                    // recursive, so holding it across this call deadlocks the
                    // task against itself and freezes displayTask with it.
                    writeSection(nfc, uid, blockSize, meta, false, cborBuf, n);
                }
            }
            // Either way we are done reconciling this tag: a protected one will
            // never match, so staying in ReconcilingMainSection would pin the
            // display on "Updating tag..." for as long as the spool sat there.
            if (getState() == DeviceState::ReconcilingMainSection)
                ctrlPost(CtrlEvent::ReconcileDone);
        }

        vTaskDelay(pdMS_TO_TICKS(200));
    }
}
