NormSohl/openprinttag-weigh-station/src/sync_task.cpp

// SPDX-License-Identifier: GPL-3.0-or-later
// Copyright (C) 2026 Norm Sohl

#include <Arduino.h>
#include <WiFi.h>
#include <WiFiManager.h>
#include <esp_random.h>
#include <string.h>
#include <time.h>
#include "config.h"
#include "display_tz.h"
#include "device_state.h"
#include "opt_tag.h"
#include "store.h"
#include "web_app.h"
#include "controller.h"   // WiFi/idle state is now owned by controllerTask

// ── Shared globals ────────────────────────────────────────────────────────────
extern volatile DeviceState gState;
extern SemaphoreHandle_t    gStateMutex;
extern volatile float       gWeightGrams;
extern SemaphoreHandle_t    gWeightMutex;
extern uint8_t              gTagUid[8];
extern OptMain              gTagMain;
extern OptAuxiliary         gTagAux;
extern SemaphoreHandle_t    gTagMutex;
extern volatile bool        gWriteMainPending;
extern volatile bool        gWriteAuxPending;
extern volatile bool        gEraseModeActive;
extern volatile uint32_t    gEraseModeActivityMs;
extern volatile int         gSpoolId;
extern volatile bool        gSpoolNeedsOnboarding;
extern char                 gWebAddr[48];
extern char                 gApSsid[24];
extern volatile int         gPortalSecsLeft;
extern volatile bool        gClockSet;

// ── State helpers ─────────────────────────────────────────────────────────────
// syncTask no longer WRITES gState (phase 4): it drives its own SyncPhase and
// posts events to the controller, the single writer. It still reads gState to
// detect entry into / exit from the weigh flow.

static DeviceState getState() {
    xSemaphoreTake(gStateMutex, portMAX_DELAY);
    DeviceState s = gState;
    xSemaphoreGive(gStateMutex);
    return s;
}

// ── UUID helpers ──────────────────────────────────────────────────────────────

static bool isNilUUID(const uint8_t* uuid) {
    for (int i = 0; i < 16; i++) if (uuid[i]) return false;
    return true;
}

static void generateUUIDv4(uint8_t* uuid) {
    esp_fill_random(uuid, 16);
    uuid[6] = (uuid[6] & 0x0F) | 0x40;  // version 4
    uuid[8] = (uuid[8] & 0x3F) | 0x80;  // variant 10xx
}

// 32 lowercase hex chars, no dashes — matches the store's uuid key format.
static void uuidToHex32(const uint8_t* uuid, char* out33) {
    for (int i = 0; i < 16; i++)
        snprintf(out33 + i * 2, 3, "%02x", uuid[i]);
}

// 16 lowercase hex chars — the physical NFC chip UID, matching store's nfc_uid.
static void uidToHex16(const uint8_t* uid, char* out17) {
    for (int i = 0; i < 8; i++)
        snprintf(out17 + i * 2, 3, "%02x", uid[i]);
}

// ── Tag ⇄ store field mapping ─────────────────────────────────────────────────

// "Unknown" is the store's placeholder for a record nobody has described yet
// (a blank tag's stub, a tag that arrived with no brand or material name). It
// is not a brand or a material, so it never goes onto a tag: the tag field is
// left empty, which optEncodeMain() omits. recordDiffersFromMain() uses the
// same mapping, or the placeholder and the empty field would differ forever
// and the reconcile loop would rewrite the tag on every poll.
static const char* tagText(const char* recordValue) {
    return strcmp(recordValue, "Unknown") == 0 ? "" : recordValue;
}

// Overlay the store record's identity fields onto an OptMain, preserving the
// tag-only fields (instance_uuid, material_class/type, actual weight, temps).
static void overlayRecordOntoMain(const SpoolRecord& r, OptMain& m) {
    // Clamped to OPT's max_length here, not only at encode, so gTagMain and
    // the snapshot hold exactly what lands on the tag and compare equal to it
    // when it is read back on the next placement.
    strlcpy(m.brand_name,            tagText(r.vendor),   sizeof(m.brand_name));
    strlcpy(m.material_name,         tagText(r.material), sizeof(m.material_name));
    strlcpy(m.material_abbreviation, r.abbr,     sizeof(m.material_abbreviation));
    optClampText(m.brand_name,            OPT_MAX_BRAND_NAME);
    optClampText(m.material_name,         OPT_MAX_MATERIAL_NAME);
    optClampText(m.material_abbreviation, OPT_MAX_MATERIAL_ABBREVIATION);
    memcpy(m.primary_color_rgba, r.rgba, 4);
    m.filament_diameter         = r.dia;
    m.empty_container_weight    = r.empty_g;
    m.nominal_netto_full_weight = r.nom_g;
    // A freshly weighed/full spool has no factory "actual" — seed it from the
    // nominal so remaining/used maths have a full-weight reference.
    if (r.nom_g > 0.0f && m.actual_netto_full_weight <= 0.0f)
        m.actual_netto_full_weight = r.nom_g;
}

// Would overlaying the record change this tag text? Same placeholder mapping
// and max_length clamp as overlayRecordOntoMain(), without building a whole
// OptMain (~500 B) on syncTask's stack to find out.
static bool textDiffers(const char* recordValue, const char* tagValue, size_t maxBytes) {
    const char*  want = tagText(recordValue);
    const size_t n    = optClampedLen(want, maxBytes);
    return strlen(tagValue) != n || strncmp(want, tagValue, n) != 0;
}

// True if the store record's identity differs from what's on the tag's Main.
// Only the fields the store tracks are compared (temps/class/type are tag-only).
static bool recordDiffersFromMain(const SpoolRecord& r, const OptMain& m) {
    return textDiffers(r.vendor,   m.brand_name,            OPT_MAX_BRAND_NAME)
        || textDiffers(r.material, m.material_name,         OPT_MAX_MATERIAL_NAME)
        || textDiffers(r.abbr,     m.material_abbreviation, OPT_MAX_MATERIAL_ABBREVIATION)
        || memcmp(r.rgba,     m.primary_color_rgba, 4) != 0
        || r.dia     != m.filament_diameter
        || r.empty_g != m.empty_container_weight
        || r.nom_g   != m.nominal_netto_full_weight;
}

// Same idea as the pair above, for the one Aux field the store tracks:
// what a spool cost. Currency is always "USD" here (see StoreEvent::cost),
// so it never needs to be part of the comparison.
static bool recordDiffersFromAux(const SpoolRecord& r, const OptAuxiliary& a) {
    return (r.cost > 0) != a.has_purchase
        || (r.cost > 0 && r.cost != a.purchase_price);
}

static void overlayRecordOntoAux(const SpoolRecord& r, OptAuxiliary& a) {
    a.has_purchase = (r.cost > 0);
    a.purchase_price = r.cost;
    if (a.has_purchase) strlcpy(a.purchase_currency, "USD", sizeof(a.purchase_currency));
}

// Build a product probe from a tag's Main section: everything the matching
// ladder can key on, in the order it tries them.
//
// The three UUIDs are stored as 32 hex chars to match the store's uuid format;
// a nil UUID on the tag means "absent" and must stay an EMPTY STRING rather
// than 32 zeroes, or every tag that carries no package_uuid would match every
// other one on rung 1.
static void productFromMain(const OptMain& m, ProductRecord& p) {
    if (!optUuidIsNil(m.package_uuid))  uuidToHex32(m.package_uuid,  p.pkg_uuid);
    if (!optUuidIsNil(m.material_uuid)) uuidToHex32(m.material_uuid, p.mat_uuid);
    if (!optUuidIsNil(m.brand_uuid))    uuidToHex32(m.brand_uuid,    p.brand_uuid);
    p.gtin = m.gtin;
    strlcpy(p.vendor,   m.brand_name[0]    ? m.brand_name    : "Unknown", sizeof(p.vendor));
    strlcpy(p.material, m.material_name[0] ? m.material_name : "Unknown", sizeof(p.material));
    strlcpy(p.abbr,     m.material_abbreviation, sizeof(p.abbr));
    memcpy(p.rgba, m.primary_color_rgba, 4);
    if (m.has_lab) { memcpy(p.lab, m.primary_color_lab, sizeof(p.lab)); p.has_lab = true; }
    p.dia     = m.filament_diameter;
    p.empty_g = m.empty_container_weight;
    p.nom_g   = m.nominal_netto_full_weight;
}

// Fill an Onboard/Reconcile event's identity fields from a tag's Main section.
static void identityFromMain(const OptMain& m, StoreEvent& e) {
    strlcpy(e.vendor,   m.brand_name[0]    ? m.brand_name    : "Unknown", sizeof(e.vendor));
    strlcpy(e.material, m.material_name[0] ? m.material_name : "Unknown", sizeof(e.material));
    strlcpy(e.abbr,     m.material_abbreviation, sizeof(e.abbr));
    memcpy(e.rgba, m.primary_color_rgba, 4);
    e.dia     = m.filament_diameter;
    e.empty_g = m.empty_container_weight;
    e.nom_g   = m.nominal_netto_full_weight;   // label weight; actual stays on the tag
}

// ── Captive portal ────────────────────────────────────────────────────────────

// Pump WiFiManager's non-blocking portal until the user finishes, or until one
// of two deadlines expires. Returns true if the device joined a network.
//
// Why two deadlines: the unit lives in a cabinet with the BOOT button out of
// reach, so the portal can never be allowed to stay open indefinitely — but it
// also must not cut someone off while they're typing a password.
//
//   idle     — restarted whenever a client is associated to the AP, so an
//              active setup session is never interrupted.
//   absolute — never restarted. Bounds the "joined, then walked away with the
//              phone still associated" case, which the idle timer alone would
//              keep alive forever.
//
// On expiry the caller falls back to the SoftAP, so the web app stays reachable
// either way — a timeout costs configurability, never availability.
// ── WiFi diagnostics ──────────────────────────────────────────────────────────
// BEACON_TIMEOUT fired ~9.4 s after EVERY association on the bench — with and
// without a spool, at uptimes 45 ms apart across separate boots, and again 9.5 s
// after each reconnect. That regularity rules out marginal signal, and
// setSleep(false) did not stop it, which rules out power save. What is left
// needs measuring rather than guessing: is the link weak, or is the station
// associating and then never hearing the AP at all?
//
// getSleep()'s return type changed between core 2.x (bool) and 3.x
// (wifi_ps_type_t), same split the buzzer's LEDC calls straddle.
static bool wifiIsSleeping() {
#if defined(ESP_ARDUINO_VERSION) && ESP_ARDUINO_VERSION >= ESP_ARDUINO_VERSION_VAL(3, 0, 0)
    return WiFi.getSleep() != WIFI_PS_NONE;
#else
    return WiFi.getSleep();
#endif
}

static void logWifiState(const char* what) {
    Serial.printf("[wifi] %s: rssi=%d dBm  ch=%d  bssid=%s  powersave=%s\n",
                  what, (int)WiFi.RSSI(), (int)WiFi.channel(),
                  WiFi.BSSIDstr().c_str(), wifiIsSleeping() ? "ON" : "off");
}

// The raw 802.11 reason code. 200 is BEACON_TIMEOUT; 3/4/15/205 point at the AP
// or the key exchange instead, and telling them apart decides whether this is
// ours to fix in firmware or a setting on the access point.
static void onWifiDisconnected(WiFiEvent_t, WiFiEventInfo_t info) {
    Serial.printf("[wifi] disconnect reason=%u  rssi=%d dBm\n",
                  (unsigned)info.wifi_sta_disconnected.reason, (int)WiFi.RSSI());
}

static bool runConfigPortal(WiFiManager& wm) {
    const uint32_t idleMs = (uint32_t)WIFI_PORTAL_TIMEOUT_SEC * 1000UL;
    const uint32_t maxMs  = (uint32_t)WIFI_PORTAL_MAX_SEC     * 1000UL;

    const uint32_t start = millis();
    uint32_t lastClient  = start;
    bool     sawClient   = false;

    for (;;) {
        wm.process();                       // serves the portal + captive DNS

        if (WiFi.status() == WL_CONNECTED) {
            Serial.println("[wifi] portal: credentials accepted, connected");
            return true;
        }

        const uint32_t now = millis();      // unsigned math: rollover-safe

        if (WiFi.softAPgetStationNum() > 0) {
            lastClient = now;               // someone is here; hold the idle timer
            if (!sawClient) {
                sawClient = true;
                Serial.println("[wifi] portal: client joined, idle timer suspended");
            }
        }

        if (now - lastClient >= idleMs) {
            Serial.printf("[wifi] portal: idle %u s with no client — giving up\n",
                          (unsigned)(idleMs / 1000));
            gPortalSecsLeft = -1;
            return false;
        }
        if (now - start >= maxMs) {
            Serial.printf("[wifi] portal: hit the %u s cap — giving up\n",
                          (unsigned)(maxMs / 1000));
            gPortalSecsLeft = -1;
            return false;
        }

        // Publish whichever deadline is actually governing, so the screen shows
        // the one that will fire: the idle timer until somebody associates,
        // then the absolute cap, which never restarts.
        const uint32_t leftMs = sawClient && WiFi.softAPgetStationNum() > 0
                                  ? (maxMs  - (now - start))
                                  : (idleMs - (now - lastClient));
        gPortalSecsLeft = (int)(leftMs / 1000);

        vTaskDelay(pdMS_TO_TICKS(50));
    }
}

// ── Task ──────────────────────────────────────────────────────────────────────

void syncTask(void* param) {
    // NOT WiFiSetupMode here. That screen says "Join network: WeighStation-Setup",
    // and setting it before autoConnect() made every ordinary boot flash that
    // instruction for the half-second the join took — naming an access point
    // that does not exist yet, on a device that is about to connect fine.
    //
    // It cost a field trip. Debugging a station that had come up in the lab, the
    // half-second flash read as "the setup screen appeared and vanished", which
    // pointed at a portal that had opened and timed out. It had done no such
    // thing: it joined a network immediately, and the only real evidence — the
    // GREEN "Seattle Makers" idle screen rather than the orange "Weigh Station /
    // Join WiFi" one — was buried under a screen that was lying.
    //
    // The state is now set where it is true: after autoConnect() has actually
    // raised the portal. The boot screen covers the join attempt.
    WiFiManager wm;
    // Drive the portal ourselves rather than letting WiFiManager block: its
    // built-in timeout either cuts off someone mid-password (what happened on
    // the bench) or, with setAPClientCheck(true), never fires while a phone
    // stays associated. Neither is acceptable on a cabinet-installed unit whose
    // BOOT button is unreachable — the portal MUST close on its own. See
    // runConfigPortal() for the idle/absolute policy.
    wm.setConfigPortalBlocking(false);
    wm.setConfigPortalTimeout(0);      // no internal timeout; we own the policy

    // Hold BOOT (GPIO 0) for WIFI_RESET_HOLD_MS to erase stored WiFi credentials
    // and force the captive portal to reopen — useful when moving the device to a
    // new network.
    pinMode(WIFI_RESET_PIN, INPUT_PULLUP);
    if (digitalRead(WIFI_RESET_PIN) == LOW) {
        uint32_t held = 0;
        while (digitalRead(WIFI_RESET_PIN) == LOW && held < WIFI_RESET_HOLD_MS) {
            vTaskDelay(pdMS_TO_TICKS(100));
            held += 100;
        }
        if (held >= WIFI_RESET_HOLD_MS) {
            Serial.println("WiFi reset: credentials cleared. Release BOOT to continue.");
            wm.resetSettings();
        }
    }

    // Join lab WiFi if provisioned; otherwise fall back to our own SoftAP so the
    // device stays usable (and the web app reachable) with no infrastructure.
    // In non-blocking mode autoConnect() returns immediately: true if stored
    // credentials worked, false once it has *started* the portal — so a false
    // here means "portal is up", not "failed". runConfigPortal() decides.
    bool joined = wm.autoConnect("WeighStation-Setup");

    // autoConnect() only raises the portal when it cannot join a saved network,
    // so a false here means "portal is up". Remember that: stopConfigPortal()
    // dereferences the portal's server/DNS objects and null-derefs if they were
    // never allocated — which is exactly what happens on a boot that connects
    // straight to a saved AP.
    const bool portalRan = !joined;
    if (portalRan) {
        // Only now is "Join WeighStation-Setup" a true statement.
        ctrlPost(CtrlEvent::WifiPortalUp);
        joined = runConfigPortal(wm);
    }

    // Release WiFiManager's portal web server before our own tries to bind :80.
    // Blocking autoConnect() does this internally on the way out; the
    // non-blocking path does NOT, so without this the portal keeps the port,
    // webAppBegin() fails to bind, and once WiFiManager's server goes away
    // nothing is listening at all — the browser gets ERR_CONNECTION_REFUSED.
    if (portalRan) {
        wm.stopConfigPortal();
        vTaskDelay(pdMS_TO_TICKS(200));   // let the socket actually close
    }

    if (!joined) {
        WiFi.mode(WIFI_AP);
        WiFi.softAP("WeighStation");
        strlcpy(gApSsid, "WeighStation", sizeof(gApSsid));
        WiFi.softAPIP().toString().toCharArray(gWebAddr, sizeof(gWebAddr));
        ctrlPost(CtrlEvent::WifiSoftAP);
        Serial.printf("[wifi] SoftAP '%s' — web app at http://%s\n",
                      gApSsid, gWebAddr);
    } else {
        gApSsid[0] = '\0';
        // Keep the radio awake. The ESP32 defaults to WIFI_PS_MIN_MODEM, which
        // sleeps between DTIM beacons and wakes to catch them — and when it
        // misses enough in a row the stack logs
        //   [W][WiFiGeneric.cpp] Reason: 200 - BEACON_TIMEOUT
        // and drops the link, taking the web app with it until it reassociates.
        //
        // That trade is wrong for this device. It is mains-powered and cabinet-
        // mounted, and it exists to answer HTTP requests at unpredictable
        // times; the ~30 mA saved is noise next to the TFT backlight and the
        // PN5180's RF field, while an unreachable web app is the whole product.
        WiFi.setSleep(false);
        WiFi.setAutoReconnect(true);
        // Start the clock. Asynchronous — this returns immediately and SNTP
        // answers a second or two later, so anything weighed in that window is
        // still stamped 1970 and files as "unknown". That is correct: those
        // grams genuinely have no known month.
        //
        // (0, 0, ...) is UTC with no DST. storeNowIso() formats with gmtime_r
        // and writes a trailing "Z", so an offset here would produce timestamps
        // that contradict their own zone marker.
        configTime(0, 0, NTP_SERVER_1, NTP_SERVER_2);
        // For display only (TFT corner clock, web-app timestamps via
        // storeLocalizeIso()) -- gmtime_r() (everything that gets LOGGED)
        // ignores TZ entirely, so this cannot touch stored timestamps.
        // configTime() above already calls setenv("TZ", ...) itself for a
        // fixed 0-offset zone; tzApply() overrides it right after with
        // whichever zone is configured on the Settings page (see
        // display_tz.h), same clock, same instant, just a DST-aware
        // reinterpretation of it. Re-applied here on every join because
        // nothing guarantees configTime() won't stomp the TZ env var again.
        tzApply();
        // Show the IP rather than the mDNS name: .local depends on the *client*
        // resolving it (Windows in particular is unreliable), while the IP works
        // from anything on the network. mDNS still runs, so weighstation.local
        // keeps working for clients that can resolve it.
        WiFi.localIP().toString().toCharArray(gWebAddr, sizeof(gWebAddr));
        ctrlPost(CtrlEvent::WifiJoined);
        Serial.printf("[wifi] joined '%s' — web app at http://%s  (or http://%s.local)\n",
                      WiFi.SSID().c_str(), gWebAddr, DEVICE_HOSTNAME);
    }
    // The web app runs regardless of station vs AP mode.
    webAppBegin();
    Serial.println("[web] server started on :80");

    // Station mode only — in SoftAP fallback there is no AP to measure, and
    // RSSI/BSSID would just print noise.
    if (!gApSsid[0]) logWifiState("link");
    WiFi.onEvent(onWifiDisconnected, ARDUINO_EVENT_WIFI_STA_DISCONNECTED);

    // Per-tag state, valid while a spool is on the scale.
    int     sSpoolId  = -1;
    OptMain sSnapshot = {};
    // Cached alongside sSnapshot for the same reason: the Holding-phase poll
    // below needs something cheap to diff the live store against, without a
    // tag re-read. Only cost needs this (not the rest of OptAuxiliary) --
    // consumed_weight is never store-driven, it's computed fresh each
    // placement.
    float   sCostSnapshot = 0;
    // True while the spool on the scale was ADOPTED from a tag someone else
    // wrote (valid OPT, not one we formatted). Provenance only: it is recorded
    // on the record as `foreign` and no longer blocks writes. Every tag gets its
    // Main reconciled and its Aux written the same way, whoever made it
    // (2026-09-30) — OPT is public, and writing it correctly is our job. The
    // read-only rule this used to enforce dates from 2026-08-14, when a rewrite
    // in our old encoding broke a Prusa tag; what made rewrites dangerous has
    // been fixed since (unmodelled keys pass through, write_protection is
    // honoured, writes stay inside the tag's declared regions, and absent
    // fields are never invented). See docs/design/onboarding-vocabulary.md.
    bool    sForeign  = false;

    // Link watch. A station-mode drop is otherwise completely silent: the
    // display keeps showing the address it had at boot, the QR keeps encoding
    // it, and the only symptom is a web app that stopped answering. Worse, DHCP
    // can hand back a DIFFERENT address on reassociation, so the shown one goes
    // from stale to wrong.
    bool wasUp = (WiFi.status() == WL_CONNECTED);

    // Phase 4: syncTask drives the weigh/reconcile flow off this LOCAL phase and
    // posts events; the controller writes the weigh states. Advancing the phase
    // synchronously — unlike gState, which the controller updates a beat later —
    // is what stops syncTask re-entering the Weighing block and appending a
    // DUPLICATE weigh, which would corrupt the consumption rollup (primary data).
    // Mapping: Resolving = ValidTagFound handling, Foreign = ForeignTagFound,
    // Registering = RegisteringForeignTag, Weighing = WeighingAndSync,
    // Holding = Present, Reconciling = ReconcilingMainSection. Idle = nothing on
    // the scale (the switch below resets to it whenever gState reads idle).
    enum class SyncPhase { Idle, Resolving, Foreign, Registering, Weighing,
                           Holding, Reconciling };
    SyncPhase sphase = SyncPhase::Idle;

    for (;;) {
        DeviceState state = getState();

        // Say when the clock lands. SNTP is asynchronous and silent, and the
        // difference between "no usage data yet" and "usage data filed under
        // unknown because the clock never set" is otherwise invisible until
        // someone reads the Usage page a month later and finds one row.
        if (!gClockSet && time(nullptr) > 1700000000L) {   // ~2023-11, i.e. real
            gClockSet = true;
            char iso[25];
            storeNowIso(iso, sizeof(iso));
            Serial.printf("[time] clock set from NTP: %s — usage now buckets by "
                          "real month\n", iso);
        }

        if (!gApSsid[0]) {                       // station mode only
            const bool up = (WiFi.status() == WL_CONNECTED);
            if (up != wasUp) {
                wasUp = up;
                if (up) {
                    // Re-apply: a reassociation can restore the driver default,
                    // and the whole point is that this radio never sleeps.
                    WiFi.setSleep(false);
                    char ip[48];
                    WiFi.localIP().toString().toCharArray(ip, sizeof(ip));
                    if (strcmp(ip, gWebAddr) != 0)
                        Serial.printf("[wifi] reconnected — address changed %s -> %s\n",
                                      gWebAddr, ip);
                    else
                        Serial.println("[wifi] reconnected");
                    strlcpy(gWebAddr, ip, sizeof(gWebAddr));
                    logWifiState("link");
                } else {
                    Serial.println("[wifi] link lost — web app unreachable until it "
                                   "reassociates (auto-reconnect is on)");
                }
            }
        }

        // ── Quiescent / boot states ───────────────────────────────────────────
        switch (state) {
            case DeviceState::Boot:
            case DeviceState::WiFiSetupMode:
            case DeviceState::TagDetecting:
            case DeviceState::TagReadError:
            case DeviceState::BlankTagFound:
            case DeviceState::AwaitingFormatConfirm:
            case DeviceState::FormattingAndRegistering:
                vTaskDelay(pdMS_TO_TICKS(100));
                continue;

            case DeviceState::Idle:
            case DeviceState::IdleNoWiFi:
                sSpoolId = -1; sSnapshot = {}; sCostSnapshot = 0;
                gSpoolId = -1; gSpoolNeedsOnboarding = false;
                sphase = SyncPhase::Idle;   // tag gone (or never arrived)
                sForeign = false;
                // If station WiFi comes up later, upgrade to Idle and switch the
                // shown address from the SoftAP IP to the mDNS hostname.
                if (state == DeviceState::IdleNoWiFi && WiFi.status() == WL_CONNECTED) {
                    gApSsid[0] = '\0';
                    // gWebAddr always holds the NUMERIC address. The display
                    // shows the .local hostname separately and the QR encodes
                    // the IP, because mDNS is the part that isn't universal.
                    // This used to write the hostname here and the IP at join
                    // time, so which one you saw depended on whether WiFi was
                    // up at boot — an accident, not a decision.
                    WiFi.localIP().toString().toCharArray(gWebAddr, sizeof(gWebAddr));
                    ctrlPost(CtrlEvent::WifiJoined);
                }
                // Event-log compaction, only while nothing is on the scale:
                // it rewrites the whole log and holds the store lock for the
                // duration, so it must never land mid-weigh.
                //
                // Throttled to once a minute rather than riding the ~1 Hz
                // reconcile tick. The check opens the log to stat it, and the
                // log takes months to reach the threshold — checking 60x more
                // often buys nothing and just churns the filesystem.
                //
                // Braced: `nowMs` has a runtime initialiser, and a bare
                // declaration in a case block that is followed by another case
                // label is a "jump to case label crosses initialization" error.
                {
                    static uint32_t lastCompactCheck = 0;
                    const uint32_t nowMs = millis();
                    if (nowMs - lastCompactCheck >= 60000UL) {
                        lastCompactCheck = nowMs;
                        if (storeCompactNeeded()) {
                            const size_t before = storeLogBytes();
                            Serial.printf("[store] compacting log (%u kB)…\n",
                                          (unsigned)(before >> 10));
                            const bool ok = storeCompact();
                            Serial.printf("[store] compaction %s: %u kB -> %u kB, "
                                          "%u lines, %u kB free\n",
                                          ok ? "ok" : "FAILED",
                                          (unsigned)(before >> 10),
                                          (unsigned)(storeLogBytes() >> 10),
                                          (unsigned)storeLogLineCount(),
                                          (unsigned)(storeFreeBytes() >> 10));
                        }
                    }
                }
                vTaskDelay(pdMS_TO_TICKS(RECONCILE_POLL_MS));
                continue;

            default:
                break;
        }

        // Reaching past the switch means gState is a weigh state (default case).
        // Enter the local flow on the first one; from here sphase advances
        // synchronously and syncTask no longer keys the flow on gState.
        if (sphase == SyncPhase::Idle) sphase = SyncPhase::Resolving;

        // ── Resolving (controller shows ValidTagFound) ────────────────────────
        // nfcTask confirmed an OPT tag. gTagMain is populated from the NFC read
        // (nil UUID = freshly formatted blank; real UUID = known or foreign spool).
        if (sphase == SyncPhase::Resolving) {
            xSemaphoreTake(gTagMutex, portMAX_DELAY);
            OptMain main = gTagMain;
            uint8_t physUid[8]; memcpy(physUid, gTagUid, 8);
            xSemaphoreGive(gTagMutex);
            char physHex[17]; uidToHex16(physUid, physHex);

            // "Foreign" (adopted) is a PROVENANCE fact, decided when the record
            // was created and carried on the record — NOT inferred from tag bytes.
            // It has to be: since our tags now match the OPT reference layout
            // byte-for-byte (2026-08-14), a genuine vendor tag is indistinguishable
            // from ours at the byte level. sForeign is therefore set per branch
            // below: false when we mint a blank, r.foreign for a known spool, and
            // true for a freshly adopted foreign tag (set in Registering).
            sForeign = false;

            if (isNilUUID(main.instance_uuid)) {
                // A blank we are about to format and mint — ours to write.
                sForeign = false;
                // Blank tag just formatted by nfcTask — mint an identity and a
                // local stub record. A person completes the details later in the
                // web form (Phase 4); the reconcile loop writes them back to the
                // tag while it's still on the scale.
                // This physical chip may have carried a different spool's
                // identity last time we saw it, if it's been blanked since —
                // by our own erase flow, TAGFORMAT, or a third-party NFC tool.
                // Either way the material that record tracked is gone, so
                // retire it now rather than leave it stuck showing stale
                // remaining weight forever with nothing left to trigger a
                // recheck.
                SpoolRecord prior;
                if (storeFindActiveByNfcUid(physHex, prior))
                    storeRetireSpool(prior.spool);

                // Erase mode: the retire above is the entire store-side job.
                // Deliberately mint NOTHING — no new instance_uuid, no stub
                // record, no needs_onboarding — so the tag is left genuinely,
                // fully blank and falls through this SAME isNilUUID path
                // again next time it's placed for real, rather than leaving
                // behind an "Unknown/Unknown, needs onboarding" placeholder
                // for material nobody has loaded yet. gSpoolId<=0 is already
                // a supported "nothing to reconcile" state for Holding below
                // (see its `if (sSpoolId > 0)` guard) and Present's
                // spoolId<=0 branch in display_task.cpp, so this needs
                // no new phase or display state — just don't take the
                // mint-a-stub path at all.
                if (gEraseModeActive) {
                    sSpoolId = -1; gSpoolId = -1; gSpoolNeedsOnboarding = false;
                    sSnapshot = {}; sCostSnapshot = 0;
                    gEraseModeActivityMs = millis();   // reset the idle auto-off clock
                    ctrlPost(CtrlEvent::Weighed);   // -> Present, same as a normal weigh
                    sphase = SyncPhase::Holding;
                    continue;
                }

                generateUUIDv4(main.instance_uuid);
                char hex[33]; uuidToHex32(main.instance_uuid, hex);

                StoreEvent e; e.ev = StoreEv::Onboard;
                strlcpy(e.uuid, hex, sizeof(e.uuid));
                strlcpy(e.vendor,   "Unknown", sizeof(e.vendor));
                strlcpy(e.material, "Unknown", sizeof(e.material));
                e.needs_ob = true;
                e.foreign  = false;   // we minted this tag — ours to write
                strlcpy(e.nfc_uid, physHex, sizeof(e.nfc_uid));
                e.spool = storeNextSpoolId();
                storeAppendEvent(e);

                sSpoolId = (int)e.spool;
                gSpoolId = sSpoolId;
                gSpoolNeedsOnboarding = true;

                // Stamp the new UUID (and the stub identity) onto the tag — but
                // only if it is ours to write (our layout). A nil-UUID tag with a
                // foreign layout is left untouched.
                SpoolRecord r;
                storeFindByUuid(hex, r);
                overlayRecordOntoMain(r, main);
                xSemaphoreTake(gTagMutex, portMAX_DELAY);
                gTagMain = main;
                xSemaphoreGive(gTagMutex);
                if (!sForeign) gWriteMainPending = true;

                // A brand-new stub still needs its FIRST weigh, same as any
                // other placement — skipping straight to Present/Holding here
                // left remaining_g/gross_g stuck at the StoreEvent zero
                // default forever, since nothing else ever weighs a spool
                // that already has an identity match on a later placement.
                // Found on the bench: onboarding a genuinely blank tag saved
                // 0 g until the spool was physically removed and re-placed,
                // which only worked because the SECOND placement takes the
                // "known spool" branch below — the one branch that already
                // did this correctly.
                sSnapshot = main;
                ctrlPost(CtrlEvent::BeginWeigh);
                sphase = SyncPhase::Weighing;

            } else {
                char hex[33]; uuidToHex32(main.instance_uuid, hex);
                SpoolRecord r;
                if (storeFindByUuid(hex, r)) {
                    // Known spool. Push any web-side identity edits down to the tag.
                    sSpoolId = (int)r.spool;
                    gSpoolId = sSpoolId;
                    gSpoolNeedsOnboarding = r.needs_ob;
                    // Ownership comes from the record, set when it was created.
                    sForeign = r.foreign;

                    OptMain updated = main;
                    overlayRecordOntoMain(r, updated);
                    if (recordDiffersFromMain(r, main)) {
                        xSemaphoreTake(gTagMutex, portMAX_DELAY);
                        gTagMain = updated;
                        xSemaphoreGive(gTagMutex);
                        gWriteMainPending = true;
                    }

                    // Same reconcile, for cost, onto Aux -- catches a price
                    // entered (or edited) on the web form while this spool sat
                    // off the scale. gTagAux already reflects THIS physical
                    // tag's own current Aux (nfcTask set it from the decode
                    // moments ago), so comparing against it, not sSnapshot,
                    // matches the tag's actual state rather than whatever the
                    // last placement happened to leave cached.
                    xSemaphoreTake(gTagMutex, portMAX_DELAY);
                    OptAuxiliary auxNow = gTagAux;
                    xSemaphoreGive(gTagMutex);
                    if (recordDiffersFromAux(r, auxNow)) {
                        overlayRecordOntoAux(r, auxNow);
                        xSemaphoreTake(gTagMutex, portMAX_DELAY);
                        gTagAux = auxNow;
                        xSemaphoreGive(gTagMutex);
                        gWriteAuxPending = true;
                    }
                    sCostSnapshot = r.cost;

                    sSnapshot = updated;
                    ctrlPost(CtrlEvent::BeginWeigh);
                    sphase = SyncPhase::Weighing;
                } else {
                    ctrlPost(CtrlEvent::SpoolForeign);
                    sphase = SyncPhase::Foreign;
                }
            }
            continue;
        }

        // ── Foreign → Registering (controller shows ForeignTagFound) ──────────
        if (sphase == SyncPhase::Foreign) {
            ctrlPost(CtrlEvent::ForeignRegistering);
            sphase = SyncPhase::Registering;
            continue;
        }

        // A well-formed tag we've never seen (genuine Prusament, another maker's
        // tooling). Decode its own Main data and create a local record from it.
        if (sphase == SyncPhase::Registering) {
            xSemaphoreTake(gTagMutex, portMAX_DELAY);
            OptMain main = gTagMain;
            uint8_t physUid[8]; memcpy(physUid, gTagUid, 8);
            xSemaphoreGive(gTagMutex);
            char physHex[17]; uidToHex16(physUid, physHex);

            const bool wasNil = isNilUUID(main.instance_uuid);
            if (wasNil) generateUUIDv4(main.instance_uuid);
            char hex[33]; uuidToHex32(main.instance_uuid, hex);

            // A tag reaching adoption with a real UUID is a genuine foreign spool,
            // recorded as such (provenance; it is written like any other tag).
            // The nil-UUID case — one of ours after a store wipe — is not.
            sForeign = !wasNil;

            // Resolve the product this spool is an instance of, creating one
            // (provisional) if we have never seen this filament. This is what
            // makes an inventory of four genuine Prusament spools roll up as one
            // product instead of four identical rows — the second spool finds
            // the product the first one created.
            //
            // Adoption never UPDATES an existing product: a product edit
            // propagates to every tag of that product, so one odd or damaged tag
            // could otherwise rewrite a whole shelf. A disagreement is logged for
            // a human to adjudicate and nothing is written.
            ProductRecord probe;
            productFromMain(main, probe);
            bool differs = false;
            const uint32_t pid = storeAdoptProduct(probe, &differs);
            if (differs)
                Serial.printf("[sync] tag %s disagrees with product #%u "
                              "(%s / %s) — product left as-is, tag adopted\n",
                              hex, (unsigned)pid, probe.vendor, probe.material);

            StoreEvent e; e.ev = StoreEv::Onboard;
            strlcpy(e.uuid, hex, sizeof(e.uuid));
            identityFromMain(main, e);
            e.needs_ob = false;
            e.foreign  = sForeign;   // adopted from someone else's tag (provenance)
            strlcpy(e.nfc_uid, physHex, sizeof(e.nfc_uid));
            e.product  = pid;
            e.spool = storeNextSpoolId();
            storeAppendEvent(e);

            sSpoolId = (int)e.spool;
            gSpoolId = sSpoolId;
            gSpoolNeedsOnboarding = false;

            // Write the minted UUID back only if the tag arrived with a nil UUID
            // (equivalently !sForeign here) — the one thing adoption itself
            // changes. A tag with its own UUID needs no write: the record was
            // just built from it, so the two already agree. Later edits reach it
            // through the normal reconcile, like any other tag.
            if (wasNil && !sForeign) {
                xSemaphoreTake(gTagMutex, portMAX_DELAY);
                memcpy(gTagMain.instance_uuid, main.instance_uuid, 16);
                xSemaphoreGive(gTagMutex);
                gWriteMainPending = true;
            }

            sSnapshot = main;
            ctrlPost(CtrlEvent::BeginWeigh);
            sphase = SyncPhase::Weighing;
            continue;
        }

        // ── Weighing (controller shows WeighingAndSync) ───────────────────────
        // Weigh ONCE; write remaining/used to both the tag Aux and the log. sphase
        // advances to Holding synchronously below, so this block cannot re-run for
        // the same placement even while gState still reads WeighingAndSync — which
        // is exactly the duplicate-weigh the local phase exists to prevent.
        if (sphase == SyncPhase::Weighing) {
            xSemaphoreTake(gTagMutex, portMAX_DELAY);
            OptMain main = gTagMain;
            xSemaphoreGive(gTagMutex);

            xSemaphoreTake(gWeightMutex, portMAX_DELAY);
            float weight = gWeightGrams;
            xSemaphoreGive(gWeightMutex);

            float remaining = (main.empty_container_weight > 0.0f)
                            ? weight - main.empty_container_weight
                            : weight;
            if (remaining < 0.0f) remaining = 0.0f;

            float used = (main.actual_netto_full_weight > 0.0f)
                       ? main.actual_netto_full_weight - remaining
                       : 0.0f;
            if (used < 0.0f) used = 0.0f;

            xSemaphoreTake(gTagMutex, portMAX_DELAY);
            gTagAux.consumed_weight = used;
            xSemaphoreGive(gTagMutex);
            // Every tag, ours or adopted: OPT requires Aux to stay writable, and
            // consumed_weight is what Prusa software reads remaining from.
            gWriteAuxPending = true;

            StoreEvent w; w.ev = StoreEv::Weigh;
            char hex[33]; uuidToHex32(main.instance_uuid, hex);
            strlcpy(w.uuid, hex, sizeof(w.uuid));
            w.spool       = (sSpoolId > 0) ? (uint32_t)sSpoolId : 0;
            w.gross_g     = weight;
            w.remaining_g = remaining;
            w.used_g      = used;
            storeAppendEvent(w);

            ctrlPost(CtrlEvent::Weighed);
            sphase = SyncPhase::Holding;
            continue;
        }

        // ── Reconciling (controller shows ReconcilingMainSection) ─────────────
        // nfcTask does the physical Main write and posts ReconcileDone; the
        // controller then shows Present again. Watch for that and resume Holding.
        if (sphase == SyncPhase::Reconciling) {
            if (state == DeviceState::Present) sphase = SyncPhase::Holding;
            vTaskDelay(pdMS_TO_TICKS(RECONCILE_POLL_MS));
            continue;
        }

        // ── Holding (controller shows Present) ────────────────────────────────
        // Steady state: poll the local store (cheap) and, if a web-side edit has
        // changed this spool's identity since placement, rewrite the tag's Main.
        if (sphase == SyncPhase::Holding) {
            if (sSpoolId > 0) {
                char hex[33];
                xSemaphoreTake(gTagMutex, portMAX_DELAY);
                uuidToHex32(gTagMain.instance_uuid, hex);
                xSemaphoreGive(gTagMutex);

                SpoolRecord r;
                if (storeFindByUuid(hex, r)) {
                    gSpoolNeedsOnboarding = r.needs_ob;
                    if (recordDiffersFromMain(r, sSnapshot)) {
                        OptMain updated;
                        xSemaphoreTake(gTagMutex, portMAX_DELAY);
                        updated = gTagMain;
                        overlayRecordOntoMain(r, updated);
                        gTagMain = updated;
                        xSemaphoreGive(gTagMutex);
                        gWriteMainPending = true;
                        sSnapshot = updated;
                        ctrlPost(CtrlEvent::NeedsReconcile);
                        sphase = SyncPhase::Reconciling;
                    }
                    // Same idea for cost, but deliberately NOT routed through
                    // Reconciling: that phase only exits when nfcTask posts
                    // ReconcileDone after a MAIN write specifically (see its
                    // handler above), so an Aux-only change would never clear
                    // it and the display would stick on "Updating tag..."
                    // forever. Aux writes are already a silent background
                    // thing everywhere else (consumed_weight updates every
                    // weigh with no display transition at all) -- this stays
                    // consistent with that instead of inventing a second kind
                    // of reconcile just for cost.
                    if (r.cost != sCostSnapshot) {
                        OptAuxiliary updatedAux;
                        xSemaphoreTake(gTagMutex, portMAX_DELAY);
                        updatedAux = gTagAux;
                        overlayRecordOntoAux(r, updatedAux);
                        gTagAux = updatedAux;
                        xSemaphoreGive(gTagMutex);
                        gWriteAuxPending = true;
                        sCostSnapshot = r.cost;
                    }
                }
            }
            vTaskDelay(pdMS_TO_TICKS(RECONCILE_POLL_MS));
            continue;
        }

        // Any unhandled state falls through to a slow idle poll.
        vTaskDelay(pdMS_TO_TICKS(RECONCILE_POLL_MS));
    }
}
