NormSohl/openprinttag-weigh-station/src/config_store.h

// SPDX-License-Identifier: GPL-3.0-or-later
// Copyright (C) 2026 Norm Sohl

#pragma once
#include <Arduino.h>
#include <stdint.h>

// Config catalog (redesign Phase 3). Web-editable reference tables on
// LittleFS that make onboarding pick-not-type and drive reordering.
// Files: /config/{vendors,materials,spool-profiles,colors,stock-items}.json
// Loaded once at boot (seeded with defaults if missing). Small, hand-edited
// data — held in RAM, rewritten whole on save.

struct CfgMaterial {
    char    name[48];   // "PETG"
    char    abbr[16];   // "PETG"
    int8_t  cls;        // material_class enum (OPT key 8)
    int8_t  type;       // material_type enum  (OPT key 9)
    float   dia;        // 1.75
    int16_t print_min, print_max;   // °C (OPT keys 34/35)
    int16_t bed_min,   bed_max;     // °C (OPT keys 37/38)
};

struct CfgProfile {     // a spool "size" → tare + nominal-full
    char  label[48];    // "Prusament 1kg PETG"
    float nominal_full_g;
    float empty_g;
};

struct CfgColor {
    char    name[32];   // "Prusa Orange"
    uint8_t rgba[4];
};

struct CfgStock {       // a standard-stock SKU to keep + reorder threshold
    // Stable, permanent, NVS-counter-backed, never reused -- same reasoning
    // as store.cpp's spool/product ids. This table used to be addressed by
    // array POSITION (cfgStockAt()'s index), which was fine only "for the
    // lifetime of one page load" (its own now-stale comment said so) — the
    // instant a second add/delete happened anywhere (another browser tab,
    // this session's own testing, even just a normal second person editing)
    // before an already-open Edit page was submitted, that position no
    // longer pointed at the row the user meant. Found live: an Edit that
    // silently became an Add (the stale index made cfgStockAt() fail,
    // handleStockPage() fell back to rendering an "Add" form with the
    // manual picklists still defaulting from last-used memory, so it LOOKED
    // pre-filled) — the row meant to be edited was untouched, and a near-
    // duplicate row was created instead.
    uint32_t id;
    char     vendor[48];
    char     material[48];
    char     color[32];
    float    dia;
    float    spool_g;       // nominal full weight of one spool
    uint16_t min_spools;    // reorder threshold (0 = use min_grams)
    float    min_grams;     // alt threshold (0 = use min_spools)
    char     sku[32];
    char     gtin[16];
    uint8_t  pack_qty;
    // Which product this row was picked as, at add/edit time (0 = free-typed,
    // no product on file yet). vendor/material/dia/spool_g above are still
    // populated either way -- for display and CSV export -- but when this is
    // set, rollUp() (web_app.cpp) matches spools by this id directly instead
    // of recomposing vendor+material into a name probe. The probe is exactly
    // what breaks silently: a Stock row's bare material ("PLA") + color
    // ("Fire Engine Red") does not reconstruct a real product's actual name
    // ("PLA Basic Fire Engine Red") if nobody ever typed "Basic" into the
    // Stock List, even though it is the same filament on the same shelf.
    // Picking the product directly is immune to that, and to any later
    // rename via /product?id=N (the FK still resolves; a stale re-typed name
    // would not).
    uint32_t product;
};
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
